vertical-cloud-lab/tensegrity-optimization/proposal-diff.tex

\documentclass[11pt]{article}
%DIF LATEXDIFF DIFFERENCE FILE
%DIF DEL /tmp/proposal-orig.tex   Mon Mar 16 17:47:02 2026
%DIF ADD proposal.tex             Mon Mar 16 17:11:21 2026

% --- Packages ---
\usepackage[margin=1in]{geometry}
\usepackage{amsmath,amssymb}
\usepackage{graphicx}
\usepackage[hidelinks]{hyperref}
\usepackage{natbib}
\usepackage{booktabs}
\usepackage{enumitem}
\usepackage{xcolor}
\usepackage{siunitx}
\usepackage{subcaption}
\usepackage{titlesec}
\usepackage{setspace}
\usepackage{wrapfig}

% --- Formatting ---
\titleformat{\section}{\normalfont\Large\bfseries}{\thesection}{1em}{}
\titleformat{\subsection}{\normalfont\large\bfseries}{\thesubsection}{1em}{}
\setlength{\parskip}{0.5em}
\setlength{\parindent}{0em}

% --- Draft helpers (remove for final) ---
\newcommand{\todo}[1]{\textcolor{red}{\textbf{[TODO: #1]}}}
\newcommand{\note}[1]{\textcolor{blue}{\textbf{[NOTE: #1]}}}
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
\providecommand{\DIFdelFL}[1]{\DIFdel{#1}} %DIF PREAMBLE
\providecommand{\DIFaddbeginFL}{} %DIF PREAMBLE
\providecommand{\DIFaddendFL}{} %DIF PREAMBLE
\providecommand{\DIFdelbeginFL}{} %DIF PREAMBLE
\providecommand{\DIFdelendFL}{} %DIF PREAMBLE
%DIF HYPERREF PREAMBLE %DIF PREAMBLE
\providecommand{\DIFadd}[1]{\texorpdfstring{\DIFaddtex{#1}}{#1}} %DIF PREAMBLE
\providecommand{\DIFdel}[1]{\texorpdfstring{\DIFdeltex{#1}}{}} %DIF PREAMBLE
\newcommand{\DIFscaledelfig}{0.5}
%DIF HIGHLIGHTGRAPHICS PREAMBLE %DIF PREAMBLE
\RequirePackage{settobox} %DIF PREAMBLE
\RequirePackage{letltxmacro} %DIF PREAMBLE
\newsavebox{\DIFdelgraphicsbox} %DIF PREAMBLE
\newlength{\DIFdelgraphicswidth} %DIF PREAMBLE
\newlength{\DIFdelgraphicsheight} %DIF PREAMBLE
% store original definition of \includegraphics %DIF PREAMBLE
\LetLtxMacro{\DIFOincludegraphics}{\includegraphics} %DIF PREAMBLE
\newcommand{\DIFaddincludegraphics}[2][]{{\color{blue}\fbox{\DIFOincludegraphics[#1]{#2}}}} %DIF PREAMBLE
\newcommand{\DIFdelincludegraphics}[2][]{% %DIF PREAMBLE
\sbox{\DIFdelgraphicsbox}{\DIFOincludegraphics[#1]{#2}}% %DIF PREAMBLE
\settoboxwidth{\DIFdelgraphicswidth}{\DIFdelgraphicsbox} %DIF PREAMBLE
\settoboxtotalheight{\DIFdelgraphicsheight}{\DIFdelgraphicsbox} %DIF PREAMBLE
\scalebox{\DIFscaledelfig}{% %DIF PREAMBLE
\parbox[b]{\DIFdelgraphicswidth}{\usebox{\DIFdelgraphicsbox}\\[-\baselineskip] \rule{\DIFdelgraphicswidth}{0em}}\llap{\resizebox{\DIFdelgraphicswidth}{\DIFdelgraphicsheight}{% %DIF PREAMBLE
\setlength{\unitlength}{\DIFdelgraphicswidth}% %DIF PREAMBLE
\begin{picture}(1,1)% %DIF PREAMBLE
\thicklines\linethickness{2pt} %DIF PREAMBLE
{\color[rgb]{1,0,0}\put(0,0){\framebox(1,1){}}}% %DIF PREAMBLE
{\color[rgb]{1,0,0}\put(0,0){\line( 1,1){1}}}% %DIF PREAMBLE
{\color[rgb]{1,0,0}\put(0,1){\line(1,-1){1}}}% %DIF PREAMBLE
\end{picture}% %DIF PREAMBLE
}\hspace*{3pt}}} %DIF PREAMBLE
} %DIF PREAMBLE
\LetLtxMacro{\DIFOaddbegin}{\DIFaddbegin} %DIF PREAMBLE
\LetLtxMacro{\DIFOaddend}{\DIFaddend} %DIF PREAMBLE
\LetLtxMacro{\DIFOdelbegin}{\DIFdelbegin} %DIF PREAMBLE
\LetLtxMacro{\DIFOdelend}{\DIFdelend} %DIF PREAMBLE
\DeclareRobustCommand{\DIFaddbegin}{\DIFOaddbegin \let\includegraphics\DIFaddincludegraphics} %DIF PREAMBLE
\DeclareRobustCommand{\DIFaddend}{\DIFOaddend \let\includegraphics\DIFOincludegraphics} %DIF PREAMBLE
\DeclareRobustCommand{\DIFdelbegin}{\DIFOdelbegin \let\includegraphics\DIFdelincludegraphics} %DIF PREAMBLE
\DeclareRobustCommand{\DIFdelend}{\DIFOaddend \let\includegraphics\DIFOincludegraphics} %DIF PREAMBLE
\LetLtxMacro{\DIFOaddbeginFL}{\DIFaddbeginFL} %DIF PREAMBLE
\LetLtxMacro{\DIFOaddendFL}{\DIFaddendFL} %DIF PREAMBLE
\LetLtxMacro{\DIFOdelbeginFL}{\DIFdelbeginFL} %DIF PREAMBLE
\LetLtxMacro{\DIFOdelendFL}{\DIFdelendFL} %DIF PREAMBLE
\DeclareRobustCommand{\DIFaddbeginFL}{\DIFOaddbeginFL \let\includegraphics\DIFaddincludegraphics} %DIF PREAMBLE
\DeclareRobustCommand{\DIFaddendFL}{\DIFOaddendFL \let\includegraphics\DIFOincludegraphics} %DIF PREAMBLE
\DeclareRobustCommand{\DIFdelbeginFL}{\DIFOdelbeginFL \let\includegraphics\DIFdelincludegraphics} %DIF PREAMBLE
\DeclareRobustCommand{\DIFdelendFL}{\DIFOaddendFL \let\includegraphics\DIFOincludegraphics} %DIF PREAMBLE
%DIF COLORLISTINGS PREAMBLE %DIF PREAMBLE
\RequirePackage{listings} %DIF PREAMBLE
\RequirePackage{color} %DIF PREAMBLE
\lstdefinelanguage{DIFcode}{ %DIF PREAMBLE
%DIF DIFCODE_UNDERLINE %DIF PREAMBLE
  moredelim=[il][\color{red}\sout]{\%DIF\ <\ }, %DIF PREAMBLE
  moredelim=[il][\color{blue}\uwave]{\%DIF\ >\ } %DIF PREAMBLE
} %DIF PREAMBLE
\lstdefinestyle{DIFverbatimstyle}{ %DIF PREAMBLE
	language=DIFcode, %DIF PREAMBLE
	basicstyle=\ttfamily, %DIF PREAMBLE
	columns=fullflexible, %DIF PREAMBLE
	keepspaces=true %DIF PREAMBLE
} %DIF PREAMBLE
\lstnewenvironment{DIFverbatim}{\lstset{style=DIFverbatimstyle}}{} %DIF PREAMBLE
\lstnewenvironment{DIFverbatim*}{\lstset{style=DIFverbatimstyle,showspaces=true}}{} %DIF PREAMBLE
%DIF END PREAMBLE EXTENSION ADDED BY LATEXDIFF

\begin{document}

% --- Cover Page (does not count toward 5-page limit) ---
\input{sections/coverpage}

% =============================================================================
\section{Research Motivation and Overview}
% =============================================================================

We propose a two-year \textbf{experiment-driven} mentored research program in
which 2 undergraduate students design, fabricate, and test \textbf{multi-material
3D-printed tensegrity-inspired structures} for energy absorption.  Tensegrity
structures---assemblies of rigid compression members
suspended within a continuous network of tension members---exhibit remarkable
strength-to-weight ratios and tunable mechanical responses, making them
attractive for protective equipment, packaging, and aerospace applications
\citep{skelton2009tensegrity}.
Recent work has shown that \emph{tensegrity-inspired} architectures can be
directly 3D-printed and retain desirable load-limiting behavior under impact
\citep{pajunen2019design}.  Because multimaterial FDM TPU elements are not
ideal cables, we target architectures that reproduce key
tensegrity-like mechanical responses while remaining manufacturable; notably,
TPU's rate-dependent damping is an \emph{asset} for energy absorption rather
than merely a deviation from idealized behavior.

% --- Overview figure (right-inset, floatable) ---
\begin{wrapfigure}{R}{0.62\textwidth}
\centering
\vspace{-1em}
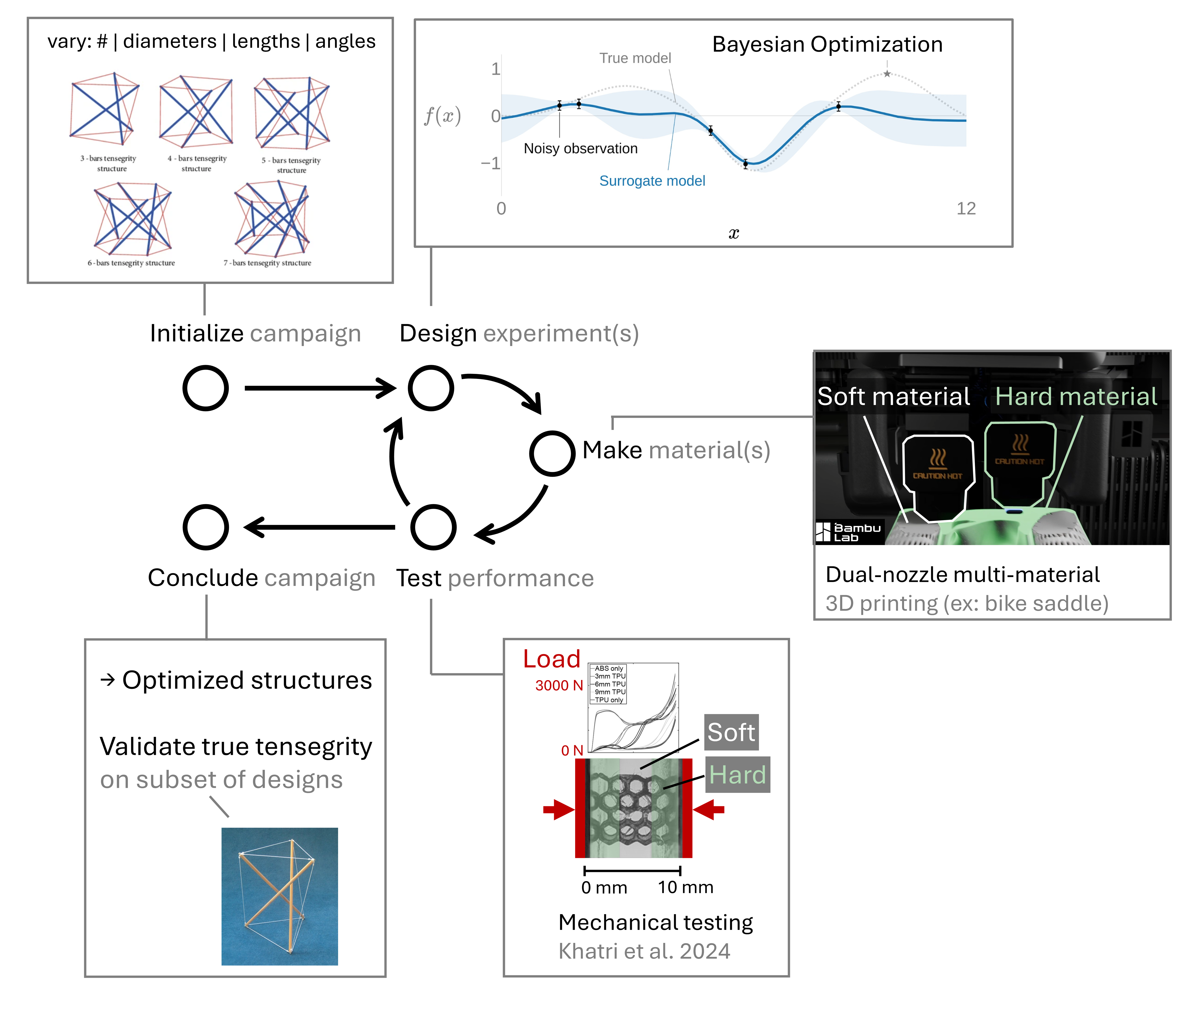
[picture p4: figures/overview-updated.png]

\captionsetup{font=small}
\caption{Research framework overview. Students design, print, and test tensegrity-inspired specimens in a closed-loop Bayesian optimization cycle that recommends the next designs to fabricate. Performance is evaluated via quasi-static compression and drop-weight impact tests.}
\label{fig:overview}
\end{wrapfigure}

Multi-material 3D printing with PLA (rigid struts) and TPU (flexible tension
elements) enables rapid fabrication of diverse tensegrity-inspired geometries
\citep{ye2023multimaterial, khatri2024energy}.  Rather
than relying on costly simulations, we leverage this manufacturing
agility for a \textbf{high-throughput experimental approach}: students
will print, test, and iterate on many candidate designs---we estimate 50--100+
unique specimens over two years---generating high-quality physical data
directly.  \textbf{Bayesian optimization} (BO) will guide the experimental
search, selecting the most informative designs to test next based on
prior results \citep{shahriari2016taking, frazier2018tutorial}.  This
experiment-first strategy produces reliable performance data while
keeping the project accessible to undergraduates where students can
contribute meaningfully through hands-on printing and testing without
advanced modeling expertise.

\textbf{A primary objective is to provide a rich,
interdisciplinary mentored research experience for undergraduates.}  Through
weekly one-on-one mentoring, structured lab meetings, and progressive
scaffolding from guided tasks to independent research
ownership, each student will gain skills in CAD, multi-material 3D
printing, mechanical testing, and data-driven optimization. Each student will define design variables, execute experimental campaigns, analyze data, present results, and draft manuscript sections.

% =============================================================================
\section{Background}
% =============================================================================

\textbf{Tensegrity structures} consist of isolated compression members (struts)
held in equilibrium by a continuous network of tension members
\citep{skelton2009tensegrity, sultan2009tensegrity}.  Their defining
characteristic---no two rigid bars touch---yields lightweight assemblies with
surprising load-bearing capacity and tunable nonlinear responses
\citep{amendola2014experimental, zhang2018tensegrity}.
Pajunen et al.\ \citep{pajunen2019design} demonstrated that
\emph{tensegrity-inspired} unit cells can be directly 3D-printed and exhibit
load-limiting plateaus under drop-weight impact.
Multi-material rigid--soft printing
\citep{ye2023multimaterial, khatri2024energy} has shown that PLA--TPU
combinations on a single FDM platform achieve tunable energy
absorption via a wrapping-based strategy (rigid cores
encapsulated by continuous soft skins) that prevents interface delamination and
enables cyclic durability---a critical enabler for our fabrication approach.

\textbf{Bayesian optimization} (BO) is a sequential, model-based strategy for
optimizing expensive black-box functions using a Gaussian process surrogate
\citep{shahriari2016taking, frazier2018tutorial}.  BO has driven breakthroughs
across domains---from tuning hyperparameters of AlphaGo
\citep{silver2016mastering} to optimizing sustainable concrete formulations
\citep{ament2023sustainable} and discovering organic laser
emitters \citep{striethkalthoff2024delocalized}---and has been applied to
metamaterial design \citep{mo2023accelerated}.  In our framework, BO operates
\emph{directly on experimental data}: each round of printing and testing
updates a Gaussian process surrogate, which recommends the next designs to fabricate.  This closed-loop
print--test--optimize cycle eliminates the need for simulation and
keeps the workflow centered on physical experimentation---naturally suited to mentoring undergraduates.

% =============================================================================
\section{Student Research Project~1: Design, Fabrication, and Testing}
% =============================================================================

\textbf{Student profile:} One sophomore or junior undergraduate.  No prior
simulation or advanced modeling experience is required; the hands-on nature of
this project makes it an ideal entry point for students early in their studies.

\subsection*{Scope and Deliverables}

This student will lead the design-and-build cycle that forms the experimental
backbone of the project.  Working under weekly mentoring from
Prof.~Hill, the student will \textbf{parameterize a family of
tensegrity-inspired unit cells} in CAD (SolidWorks or Fusion~360), defining key
variables---strut diameter and length (PLA), tension-element cross-section
(TPU), connectivity topology, and unit-cell tiling---that span the design space.
Following \citet{ye2023multimaterial}, the designs use a core-wrapping strategy
(rigid PLA struts encapsulated by continuous TPU skins) to ensure robust
mechanical interlocking. PLA--TPU interface robustness will be validated during early print trials.

The student will then \textbf{fabricate structures} using the department's
multi-material FDM printer, iterating on print parameters
to achieve reliable geometries.
The student works closely with Student~2, who tests each
batch and returns performance data.
Prof.~Baird's master's student serves as a day-to-day co-mentor,
guiding equipment operation and troubleshooting.

\textbf{Mentoring outcomes:} The student will develop skills in CAD,
multi-material additive manufacturing, and systematic experimental design.
Structured mentoring scaffolds move the student from guided replication of
existing designs to independent creation of novel geometries by mid-Year~1.
The student will present results at \textbf{UCUR} or \textbf{ASME IDETC} and
contribute as co-author on a journal manuscript.

% =============================================================================
\section{Student Research Project~2: Mechanical Testing and Data-Driven Optimization}
% =============================================================================

\textbf{Student profile:} One sophomore, junior, or senior undergraduate with
coursework or interest in mechanics of materials or data analysis.

\subsection*{Scope and Deliverables}

This student will lead physical testing and the Bayesian optimization
campaign, working under weekly one-on-one mentoring from Prof.~Baird.  The work
begins with \textbf{experimental testing} on structures fabricated by
Student~1: quasi-static compaction and drop-weight impact tests following
\citet{pajunen2019design}.  Primary metrics include \emph{peak transmitted
force}, \emph{specific energy absorption} (SEA), and \emph{compaction
efficiency}.

With initial data in hand, the student will \textbf{implement a BO loop}
(BoTorch/Ax) that operates directly
on experimental measurements.  After each iteration the surrogate recommends
the next batch of designs; the student coordinates with Student~1 to print and
test them, closing the loop.  If time permits,
lightweight simulations may be added as a low-fidelity data
source to accelerate convergence \citep{mo2023accelerated}, but the campaign
does not depend on simulation.

Prof.~Baird's master's student provides day-to-day co-mentoring in Python,
data analysis, and BO implementation.
In Year~2, both students mentor newly recruited undergraduates, reinforcing
their own understanding while sustaining the research pipeline.

\textbf{Mentoring outcomes:} The student will develop skills in experimental
mechanics (test design, data acquisition), scientific computing (Python),
and data-driven optimization.  They will present results at \textbf{ASME IDETC}
or \textbf{UCUR} and contribute as co-author on a journal manuscript.

% =============================================================================
\section{Mentoring Environment}
\label{sec:mentoring}
% =============================================================================

Each student follows a structured path from guided exploration
to independent research ownership, supported by layered mentoring.
Because the project centers on hands-on experimentation---designing,
printing, and testing physical structures---students engage with tangible
problems from day one.

\subsection*{Recruitment}

Students will be recruited from courses in mechanics of materials, machine
design, kinematics, and compliant mechanisms, targeting sophomores through
seniors.  The experiment-driven nature of the project lowers the barrier to
entry: students need not have prior simulation or programming experience.

\subsection*{Mentoring Structure}

Students meet individually with Profs.~Hill and Baird each week (30~min) for
technical guidance and professional development, and participate in weekly lab
group meetings (1~hr) that include progress updates, literature
presentations, and skill-building workshops on scientific writing,
presentation skills, and research ethics.  Prof.~Baird's master's student
serves as a graduate co-mentor, providing day-to-day guidance in 3D printing,
testing, coding, and data interpretation.
Students begin with structured tasks---replicating known tensegrity
geometries and running standard test protocols---and progress to independent
design decisions, culminating in ownership of their research project. Year~1 focuses on skill acquisition and guided execution; Year~2 emphasizes independent hypothesis generation, experimental design, and peer mentoring of newly recruited sophomores.

\subsection*{Student Development Outcomes}

Mentoring is structured around concrete milestones:
a student's first successful multi-material print, first compression test,
first data set fed into the BO loop.  \emph{Technical} skills include
experimental mechanics, additive manufacturing (CAD, multi-material 3D printing),
and data-driven optimization (Python, Bayesian optimization).
\emph{Communication} skills develop through lab notebooks, group presentations,
conference talks, and co-authoring a peer-reviewed manuscript.
\emph{Professional} development includes project management, data-driven
decision-making, interdisciplinary collaboration, and preparation for graduate
school or industry careers.

% =============================================================================
\section{Expected Research Outcomes}
% =============================================================================

The primary outcome is the \textbf{training of 2 undergraduate
researchers} with hands-on experience in multi-material 3D printing, mechanical
testing, and data-driven optimization. Each undergraduate is expected to have
participated in the design and testing of approximately 100+ tensegrity
specimens, contributed to \textbf{conference presentations} at UCUR
and ASME IDETC, and co-authored a peer-reviewed manuscript
submitted to the \emph{ASME Journal of Mechanical Design} or \emph{Smart
Materials and Structures}. The
experimental data set---spanning a wide range of tensegrity-inspired geometries
with measured energy-absorption performance---will be published on GitHub
for reproducibility.  In Year~2, students will
mentor incoming undergraduates, developing leadership skills and creating a
self-sustaining research group.

% =============================================================================
\section{Potential Impact of Work}
% =============================================================================

This project advances architected material design for energy absorption with
applications in \textbf{protective equipment} (helmets, body armor),
\textbf{packaging} (shock-absorbing inserts), and \textbf{aerospace}
(lightweight impact-resistant structures).  The systematically collected
experimental data set provides the community with a resource for benchmarking
and further optimization.  The experiment-driven BO framework
demonstrates that undergraduates can drive a closed-loop
experimental campaign, establishing a replicable mentoring model for
data-driven research.  Open-source dissemination of data, code, and tested designs extends
impact beyond BYU.

% =============================================================================
\section{Timeline}
% =============================================================================

The project spans two academic years plus two summers (Table~\ref{tab:timeline}).
\textbf{Year~1} focuses on experimental foundations: recruitment and
onboarding in Fall, literature review and CAD parameterization through Winter, and a Summer term of full-time research with intensive
mentoring where students ramp up
fabrication, run systematic compression and impact
tests, and begin feeding results into the BO loop.
\textbf{Year~2} shifts to optimization and dissemination: BO-guided
campaigns continue through Fall and Winter with progressively refined designs.  Students present at UCUR
and ASME IDETC, and a journal manuscript is prepared during Winter
and Summer.  Experienced students mentor newly recruited
undergraduates throughout Year~2.

\begin{table}[ht]
\centering
\small
\begin{tabular}{@{}lccccccc@{}}
\toprule
\textbf{Task} & \textbf{Y1 F} & \textbf{Y1 W} & \textbf{Y1 Su} & \textbf{Y2 F} & \textbf{Y2 W} & \textbf{Y2 Su} \\
\midrule
Student recruitment \& onboarding    & \(\bullet\) &           &           &           &           &           \\
Literature review                     & \(\bullet\) & \(\bullet\) &           &           &           &           \\
Tensegrity parameterization \& CAD   & \(\bullet\) & \(\bullet\) &           &           &           &           \\
Print trials \& process validation   & \(\bullet\) & \(\bullet\) & \(\bullet\) &           &           &           \\
Multi-material 3D printing campaigns &             & \(\bullet\) & \(\bullet\) & \(\bullet\) & \(\bullet\) &           \\
Compression \& impact testing        &             & \(\bullet\) & \(\bullet\) & \(\bullet\) & \(\bullet\) &           \\
Bayesian optimization loop           &             &             & \(\bullet\) & \(\bullet\) & \(\bullet\) &           \\
Conference presentations (UCUR/IDETC)&             &             &             & \(\bullet\) & \(\bullet\) &           \\
Journal manuscript preparation       &             &             &             &             & \(\bullet\) & \(\bullet\) \\
Peer mentoring of new students       &             &             &             & \(\bullet\) & \(\bullet\) &           \\
\bottomrule
\end{tabular}
\caption{Project timeline across two years (F = Fall, W = Winter, Su = Summer).  Summer terms support full-time research with intensive mentoring. Year 2 includes formal peer mentoring, where experienced students supervise newly recruited undergraduates.}
\label{tab:timeline}
\end{table}

% =============================================================================
\section{Budget}
% =============================================================================

\input{sections/budget}

% =============================================================================
% --- References (do not count toward 5-page limit) ---
\bibliographystyle{plainnat}
\bibliography{references}

% --- Bio Sketches (do not count toward 5-page limit) ---
\newpage
\input{sections/biosketch}

\end{document}
