vertical-cloud-lab/tensegrity-optimization/idetc-abstract.tex

\documentclass[10pt]{article}

% --- Packages ---
\usepackage[letterpaper,margin=0.6in]{geometry}
\usepackage[hidelinks]{hyperref}
\usepackage{parskip}
\usepackage{graphicx}
\usepackage{caption}
\usepackage{titlesec}
\usepackage{wrapfig}
\usepackage[numbers,sort&compress]{natbib}

% --- Formatting ---
\setlength{\parskip}{0.2em}
\setlength{\parindent}{0em}
\titleformat*{\section}{\large\bfseries}
\titleformat*{\subsection}{\normalsize\bfseries\itshape}
\titlespacing*{\section}{0pt}{0.4em}{0.1em}
\titlespacing*{\subsection}{0pt}{0.25em}{0.05em}
\setlength{\emergencystretch}{2em}
\setlength{\intextsep}{0.2em}
\bibliographystyle{abbrvnat}

\begin{document}

\begin{center}
{\Large\textbf{Closed-Loop Bayesian Optimization of Multi-Material\\
3D-Printed Tensegrity-Inspired Energy Absorbers}}\\[0.4em]
\textit{Extended Abstract --- ASME IDETC-CIE 2026}\\
\textit{Track DAC-10: Design of Engineering Materials and Structures}
\end{center}

\vspace{0.4em}

\section*{Abstract}
Tensegrity-inspired architectures---rigid struts suspended within a
continuous flexible network---can exhibit tunable nonlinear
force--displacement responses and favorable energy absorption per unit
mass, motivating their use in lightweight energy-absorbing and protective
structures
\citep{skelton2009tensegrity,pajunen2019design}.
Multi-material fused deposition modeling (FDM) can co-print rigid (PLA)
struts and flexible (TPU) elements in a single build
\citep{ye2023multimaterial,khatri2024energy}, but the resulting design
space---strut geometry, tension-element cross-section, connectivity
topology, and unit-cell tiling---is too large to explore by trial and
error. We present a closed-loop experimental campaign that uses
Bayesian optimization (BO) \citep{shahriari2016taking}
to drive a design--print--test workflow operating directly on physical
measurements, without relying on calibrated finite-element simulation
for objective evaluation.

\section{Introduction and Motivation}

\begin{wrapfigure}{r}{0.65\textwidth}
\centering
\vspace{-0.4em}

\captionsetup{font=small}
\caption{Closed-loop, BO-driven design--print--test workflow.
Candidate tensegrity-inspired unit cells are instantiated from a
parameter vector, fabricated by multi-material FDM, and tested under
quasi-static compression and drop-weight impact. Measured peak force,
specific energy absorption (SEA), and compaction efficiency update a
Gaussian-process surrogate that proposes the next batch of designs.}
\label{fig:overview}
\vspace{-0.4em}
\end{wrapfigure}

Tensegrity structures combine compression-only members with a
pre-tensioned tension network to achieve stiffness without rigid
joinery~\citep{skelton2009tensegrity}. Their
nonlinear, often load-limiting force--displacement response makes them
attractive for impact mitigation, packaging, and wearable protective
gear~\citep{pajunen2019design}. Idealized
cable--strut tensegrities are difficult to manufacture at scale, but
\emph{tensegrity-inspired} architectures fabricated by single-material
3D printing reproduce key tensegrity behaviors---including
post-buckling stability and load-limiting force--displacement
response~\citep{pajunen2019design}---motivating our extension to
multi-material FDM for monolithic co-fabrication of rigid and flexible
elements. PLA provides rigid struts; TPU provides flexible,
rate-dependent tension elements whose viscoelasticity is expected to
contribute hysteretic energy dissipation under impact loading,
consistent with the energy-absorbing behavior reported for rigid--TPU
multi-material prints~\citep{khatri2024energy}.

The challenge is that small geometric and topological changes can
produce large changes in the measured response, and high-fidelity
simulation of FDM specimens is computationally expensive and often
struggles to capture physical defects such as interfacial slip and
TPU rate-dependence~\citep{mo2023accelerated}. Pure
trial-and-error sweeps over the joint design space are also infeasible:
even modest parameter resolutions yield thousands of candidates, each
requiring print and test time. We instead treat the physical
experiment as the source of truth and use BO to select which specimens
are most informative to fabricate next---an approach used in related
closed-loop materials and structures
campaigns~\citep{mo2023accelerated,low2024evolution}.
Unlike prior tensegrity-inspired studies that evaluate a fixed design
set~\citep{pajunen2019design,khatri2024energy}, we adaptively select
designs using parallel, noisy multi-objective BO driven by measured
$F_{\mathrm{peak}}$, SEA, and $\eta$.

\section{Approach}
\subsection{Closed-Loop Workflow}
Figure~\ref{fig:overview} summarizes the campaign. Each iteration
proceeds in four steps: (i)~a parameterized unit-cell design is
instantiated from a candidate vector $\mathbf{x}$; (ii)~the specimen
is sliced and printed on a multi-material FDM system; (iii)~it is
tested under quasi-static compression and instrumented drop-weight
impact; and (iv)~the resulting performance metrics update a
Gaussian-process (GP) surrogate, which a batch acquisition function
queries to recommend the next set of candidates. Surrogate updating
and experiment selection are automated; specimen handling, slicing,
and test setup remain manual.

\subsection{Design Space}
We parameterize a family of unit cells using a core-wrapping
architecture in which rigid PLA struts are enclosed by continuous TPU
skins; the wrapping rationale follows multi-material FDM strategies in
which rigid panels are wrapped by stretchable soft material to prevent
delamination and improve interfacial bonding at the rigid--flexible
interface~\citep{ye2023multimaterial}. The design vector $\mathbf{x}$
comprises continuous geometric variables (strut diameter and length,
tension-element width and thickness), an integer strut count per unit
cell, and two categorical variables (connectivity topology, unit-cell
tiling pattern). Categorical choices are encoded explicitly rather
than embedded in a continuous metric, and bounds on the continuous
variables are chosen to remain within the printer's resolution and
overhang limits and to keep specimens in a common form factor for the
test fixtures.

\subsection{Surrogate and Acquisition}
The GP surrogate is trained on three measured performance metrics:
peak transmitted force $F_\mathrm{peak}$, specific energy absorption
(SEA), and compaction efficiency $\eta$. We use independent GPs per
objective with Mat\'ern kernels; hyperparameters are fit by marginal
likelihood with priors to avoid pathological length scales at small $n$.
Heteroscedastic noise from TPU batch-to-batch variation and FDM
interfacial defects motivates our use of q-noisy expected hypervolume
improvement (qNEHVI), which explicitly accounts for observation noise
in parallel multi-objective BO~\citep{daulton2021nehvi}, over standard
expected-improvement variants. Print failures are treated as a
probabilistic feasibility constraint: the acquisition score for each
candidate is its qNEHVI improvement weighted by the GP-estimated
probability of successful fabrication, following recent constrained
multi-objective practice in self-driving labs~\citep{low2024evolution}.
Where applicable, we use numerically stable log-space variants of
improvement-based acquisitions to mitigate vanishing-gradient
pathologies as data and constraints
accumulate~\citep{ament2023logei}.

\section{Methods}
\subsection{Fabrication}
Specimens are fabricated on a multi-material FDM system capable of
co-printing PLA and TPU within a single build~\citep{ye2023multimaterial}.
Print parameters (temperature, line width, infill, retraction) are
held fixed within a batch to isolate the effect of the design
variables. Each specimen is weighed and dimensionally inspected prior
to testing so that mass and geometric deviations are available as
covariates.

\subsection{Mechanical Testing}
Quasi-static compression is performed on a screw-driven load frame at
a fixed nominal strain rate, with force--displacement recorded to
densification. Drop-weight impact testing uses an instrumented tup at
a fixed impact energy; transmitted force is captured at high sample
rate, and specimens are imaged before and after impact to document
failure modes. From each test we extract $F_\mathrm{peak}$, SEA per
unit mass, and compaction efficiency $\eta$, defined consistently
across the campaign. A control specimen from an earlier batch is
retested periodically to monitor TPU batch-to-batch and printer drift.

\section{Expected Outcomes and Discussion}
We will report how BO-selected designs evolve across iterations, how
GP surrogate predictions and uncertainties change as data accumulate,
and which Pareto-efficient trade-offs emerge between SEA and peak
transmitted force within the explored design space. We will also
discuss practical lessons for operating the closed-loop workflow,
including handling of print failures, batch-to-batch variability in
TPU response, the influence of the rigid--flexible interface on
energy absorption, and the exploration--exploitation balance of the
acquisition function under realistic experimental noise. We expect
the campaign to clarify where physical experimentation is genuinely
required versus where simpler analytical or multi-fidelity surrogate
shortcuts~\citep{mo2023accelerated} could be
substituted in future work.

\section{Conclusion}
This work demonstrates a partially automated, experiment-driven
closed-loop pipeline for designing multi-material 3D-printed
tensegrity-inspired energy absorbers, with surrogate updating and
candidate selection automated and fabrication and testing kept manual.
By updating a GP surrogate directly from physical measurements, the
workflow avoids direct dependence on calibrated finite-element
simulation for objective evaluation while still providing principled,
multi-objective design recommendations. The same closed-loop pattern is
expected to transfer to other multi-material additively manufactured
architectures whose performance is dominated by hard-to-simulate
effects.

{\tiny
\renewcommand{\bibsection}{\section*{\normalsize References}\vspace{-0.5em}}
\setlength{\bibsep}{-0.05em plus 0.1ex}
% Render DOIs as clickable doi.org hyperlinks for easy spot-checking;
% keep \url{} as a clickable hyperlink (default natbib behavior).
\providecommand{\doi}[1]{}
\renewcommand{\doi}[1]{\href{https://doi.org/#1}{doi:\,#1}}
\bibliography{references}
}

\end{document}
