vertical-cloud-lab/tensegrity-optimization/bo/t3-prism-bo-round5-plate-recipe.md

# Round-5 print recipe

Generated by `python bo/t3_prism_bo_campaign.py --round 5 --batch-number 5`. Every article is specified at 20.23 g as printed; the scale column is what gets that mass at that article's own strut infill, so a sparse article is a larger one.

## Filament settings, one value for the whole batch

- PLA at 223 C and 24.7 mm^3/s (133 mm/s at the profile's 0.62 x 0.30 mm bead)
- TPU at 240 C and 3.0 mm^3/s (16 mm/s)

These four are filament settings, so a print job carries exactly one value of each. Set them once and print every plate of this batch with them: formally they are the print parameters of trial 55, the batch's best-predicted specimen, applied everywhere. Every batch prints at one filament point, so the batch-level points measured so far are confounded with everything else that changed between rounds; a model-preferred setting is therefore not identified, and the values continue the seeded Sobol sequence over the bounds (see the README) rather than being asked of the model.

The two infill densities are per part, set by right-clicking the part in the object list and adding a sparse infill density override: the `-struts` part runs on extruder 1 (PLA), the `-cables` part on extruder 2 (TPU). Without those overrides both parts inherit the one global value and the batch loses its two per-article process axes.

Articles whose end-cap radius comes out below 20.1 mm are flagged `end cap`. That is the smallest article printed so far, and the three igloo mounts and three key-seats are absolute-size, so check in the slicer that they still fit before printing.

## Plate 1 (9 articles, the whole batch)

- Packing: 249 x 249 mm of the usable 290 x 310 mm.

| trial | struts infill | cables infill | scale | R (mm) | H (mm) | strut Ø (mm) | cable Ø (mm) | footprint Ø (mm) | flags |
|---|---|---|---|---|---|---|---|---|---|
| 55 | 25 % | 20 % | 0.8281 | 20.71 | 90.98 | 4.97 | 4.54 | 51.1 | best predicted |
| 56 | 22 % | 19 % | 0.8565 | 34.25 | 66.05 | 9.08 | 2.57 | 77.2 | cable < 3.0 mm |
| 57 | 28 % | 14 % | 0.8287 | 20.72 | 91.07 | 4.97 | 4.51 | 51.1 | ok |
| 58 | 23 % | 24 % | 0.8320 | 20.82 | 89.49 | 4.99 | 4.58 | 51.4 | ok |
| 59 | 22 % | 13 % | 0.8909 | 35.03 | 63.68 | 8.99 | 2.67 | 79.2 | cable < 3.0 mm |
| 60 | 26 % | 23 % | 0.8312 | 20.78 | 91.36 | 4.99 | 4.50 | 51.2 | ok |
| 61 | 32 % | 20 % | 0.8319 | 20.80 | 91.51 | 4.99 | 4.43 | 51.2 | ok |
| 62 | 23 % | 22 % | 0.8401 | 21.15 | 86.31 | 5.04 | 4.62 | 52.1 | ok |
| 63 | 24 % | 22 % | 0.8402 | 33.61 | 66.10 | 9.06 | 2.52 | 75.8 | cable < 3.0 mm |
