vertical-cloud-lab/tensegrity-optimization/bo/t3-prism-bo-round4-plate-recipe.md

# Round-4 print recipe

Generated by `python bo/t3_prism_bo_campaign.py --round 4 --batch-number 4`. Every article is specified at 20.23 g as printed; the scale column is what gets that mass at that article's own strut infill, so a sparse article is a larger one.

Update 2026-09-08: the print files exist. `slices/t3-prism-bo-round4.H2D-MM-PLAstruts-TPUcables.3mf` carries everything below already baked in (both filament settings and all 18 per-part infill overrides, one object per trial), so this recipe is now a checklist to verify on import rather than values to type by hand: confirm each part's settings list shows "Sparse infill density" with its per-article value, then paint the supports on. The per-trial STLs are under `per-specimen-stls/`, and the README's "Round-4 print files" section records the verification. See `t3-prism-bo-round4-designs.csv` for the manifest.

## Filament settings, one value for the whole batch

- PLA at 226 C and 29.5 mm^3/s (159 mm/s at the profile's 0.62 x 0.30 mm bead)
- TPU at 236 C and 2.6 mm^3/s (14 mm/s)

These four are filament settings, so a print job carries exactly one value of each. Set them once and print every plate of this batch with them: formally they are the print parameters of trial 37, the batch's best-predicted specimen, applied everywhere. Every batch prints at one filament point, so the batch-level points measured so far are confounded with everything else that changed between rounds; a model-preferred setting is therefore not identified, and the values continue the seeded Sobol sequence over the bounds (see the README) rather than being asked of the model.

The two infill densities are per part, set by right-clicking the part in the object list and adding a sparse infill density override: the `-struts` part runs on extruder 1 (PLA), the `-cables` part on extruder 2 (TPU). Without those overrides both parts inherit the one global value and the batch loses its two per-article process axes.

Articles whose end-cap radius comes out below 20.1 mm are flagged `end cap`. That is the smallest article printed so far, and the three igloo mounts and three key-seats are absolute-size, so check in the slicer that they still fit before printing.

## Plate 1 (9 articles, the whole batch)

- Packing: 263 x 263 mm of the usable 290 x 310 mm.

| trial | struts infill | cables infill | scale | R (mm) | H (mm) | strut Ø (mm) | cable Ø (mm) | footprint Ø (mm) | flags |
|---|---|---|---|---|---|---|---|---|---|
| 37 | 22 % | 21 % | 0.8586 | 34.34 | 67.12 | 8.98 | 2.58 | 77.4 | cable < 3.0 mm, best predicted |
| 38 | 18 % | 34 % | 0.7303 | 18.26 | 80.34 | 7.98 | 4.02 | 45.1 | end cap |
| 39 | 21 % | 34 % | 0.8674 | 34.70 | 68.30 | 8.86 | 2.60 | 78.2 | envelope > 250 cm3, cable < 3.0 mm |
| 40 | 18 % | 21 % | 0.8329 | 20.82 | 91.62 | 5.00 | 4.58 | 51.4 | ok |
| 41 | 29 % | 18 % | 0.8356 | 33.42 | 67.29 | 8.65 | 2.51 | 75.4 | cable < 3.0 mm |
| 42 | 19 % | 34 % | 0.7060 | 17.65 | 77.66 | 8.47 | 3.88 | 43.6 | end cap |
| 43 | 12 % | 29 % | 0.9274 | 37.09 | 65.47 | 9.25 | 2.78 | 83.6 | envelope > 250 cm3, cable < 3.0 mm |
| 44 | 19 % | 21 % | 0.8320 | 20.80 | 91.52 | 4.99 | 4.58 | 51.3 | ok |
| 45 | 12 % | 35 % | 0.7861 | 19.65 | 86.47 | 6.89 | 4.32 | 48.5 | end cap |
