vertical-cloud-lab/tensegrity-optimization/bo/t3-prism-bo-round3-plate-recipe.md

# Round-3 print recipe

Generated by `python bo/t3_prism_bo_campaign.py --round 3 --batch-number 3`. Every article is specified at 20.23 g as printed; the scale column is what gets that mass at that article's own strut infill, so a sparse article is a larger one.

## Filament settings, one value for the whole batch

- PLA at 217 C and 20.5 mm^3/s (110 mm/s at the profile's 0.62 x 0.30 mm bead)
- TPU at 244 C and 3.6 mm^3/s (19 mm/s)

These four are filament settings, so a print job carries exactly one value of each. Set them once and print every plate of this batch with them: formally they are the print parameters of trial 32, the batch's best-predicted specimen, applied everywhere. With all 17 tested articles at a single point of the process space there is no data to prefer one setting over another, so the values were drawn by Sobol sampling within the bounds (see the README) rather than asked of the model.

**Before slicing, switch the TPU filament preset.** Both tested plates carry `Bambu TPU 85A @BBL H2D 0.4 nozzle`, left over from before the high-flow hotend went in, and it caps the temperature window at 240 C, below what this batch asks for. Switch to `Bambu TPU 85A @BBL H2D`, whose window is 200 to 250 C. Typing the number into the old preset is not the same thing.

The two infill densities are per part, set by right-clicking the part in the object list and adding a sparse infill density override: the `-struts` part runs on extruder 1 (PLA), the `-cables` part on extruder 2 (TPU). Without those overrides both parts inherit the one global value and the batch loses its two per-article process axes.

Articles whose end-cap radius comes out below 20.1 mm are flagged `end cap`. That is the smallest article printed so far, and the three igloo mounts and three key-seats are absolute-size, so check in the slicer that they still fit before printing.

## Plate 1 (9 articles, the whole batch)

- Packing: 218 x 218 mm of the usable 290 x 310 mm.

| trial | struts infill | cables infill | scale | R (mm) | H (mm) | strut Ø (mm) | cable Ø (mm) | footprint Ø (mm) | flags |
|---|---|---|---|---|---|---|---|---|---|
| 28 | 21 % | 29 % | 0.9292 | 23.23 | 55.75 | 5.58 | 5.11 | 57.3 | ok |
| 29 | 13 % | 31 % | 0.6955 | 27.82 | 76.50 | 8.35 | 3.83 | 63.8 | ok |
| 30 | 31 % | 18 % | 0.9202 | 23.01 | 55.21 | 5.52 | 5.06 | 56.8 | ok |
| 31 | 18 % | 21 % | 0.7530 | 20.74 | 65.07 | 9.04 | 4.14 | 50.3 | ok |
| 32 | 24 % | 13 % | 0.7471 | 29.89 | 60.57 | 8.10 | 4.11 | 68.5 | best predicted |
| 33 | 29 % | 16 % | 0.9229 | 23.07 | 55.37 | 5.54 | 5.08 | 56.9 | ok |
| 34 | 16 % | 34 % | 0.8690 | 21.72 | 52.14 | 8.81 | 4.78 | 53.6 | ok |
| 35 | 26 % | 24 % | 1.0136 | 25.34 | 60.82 | 9.02 | 3.04 | 61.0 | ok |
| 36 | 34 % | 26 % | 1.0352 | 25.88 | 62.11 | 8.27 | 3.11 | 62.3 | ok |
