vertical-cloud-lab/tensegrity-optimization/sections/budget.tex

% sections/budget.tex
% Budget justification for BYU Mentored Research Grant

Total requested: \textbf{\$25,000} over 2 years.  Per grant guidelines, no
funds are allocated to equipment, tuition, or faculty wages.

\begin{center}
{\small
\begin{tabular}{@{}llrr@{}}
\toprule
\textbf{Category} & \textbf{Description} & \textbf{Year 1} & \textbf{Year 2} \\
\midrule
Undergraduate wages
    & 2 students, part-time + summer full-time
    & \$10,000 & \$10,000 \\
Graduate student wages
    & Partial RA for grad co-mentor
    & \$1,250 & \$1,250 \\
Supplies
    & Filament, fasteners, consumables
    & \$750 & \$250 \\
Travel
    & Conference registration \& travel
    & \$0 & \$1,500 \\
\midrule
\textbf{Annual Total} & & \textbf{\$12,000} & \textbf{\$13,000} \\
\bottomrule
\end{tabular}
}
\end{center}

\textbf{Undergraduate wages (\$20,000):} Supports 2 undergraduates working
part-time ($\sim$10~hrs/week) during fall and winter semesters and
full-time ($\sim$40~hrs/week) during summer terms for design,
3D printing, and testing.
%
\textbf{Graduate student wages (\$2,500):} Prof.~Baird's master's student
serves as day-to-day co-mentor.
%
\textbf{Supplies (\$1,000):} PLA/TPU filament (sufficient for 50--100+
specimens), fasteners, poster printing, and other
consumables.
%
\textbf{Travel (\$1,500):} Student presentations at ASME IDETC or UCUR
(Year~2).
