vertical-cloud-lab/tensegrity-optimization/sections/coverpage.tex

% sections/coverpage.tex
% Cover page for BYU Mentored Research Grant Proposal

\thispagestyle{empty}
\begingroup
\setlength{\parskip}{0.2em}
\titlespacing*{\subsection}{0pt}{0.6em}{0.2em}

\begin{center}
{\Large \textbf{Mentored Research Grant (MRG)}}
\end{center}

% --- Project Title ---
\subsection*{Project Title}
Experiment-Driven Design of Multi-Material 3D-Printed Tensegrity Structures for Energy Absorption

% --- Principal Investigator(s) ---
\subsection*{Principal Investigator(s)}
\textbf{PI Name:} Jeffrey R.\ Hill \\
\textbf{PI Department:} Mechanical Engineering \\
\textbf{Co-PI:} Sterling G.\ Baird, Department of Mechanical Engineering

% --- Abstract ---
\subsection*{Abstract}

We propose a two-year experiment-driven mentored research program in which 2
undergraduate students design, fabricate, and test multi-material 3D-printed
tensegrity-inspired structures for energy absorption.  Using PLA for rigid
struts and TPU for flexible tension elements on a single FDM platform, students
will rapidly print and test many candidate geometries, generating
high-quality physical data.  A Bayesian optimization loop operating
directly on experimental measurements will guide the search toward optimal
energy-absorbing designs.  The project is structured around layered
mentoring---weekly one-on-one faculty meetings, lab group sessions, and
graduate co-mentoring---that progressively moves students from guided tasks
to independent research ownership.  Students will gain hands-on experience in
CAD design, multi-material 3D printing, mechanical testing, and data-driven
optimization.  Expected outcomes include undergraduate conference
presentations (UCUR, ASME IDETC), a peer-reviewed journal submission, and
development of transferable technical skills.  This project provides a rich
mentored learning environment at the intersection of structural mechanics,
advanced manufacturing, and machine learning.

% --- Number of Students ---
\subsection*{Number of Students to be Mentored}
\textbf{Number of Undergraduate Students:} 2 \\
\textbf{Number of Graduate Students:} 1 (co-mentor, in support of creating the mentoring environment)

% --- Budget ---
\subsection*{Budget}

\vspace{-0.5em}
\begin{center}
\begin{tabular}{@{}lrrr@{}}
\toprule
\textbf{Item} & \textbf{Year 1} & \textbf{Year 2} & \textbf{Total} \\
\midrule
Undergraduate wages    & \$10,000 & \$10,000 & \$20,000 \\
Graduate wages         & \$1,250  & \$1,250  & \$2,500  \\
Supplies               & \$750    & \$250    & \$1,000  \\
Travel                 & \$0      & \$1,500  & \$1,500  \\
\midrule
\textbf{Total}         & \textbf{\$12,000} & \textbf{\$13,000} & \textbf{\$25,000} \\
\bottomrule
\end{tabular}
\end{center}
\vspace{-0.5em}

% --- Relationship to External Funding ---
\subsection*{Relationship to External Funding}

The PIs do not currently hold external funding for tensegrity or architected
materials research.  This MRG provides the primary support for establishing a
mentored undergraduate research program in this area.  If successful, the
preliminary data may inform a future NSF proposal; however, the MRG is
self-contained and its outcomes do not depend on external funding.

\endgroup
\newpage
