vertical-cloud-lab/tensegrity-optimization/edison-trajectories/bo-objectives/bo-objectives-3e398131-d960-423d-97a2-32aa4db61ac1.md

The report is complete and commit-ready:

[Download `adversarial-objective-review.md`](data_entry:adversarial-objective-review-md-o43n)

Workspace path: `/workspace/edison-trajectories/bo-objectives/adversarial-objective-review.md`

## Decision

**Do not print the nine round-2 suggestions as-is.** Regenerate them after:

1. Removing `e_rebound` as a BO objective.
2. Optimizing `t180` alone, with input severity controlled.
3. Replacing per-drop SEM with article-level noise. The attached print study supports a **0.72% CV**, while the often-quoted **1.95% is a five-print range, not an SD**.
4. Reserving print capacity for independent replicate articles rather than nine entirely new geometries.

The current `t180` likelihood understates decision-relevant uncertainty by approximately **14–44× in SD** and **~200–1,900× in variance**, depending on specimen. The apparent `t180`-rebound trade-off is not robust: among the seven reliable articles, Pearson `r = -0.844` (`p = 0.017`), but Spearman `rho = -0.393` (`p = 0.383`); removing `6lhxfy` reduces these to `r = -0.429` and `rho = -0.029`.

`e_rebound = g t_second/(2 delta_v)` is a conditional **velocity ratio**, not an energy ratio. The bundle lacks synchronized video, a restrained/unrestrained test, or channel-resolved evidence proving that the delayed event consistently represents specimen ballistic flight rather than plate/carriage motion, rocking, or a ringdown-picker error.

I recommend a cheap intermediate validation: synchronized video plus CH2–CH5 waveforms for `6lhxfy` and `bpx68c`, each restrained and unrestrained, with at least five stabilized drops per condition. This gates whether rebound can later become a constraint; it should not delay correcting the GP and regenerating the batch.

The immutable data-only Section A is also stored at `/workspace/edison-trajectories/bo-objectives/SECTION_A_LOCKED.md`, SHA-256 `c1f43a8a1f913e0b8390d291b1a27ef780c49555131d8d3a915dde3b2d5aea64`.

## Discretionary analytical decisions

- Treated an independently printed article as the design-level replication unit.
- Used both Pearson and Spearman correlations plus leave-one-out sensitivity because the relationship was leverage-sensitive.
- Used the five-print 0.72% CV as the central fixed-noise floor, with 0.5%, 1%, and 2% sensitivity fits recommended because that study is confounded.
- Selected one-objective `t180` optimization rather than Pareto optimization because rebound lacks a validated estimand and engineering threshold.
- Recommended three articles × 10–12 analyzed drops as a pragmatic replication allocation; exact allocation should depend on the corrected acquisition and target effect size.
