vertical-cloud-lab/tensegrity-optimization/idetc-abstract-diff.pdf

## Closed-Loop Bayesian Optimization of Multi-Material 3D-Printed Tensegrity-Inspired Energy Absorbers

Extended Abstract — ASME IDETC-CIE 2026 Track DAC-10: Design of Engineering Materials and Structures

Abstract
Tensegrity-inspired architectures—rigid struts suspended within a continuous flexible network—can exhibit tunable nonlinear force–displacement responses and favorable energy absorption per unit mass, motivating their use in lightweight energy-absorbing and protective structures [1, 9]✿✿✿✿✿

[7, 9]. Multi-material fused deposition modeling (FDM) can co-print rigid (PLA) struts and flexible (TPU) elements in a single build [4, 10], but the resulting design space—strut geometry, tension-element cross-section, connectivity topology, and unit-cell tiling—is too large to explore by trial and error. We present a closed-loop experimental campaign that uses Bayesian optimization (BO) [8] to drive a design–print–test workflow operating directly on physical measurements, without relying on calibrated finite-element simulation for objective evaluation.

### 1 Introduction and Motivation

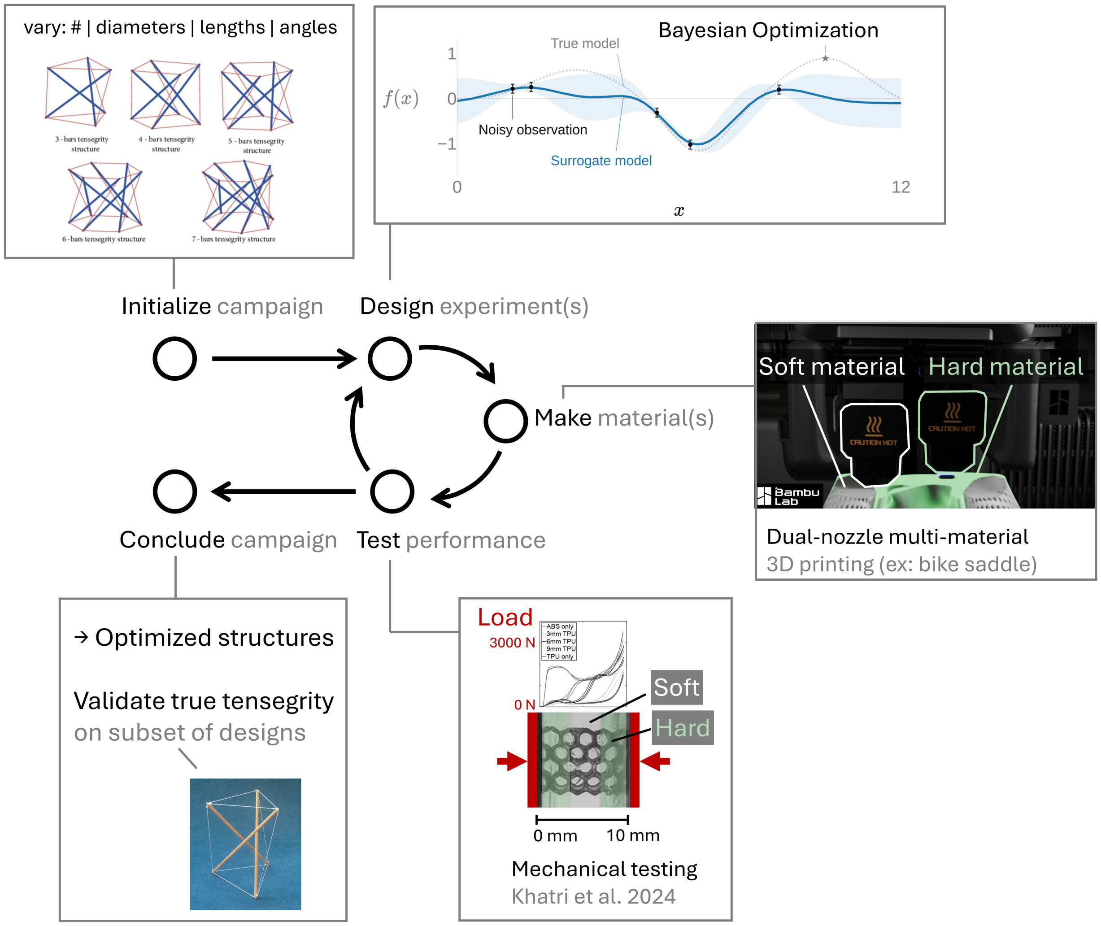
[picture p5: figure]

Figure 1: Closed-loop, BO-driven design–print–test workflow. Candidate tensegrity-inspired unit cells are instantiated from a parameter vector, fabricated by multimaterial FDM, and tested under quasi-static compression and drop-weight impact. Measured peak force, specific energy absorption (SEA), and compaction efficiency update a Gaussian-process surrogate that proposes the next batch of designs.

Tensegrity | structures | combine
compression-only members with a pretensioned tension network to achieve stiffness without rigid joinery [9]. Their nonlinear, often load-limiting force–
displacement | response | makes | them
attractive for impact mitigation, packaging, and wearable protective gear [1]

✿✿

[7]. Idealized cable–strut tensegrities are difficult to manufacture at scale,
but | tensegrity-inspired | architectures
fabricated by multi-material FDM can

✿✿✿✿✿✿✿✿✿✿✿✿✿

single-material ✿✿✿✿

3D ✿✿✿✿✿✿✿✿

printing✿

reproduce
key | tensegrity | behaviors—including
post-buckling stability and load-limiting
force–displacement | response—while
enabling | monolithic | fabrication | [7]

✿✿✿✿✿✿✿

response✿✿✿✿

[7]—motivating ✿✿✿✿✿✿✿✿✿✿✿✿✿✿✿ our ✿✿✿✿✿✿✿✿✿

extension

✿✿

to ✿✿✿✿✿✿✿✿✿✿✿✿✿ multi-material✿✿✿✿✿✿

FDM✿✿✿✿

for ✿✿✿✿✿✿✿✿✿✿ monolithic

✿✿✿✿✿✿✿✿✿✿✿✿

co-fabrication✿✿✿✿

of ✿✿✿✿✿✿
rigid ✿✿✿✿✿

and ✿✿✿✿✿✿✿✿

flexible

✿✿✿✿✿✿✿✿

elements. PLA provides rigid struts; TPU provides flexible, rate-dependent tension elements whose viscoelasticity is expected to contribute hysteretic energy dissipation under impact loading, consistent with the energy-absorbing behavior reported for rigid–TPU multi-material prints [4].
The challenge is that small geometric
and topological changes can produce
large changes in the measured response, and high-fidelity simulation of multi-material FDM specimens—including interfacial slip , print defects, and TPU rate-dependence—is expensive and often unreliable✿✿✿✿✿
FDM ✿✿✿✿✿✿✿✿✿✿

specimens ✿✿✿

is

✿✿✿✿✿✿✿✿✿✿✿✿✿✿

computationally✿✿✿✿✿✿✿✿✿✿

expensive✿✿✿✿✿

and ✿✿✿✿✿✿

often ✿✿✿✿✿✿✿✿✿
struggles✿✿✿

to✿✿✿✿✿✿✿✿

capture✿✿✿✿✿✿✿✿✿

physical✿✿✿✿✿✿✿

defects✿✿✿✿✿✿
such ✿✿✿

as✿✿✿✿✿✿✿✿✿✿

interfacial✿✿✿✿✿
slip✿✿✿✿✿

and ✿✿✿✿✿✿ TPU

✿✿✿✿✿✿✿✿✿✿✿✿✿✿

rate-dependence [6]. Pure trial-and-error sweeps over the joint design space are also infeasible: even modest parameter resolutions yield thousands of candidates, each requiring print and test time. We instead treat the physical experiment as the source of truth and use BO to select which specimens are most informative to fabricate next—an approach used in related closed-loop materials and structures campaigns [5, 6]. Unlike prior tensegrity-inspired studies that evaluate a fixed design set [4, 7], we adaptively select designs using parallel, noisy multi-objective BO driven by measured Fpeak, SEA, and η.

### 2 Approach

### 2.1 Closed-Loop Workflow

Figure 1 summarizes the campaign. Each iteration proceeds in four steps: (i) a parameterized unit-cell design is instantiated from a candidate vector x; (ii) the specimen is sliced and printed on a multi-material FDM system; (iii) it is tested under quasi-static compression and instrumented drop-weight impact; and (iv) the resulting performance metrics update a Gaussian-process (GP) surrogate, which a batch acquisition function queries to recommend the next set of candidates. Surrogate updating and experiment selection are automated; specimen handling, slicing, and test setup remain manual.

### 2.2 Design Space

We parameterize a family of unit cells using a core-wrapping architecture in which rigid PLA struts are enclosed by continuous TPU skins; the wrapping rationale follows multi-material FDM strategies in which rigid panels are wrapped by stretchable soft material to improve load transfer✿✿✿✿✿✿✿
prevent ✿✿✿✿✿✿✿✿✿✿✿✿

delamination ✿✿✿

and✿✿✿✿✿✿✿✿

improve ✿✿✿✿✿✿✿✿✿

interfacial✿✿✿✿✿✿✿
bonding✿

at the rigid–flexible
interface [10]. The design vector x includes ✿✿✿✿✿✿✿✿
comprises✿✿✿✿✿✿✿✿✿✿

continuous✿✿✿✿✿✿✿✿✿

geometric✿✿✿✿✿✿✿✿✿

variables ✿

(strut diameter and length, tension-element width and thickness, ✿✿

), ✿✿✿
an ✿✿✿✿✿✿

integer✿

strut count per unit cell, discrete ✿✿✿

and✿✿✿✿

two✿✿✿✿✿✿✿✿✿✿

categorical✿✿✿✿✿✿✿✿

variables✿✿

(connectivity
topology, and unit-cell tiling pattern, giving a mixed continuous–categorical space of roughly eight variables✿

). Categorical
choices (topology, tiling) are encoded explicitly rather than embedded in a continuous metric, and bounds on the continuous variables are chosen to remain within the printer’s resolution and overhang limits and to keep specimens in a common form factor for the test fixtures.

### 2.3 Surrogate and Acquisition

The GP surrogate is trained on three measured performance metrics: peak transmitted force Fpeak, specific energy absorption (SEA), and compaction efficiency η. We use independent GPs per objective with Mat´ern kernels; hyperparameters are fit by marginal likelihood with priors to avoid pathological length scales at small n. We use Heteroscedastic ✿✿✿✿✿✿✿✿✿✿✿✿✿✿✿✿✿✿✿ noise

✿✿✿✿

from✿✿✿✿✿ TPU✿✿✿✿✿✿✿✿✿✿✿✿✿✿
batch-to-batch ✿✿✿✿✿✿✿✿

variation✿✿✿✿

and✿✿✿✿✿

FDM✿✿✿✿✿✿✿✿✿✿

interfacial ✿✿✿✿✿✿

defects✿✿✿✿✿✿✿✿✿ motivates✿✿✿✿ our✿✿✿

use✿✿✿

of q-noisy expected hypervolume improvement (qNEHVI), which explicitly accounts for observation noise in parallel multi-objective BO [3], to select the next set of candidates✿✿✿✿
over ✿✿✿✿✿✿✿✿

standard✿✿✿✿✿✿✿✿✿✿✿✿✿✿✿✿✿✿✿✿✿

expected-improvement ✿✿✿✿✿✿✿✿ variants. Print failures are treated as a probabilistic feasibility constraintincorporated into constrained acquisition ✿
: ✿✿✿

the✿✿✿✿✿✿✿✿✿✿

acquisition✿✿✿✿✿

score✿✿✿

for✿✿✿✿✿
each ✿✿✿✿✿✿✿✿✿

candidate ✿✿

is ✿✿

its✿✿✿✿✿✿✿✿✿

qNEHVI ✿✿✿✿✿✿✿✿✿✿✿✿

improvement

✿✿✿✿✿✿✿✿ weighted ✿✿

by✿✿✿✿

the✿✿✿✿✿✿✿✿✿✿✿✿✿ GP-estimated ✿✿✿✿✿✿✿✿✿✿
probability✿✿

of✿✿✿✿✿✿✿✿✿

successful✿✿✿✿✿✿✿✿✿✿

fabrication, following recent constrained multi-objective practice in self-driving labs [5]. Where applicable, we use numerically stable log-space variants of improvement-based acquisitions to mitigate vanishing-gradient pathologies as data and constraints accumulate [2].

### 3 Methods

### 3.1 Fabrication

Specimens are fabricated on a multi-material FDM system capable of co-printing PLA and TPU within a single build [10]. Print parameters (temperature, line width, infill, retraction) are held fixed within a batch to isolate the effect of the design variables. Each specimen is weighed and dimensionally inspected prior to testing so that mass and geometric deviations are available as covariates.

### 3.2 Mechanical Testing

Quasi-static compression is performed on a screw-driven load frame at a fixed nominal strain rate, with force–displacement recorded to densification. Drop-weight impact testing uses an instrumented tup at a fixed impact energy; transmitted force is captured at high sample rate, and specimens are imaged before and after impact to document failure modes. From each test we extract Fpeak, SEA per unit mass, and compaction efficiency η, defined consistently across the campaign. A control specimen from an earlier batch is retested periodically to monitor TPU batch-to-batch and printer drift.

### 4 Expected Outcomes and Discussion

We will report how BO-selected designs evolve across iterations, how GP surrogate predictions and uncertainties change as data accumulate, and which Pareto-efficient trade-offs emerge between SEA and peak transmitted force within the explored design space. We will also discuss practical lessons for operating the closed-loop workflow, including handling of print failures, batch-to-batch variability in TPU response, the influence of the rigid–flexible interface on energy absorption, and the exploration–exploitation balance of the acquisition function under realistic experimental noise. We expect the campaign to clarify where physical experimentation is genuinely required versus where simpler analytical or multi-fidelity surrogate shortcuts [6] could be substituted in future work.

### 5 Conclusion

This work demonstrates a partially automated, experiment-driven closed-loop pipeline for designing multi-material 3D-printed tensegrity-inspired energy absorbers, with surrogate updating and candidate selection automated and fabrication and testing kept manual. By updating a GP surrogate directly from physical measurements, the workflow avoids direct dependence on calibrated finite-element simulation for objective evaluation while still providing principled, multi-objective design recommendations. The same closed-loop pattern is expected to transfer to other multi-material additively manufactured architectures whose performance is dominated by hard-to-simulate effects.

References

[1] A. Amendola, G. Carpentieri, M. C. de Oliveira, R. E. Skelton, and F. Fraternali. Experimental investigation of the softening–stiffening response of tensegrity prisms under compressive loading. Composite Structures, 117:234–243, 2014. doi: 10.1016/j.compstruct.2014.06.022. (https://doi.org/10.1016/j.compstruct.2014.06.022)
[2] S. Ament, S. Daulton, D. Eriksson, M. Balandat, and E. Bakshy. Unexpected improvements to expected improvement for Bayesian optimization. In Advances in Neural Information Processing Systems, volume 36, 2023. doi: 10.52202/075280-0904. (https://doi.org/10.52202/075280-0904)
[3] S. Daulton, M. Balandat, and E. Bakshy. | Parallel Bayesian optimization of multiple noisy objectives with expected hypervolume improvement. | In Advances in Neural
Information Processing Systems, volume 34, pages 2187–2200, 2021. URL https://arxiv.org/abs/2105.08195.
[4] N. R. Khatri and P. F. Egan. Energy absorption of 3D printed ABS and TPU multimaterial honeycomb structures. 3D Printing and Additive Manufacturing, 11:e840–e850, 2024. doi: 10.1089/3dp.2022.0196. (https://doi.org/10.1089/3dp.2022.0196)
[5] A. K. Y. Low, F. Mekki-Berrada, A. Ostudin, J. Xie, E. Vissol-Gaudin, Y.-F. Lim, A. Gupta, Q. Li, Y. S. Ong, S. A. Khan, and K. Hippalgaonkar. Evolution-guided Bayesian optimization for constrained multi-objective optimization in self-driving labs. npj Computational Materials, 10:1–11, 2024. doi: 10.1038/s41524-024-01274-x. (https://doi.org/10.1038/s41524-024-01274-x)
[6] C. Mo, P. Perdikaris, and J. R. Raney. Accelerated design of architected materials with multifidelity Bayesian optimization. Journal of Engineering Mechanics, 149(6):04023028, 2023. doi: 10.1061/JENMDT.EMENG-7033. (https://doi.org/10.1061/JENMDT.EMENG-7033)
[7] K. Pajunen, P. Johanns, R. K. Pal, J. J. Rimoli, and C. Daraio. Design and impact response of 3D-printable tensegrity-inspired structures. Materials & Design, 182:107966, 2019. doi: 10.1016/j.matdes.2019.107966. (https://doi.org/10.1016/j.matdes.2019.107966)
[8] B. Shahriari, K. Swersky, Z. Wang, R. P. Adams, and N. de Freitas. Taking the human out of the loop: A review of Bayesian optimization. Proceedings of the IEEE, 104(1): 148–175, 2016. doi: 10.1109/JPROC.2015.2494218. (https://doi.org/10.1109/JPROC.2015.2494218)
[9] R. E. Skelton and M. C. de Oliveira. Tensegrity Systems. Springer, New York, 2009. doi: 10.1007/978-0-387-74242-7. (https://doi.org/10.1007/978-0-387-74242-7)
[10] H. Ye, Q. Liu, J. Cheng, H. Li, B. Jian, R. Wang, Z. Sun, Y. Lu, and Q. Ge. Multimaterial 3D printed self-locking thick-panel origami metamaterials. Nature Communications, 14:1607, 2023. doi: 10.1038/s41467-023-37343-w. (https://doi.org/10.1038/s41467-023-37343-w)
