vertical-cloud-lab/tensegrity-optimization/bo/figures/t3-prism-bo-front-evolution.png

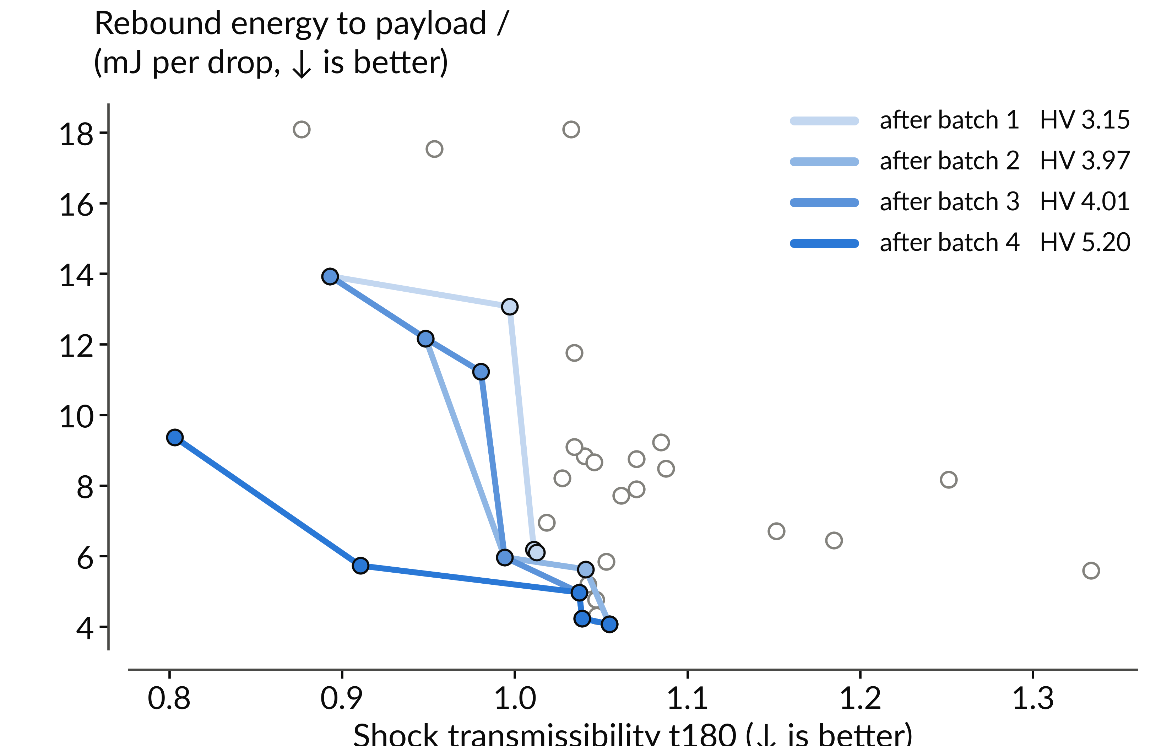
bo/figures/t3-prism-bo-front-evolution.png
