vertical-cloud-lab/tensegrity-optimization/bo/figures/t3-prism-bo-loocv-evolution-final.png

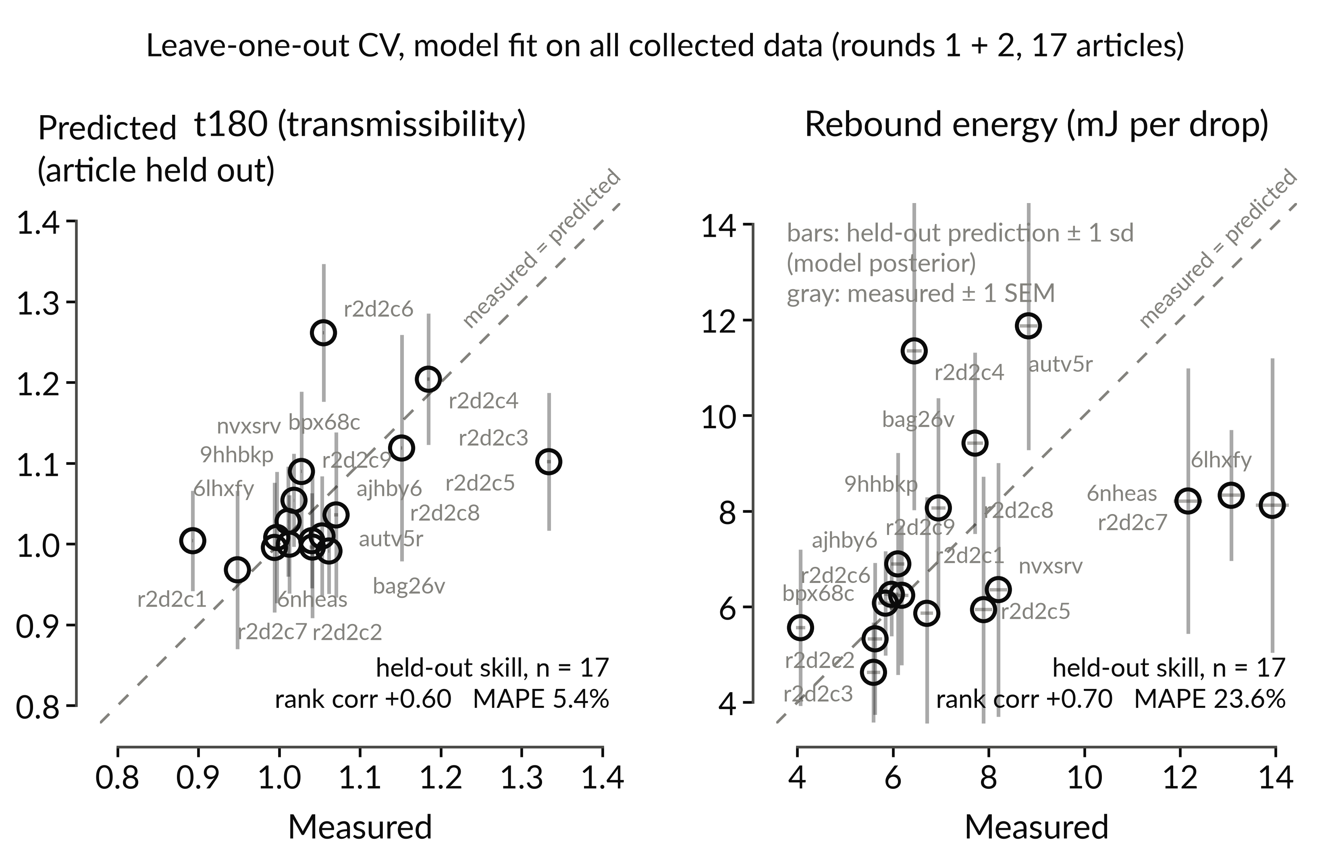
bo/figures/t3-prism-bo-loocv-evolution-final.png
