vertical-cloud-lab/tensegrity-optimization/bo/figures/t3-prism-bo-loocv-evolution-per-gram-shift.png

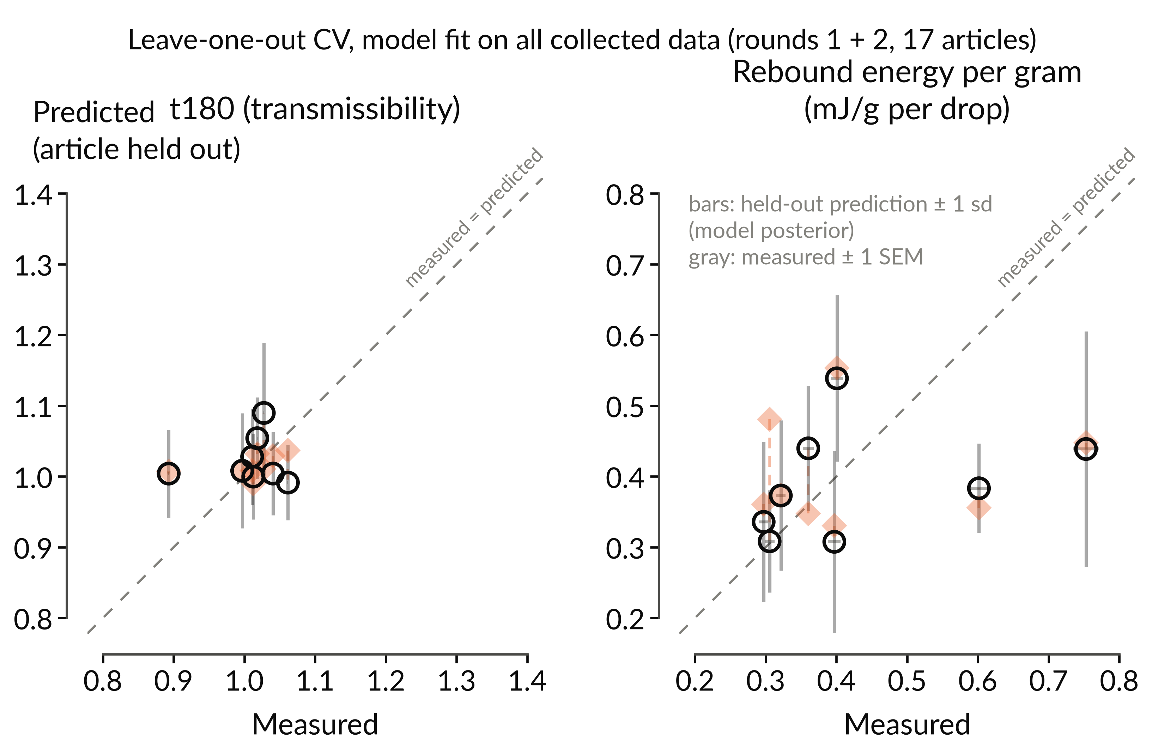
bo/figures/t3-prism-bo-loocv-evolution-per-gram-shift.png
