vertical-cloud-lab/tensegrity-optimization/bo/figures/t3-prism-bo-loocv-evolution-shift.png

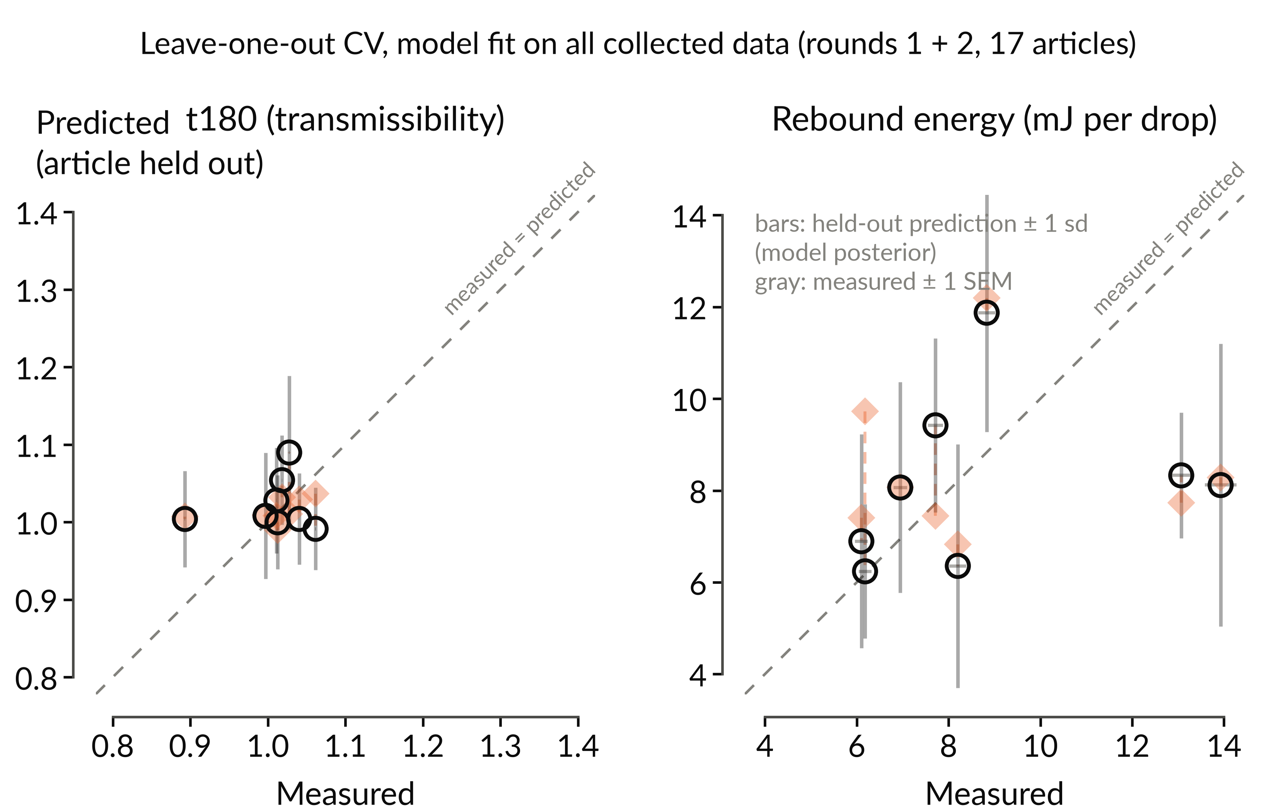
bo/figures/t3-prism-bo-loocv-evolution-shift.png
