vertical-cloud-lab/tensegrity-optimization/bo/figures/t3-prism-bo-loocv-evolution-start.png

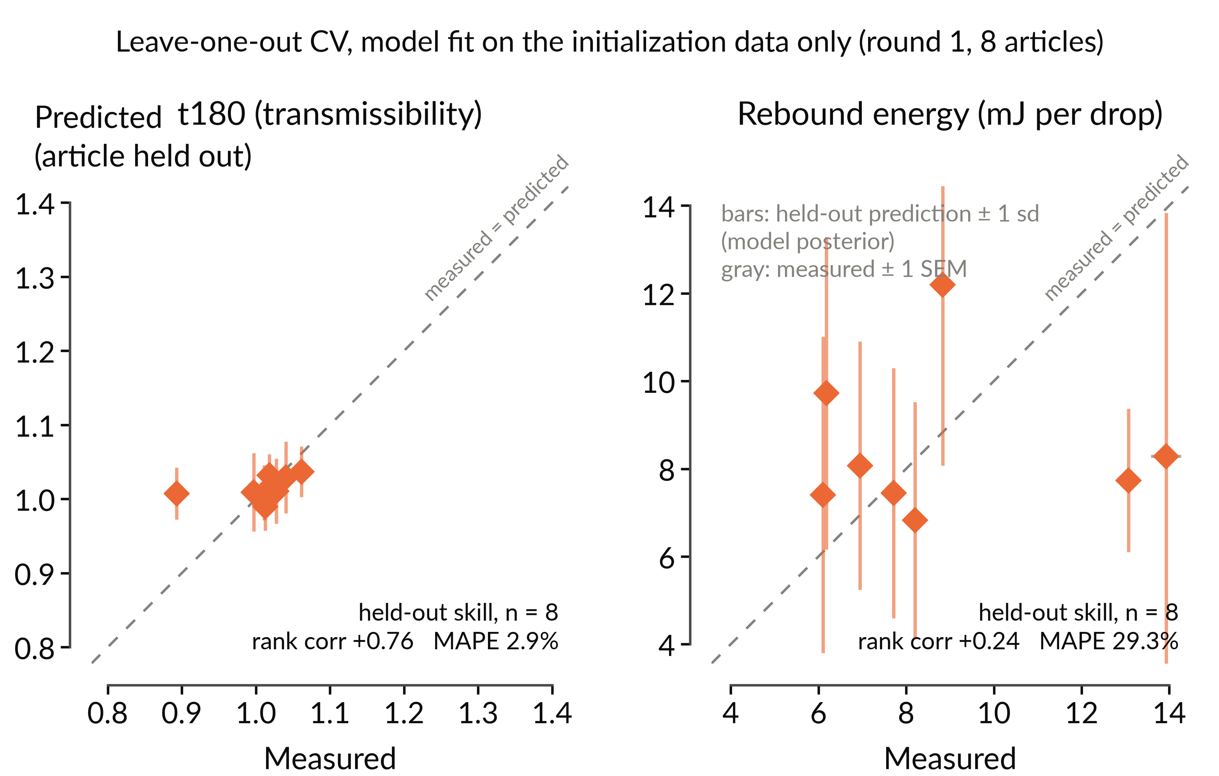
bo/figures/t3-prism-bo-loocv-evolution-start.png
