vertical-cloud-lab/tensegrity-optimization/bo/figures/t3-prism-bo-loocv-evolution.gif

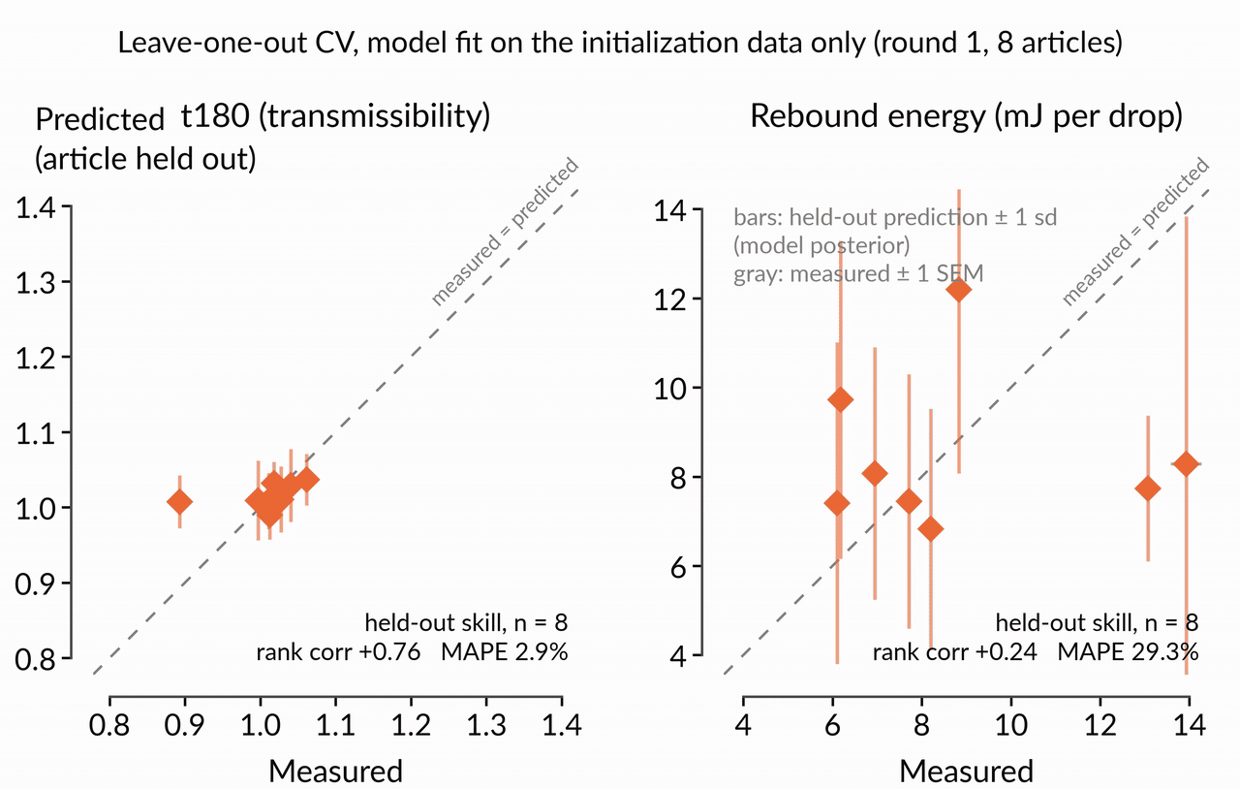
bo/figures/t3-prism-bo-loocv-evolution.gif
