vertical-cloud-lab/tensegrity-optimization/bo/figures/t3-prism-bo-round1-parameter-net-effects.png

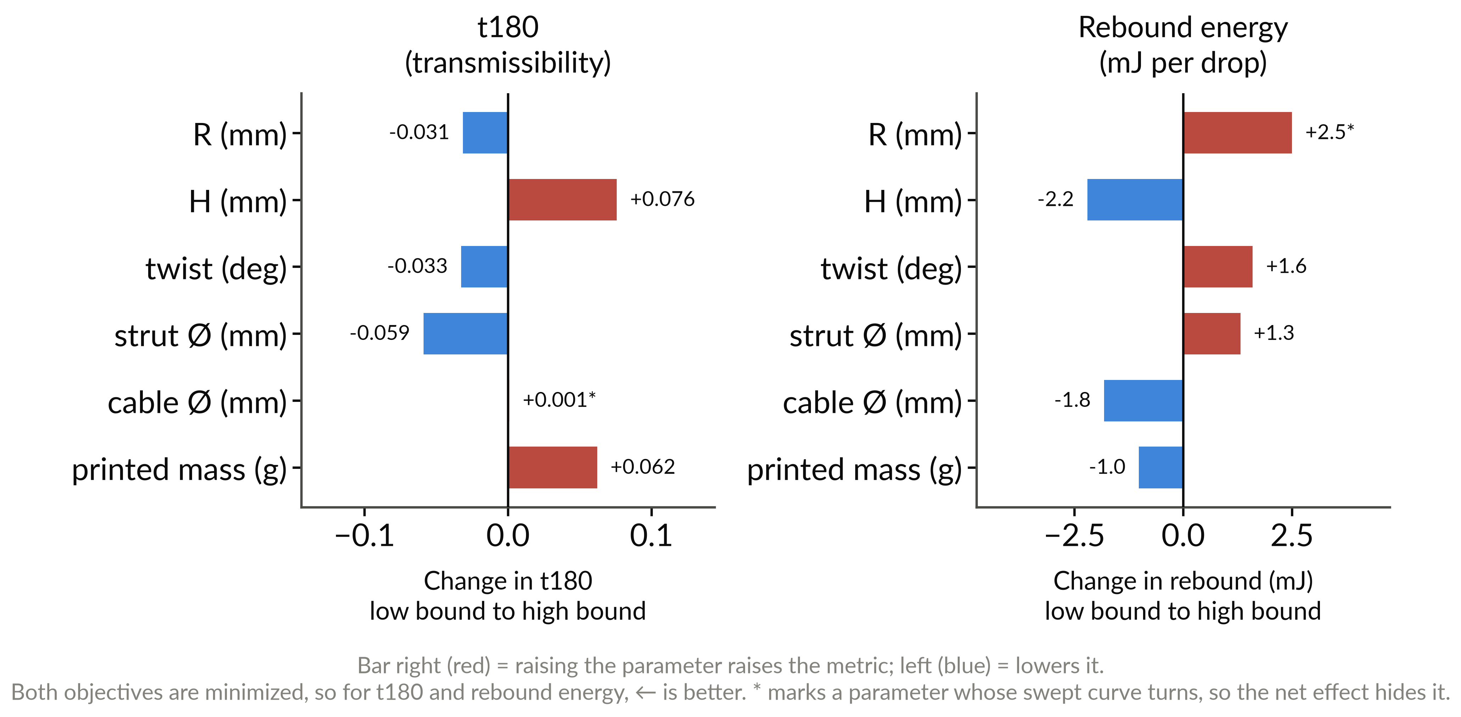
bo/figures/t3-prism-bo-round1-parameter-net-effects.png
