vertical-cloud-lab/tensegrity-optimization/bo/figures/t3-prism-bo-round1-pareto.png

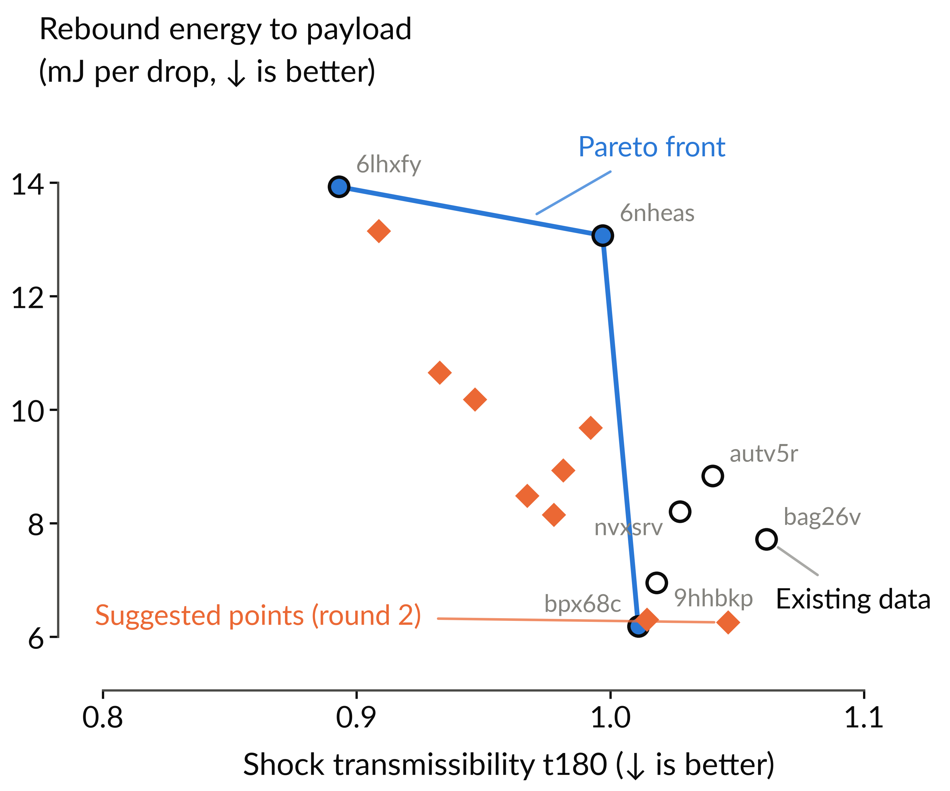
bo/figures/t3-prism-bo-round1-pareto.png
