vertical-cloud-lab/tensegrity-optimization/bo/figures/t3-prism-bo-round2-feature-importance.png

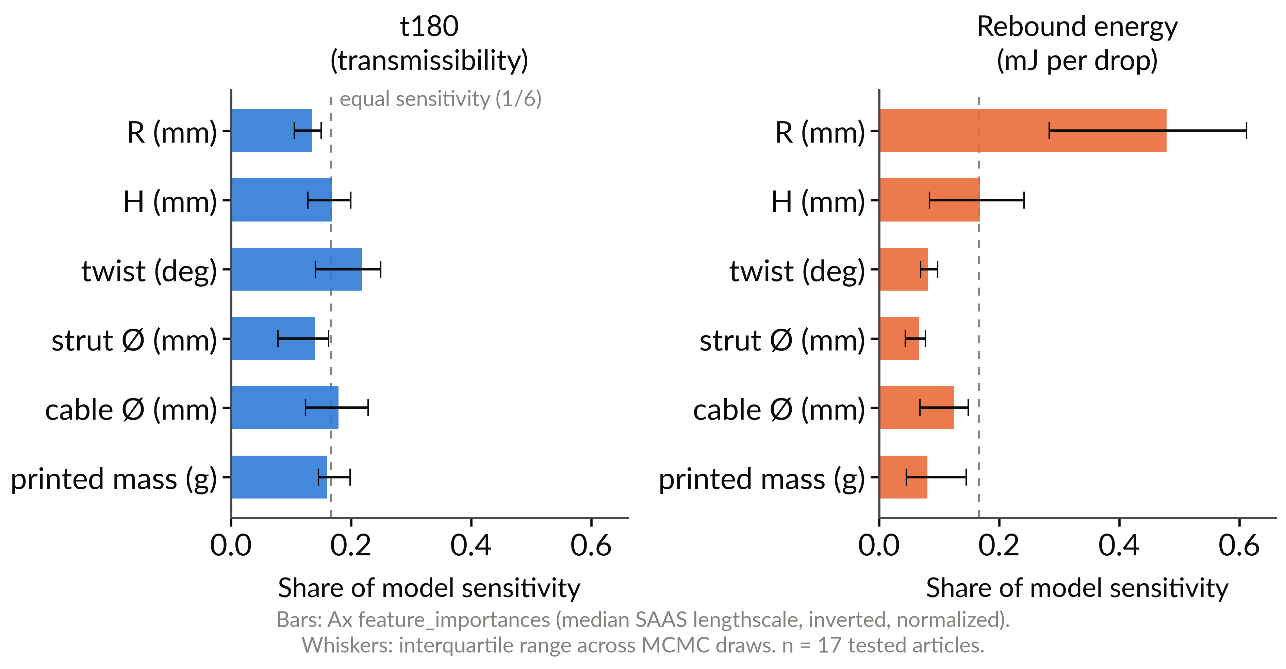
bo/figures/t3-prism-bo-round2-feature-importance.png
