vertical-cloud-lab/tensegrity-optimization/bo/figures/t3-prism-bo-round2-front-final.png

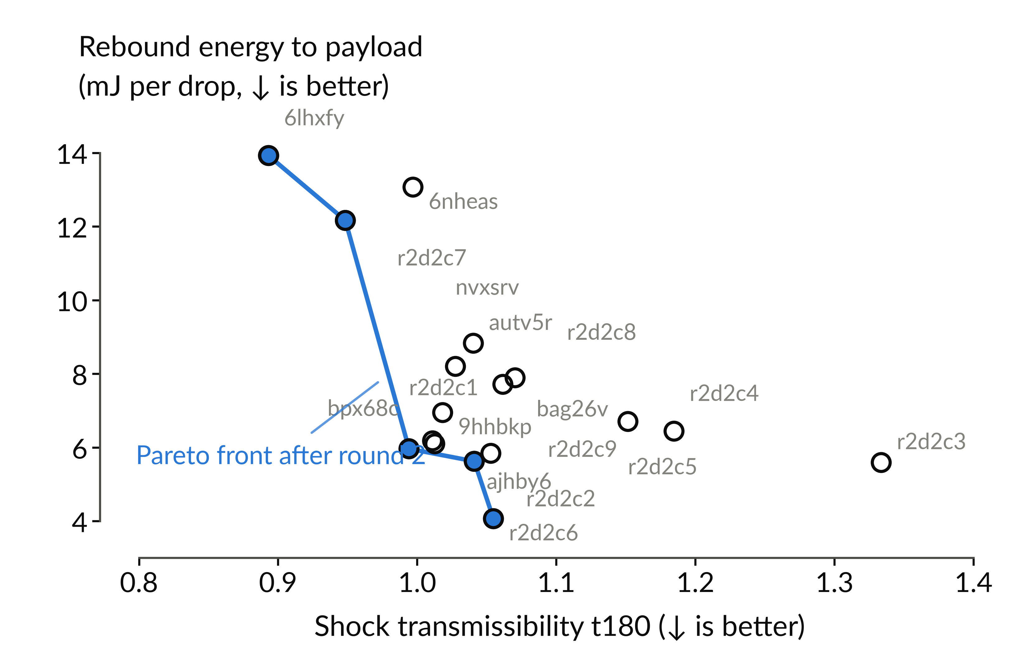
bo/figures/t3-prism-bo-round2-front-final.png
