vertical-cloud-lab/tensegrity-optimization/bo/figures/t3-prism-bo-round2-loocv-uncertainty.png

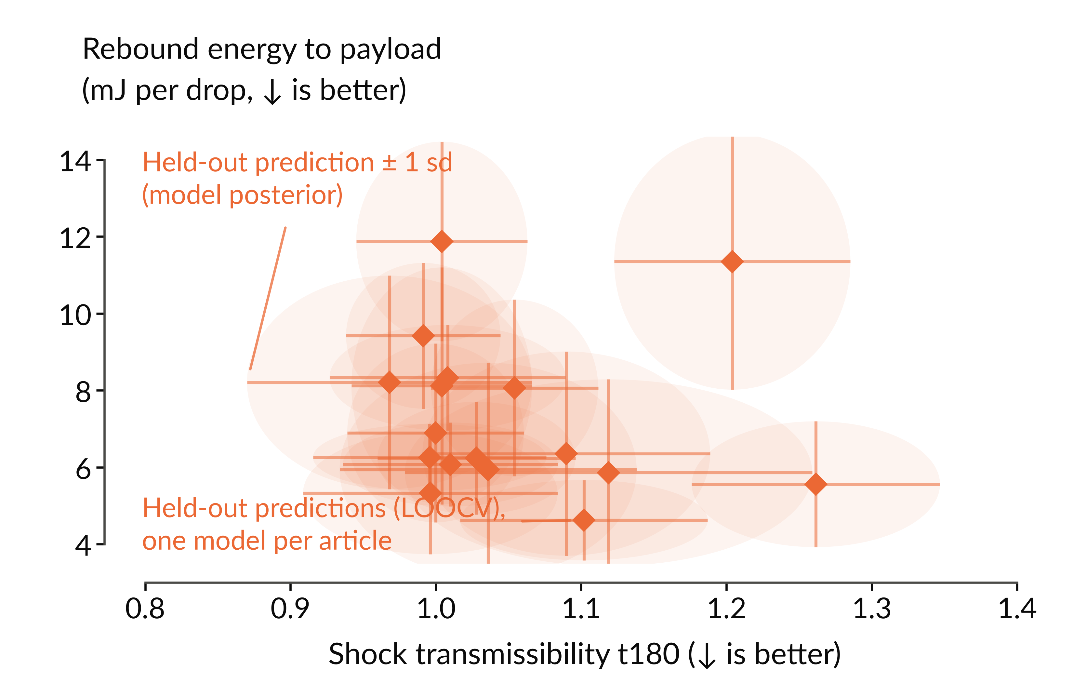
bo/figures/t3-prism-bo-round2-loocv-uncertainty.png
