vertical-cloud-lab/tensegrity-optimization/bo/figures/t3-prism-bo-round2-parity-final.png

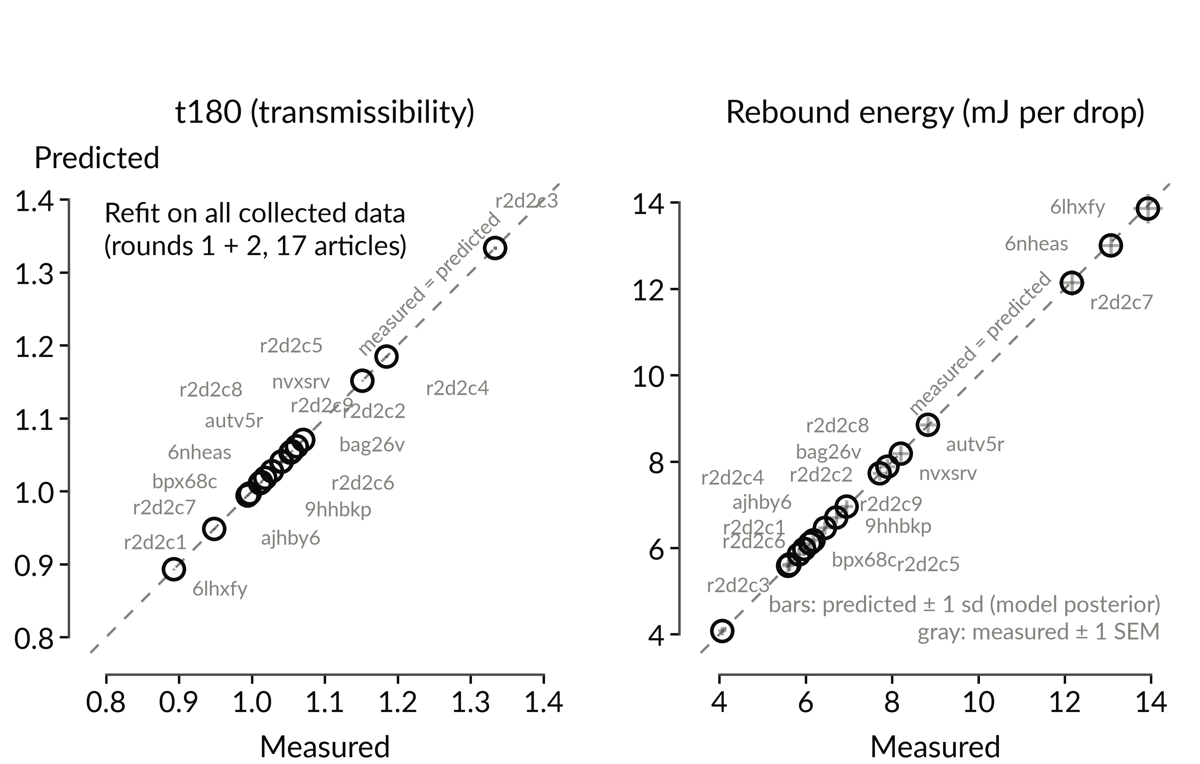
bo/figures/t3-prism-bo-round2-parity-final.png
