vertical-cloud-lab/tensegrity-optimization/bo/figures/t3-prism-bo-round2-parity-shift.png

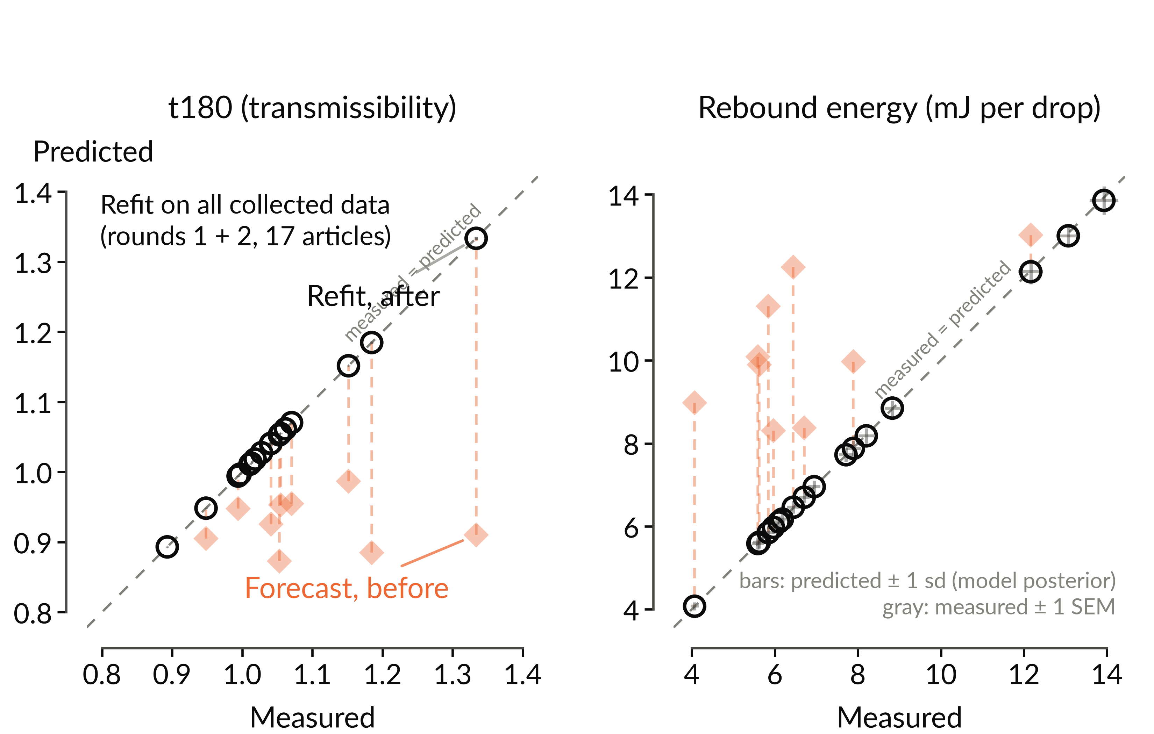
bo/figures/t3-prism-bo-round2-parity-shift.png
