vertical-cloud-lab/tensegrity-optimization/bo/figures/t3-prism-bo-round2-parity-start.png

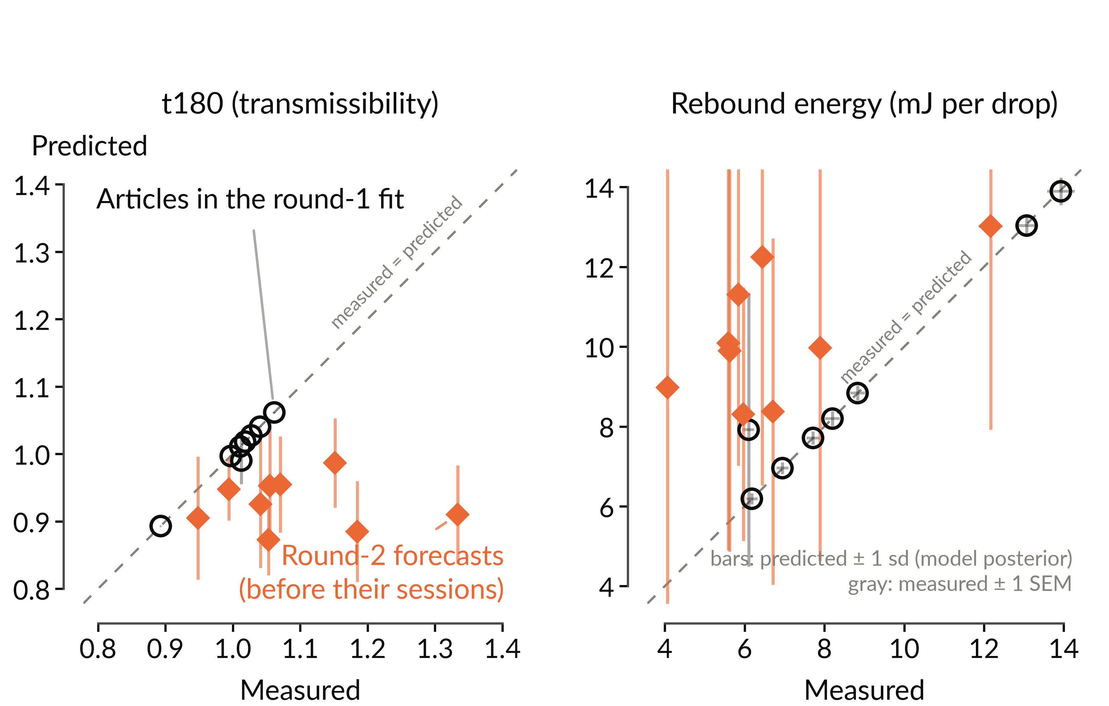
bo/figures/t3-prism-bo-round2-parity-start.png
