vertical-cloud-lab/tensegrity-optimization/bo/figures/t3-prism-bo-round2-predicted-vs-actual-per-gram.gif

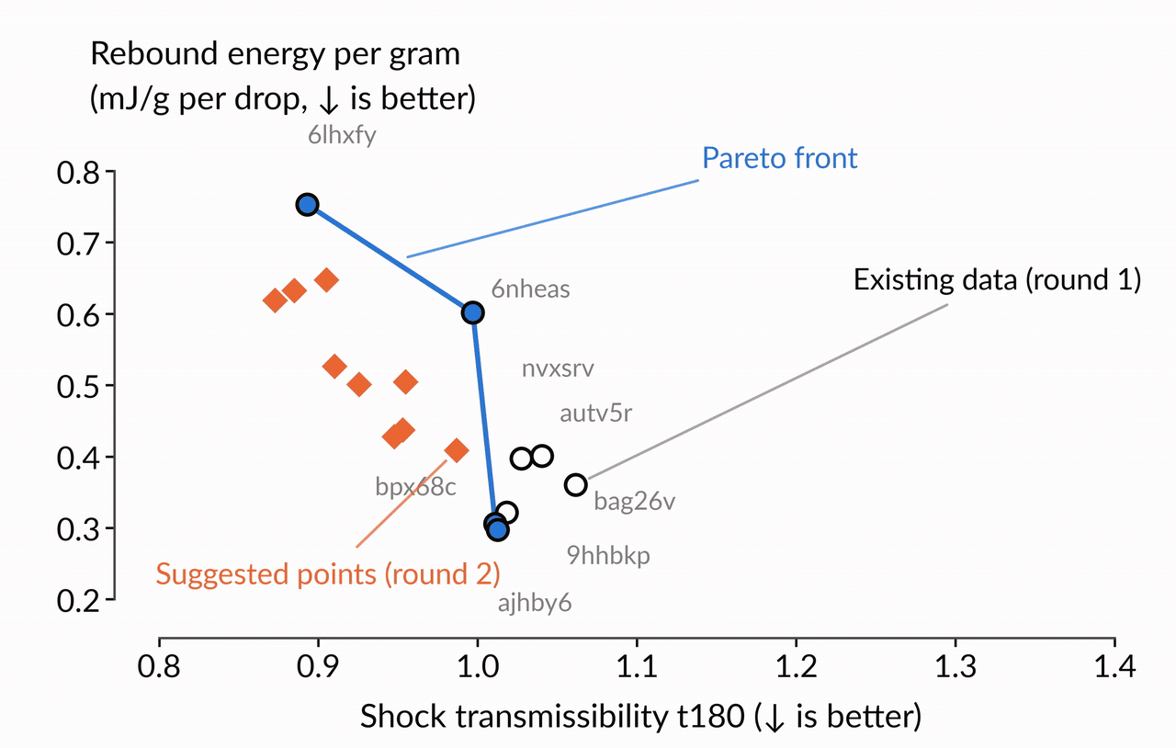
bo/figures/t3-prism-bo-round2-predicted-vs-actual-per-gram.gif
