vertical-cloud-lab/tensegrity-optimization/bo/figures/t3-prism-bo-round2-predicted-vs-actual.png

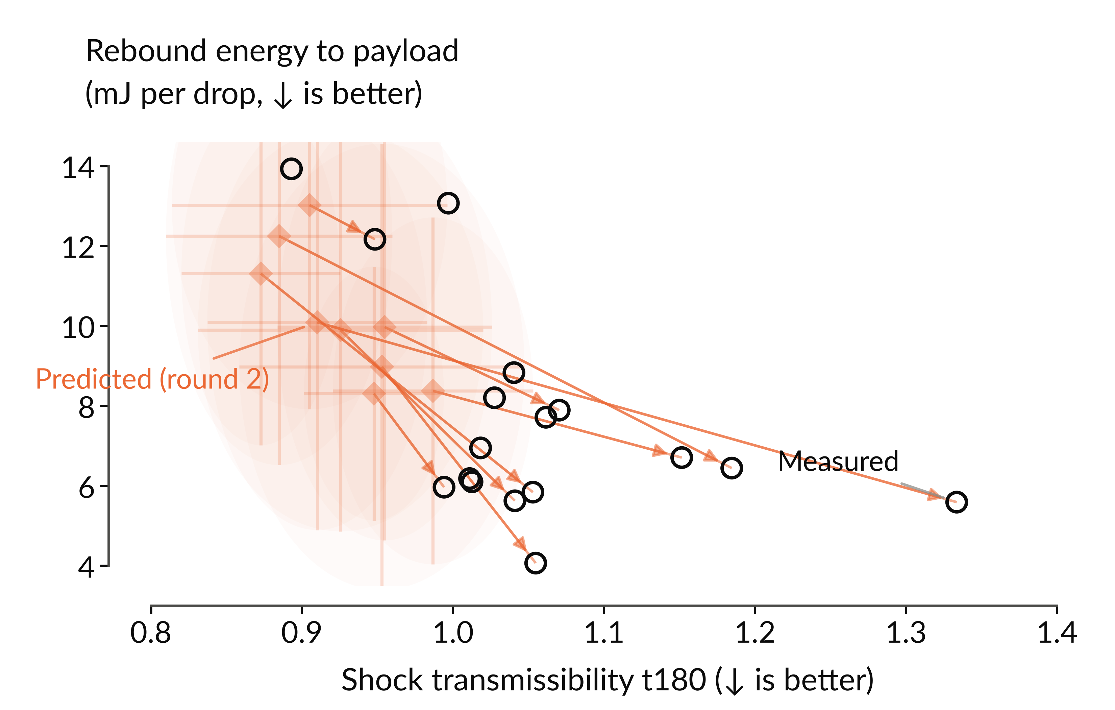
bo/figures/t3-prism-bo-round2-predicted-vs-actual.png
