vertical-cloud-lab/tensegrity-optimization/bo/figures/t3-prism-bo-round2-uncertainty-per-gram.png

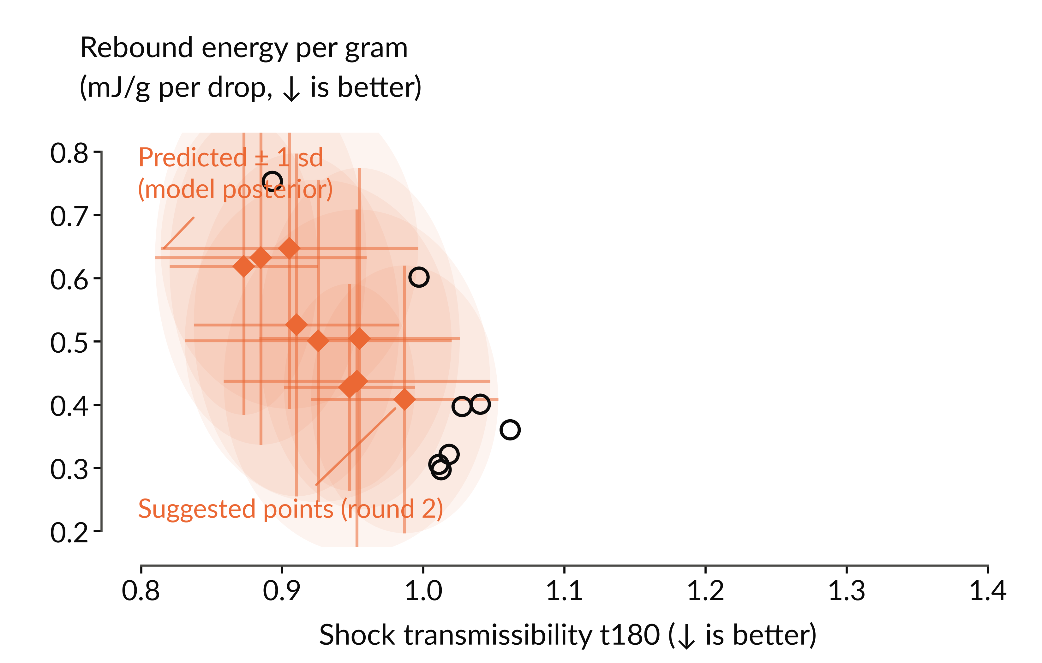
bo/figures/t3-prism-bo-round2-uncertainty-per-gram.png
