vertical-cloud-lab/tensegrity-optimization/bo/figures/t3-prism-bo-round2-uncertainty-PROTOTYPE.png

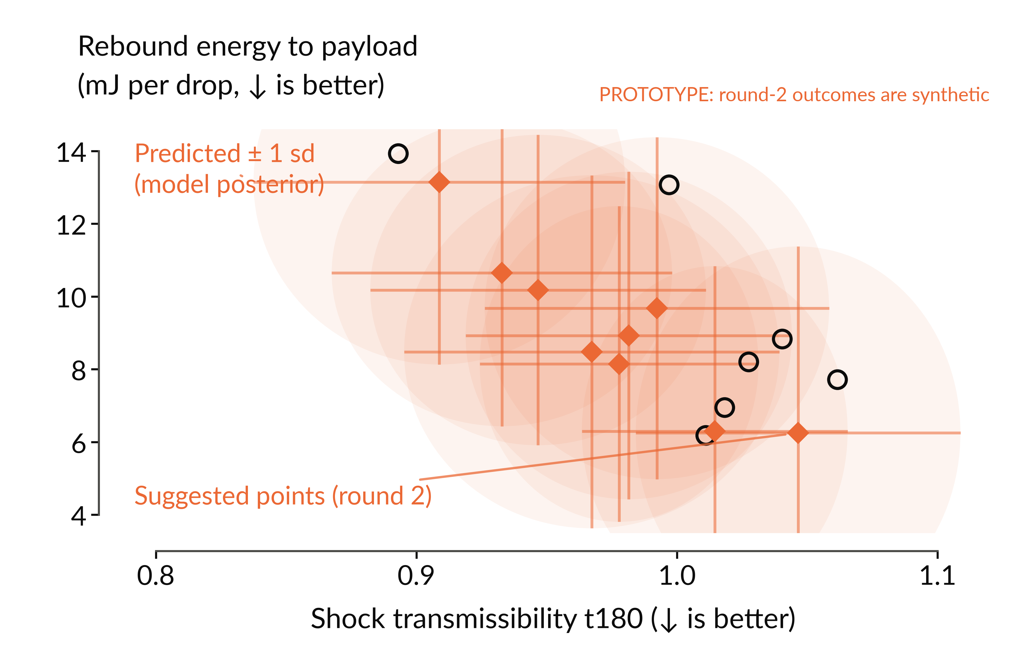
bo/figures/t3-prism-bo-round2-uncertainty-PROTOTYPE.png
