vertical-cloud-lab/tensegrity-optimization/bo/figures/t3-prism-bo-round3-front-final.png

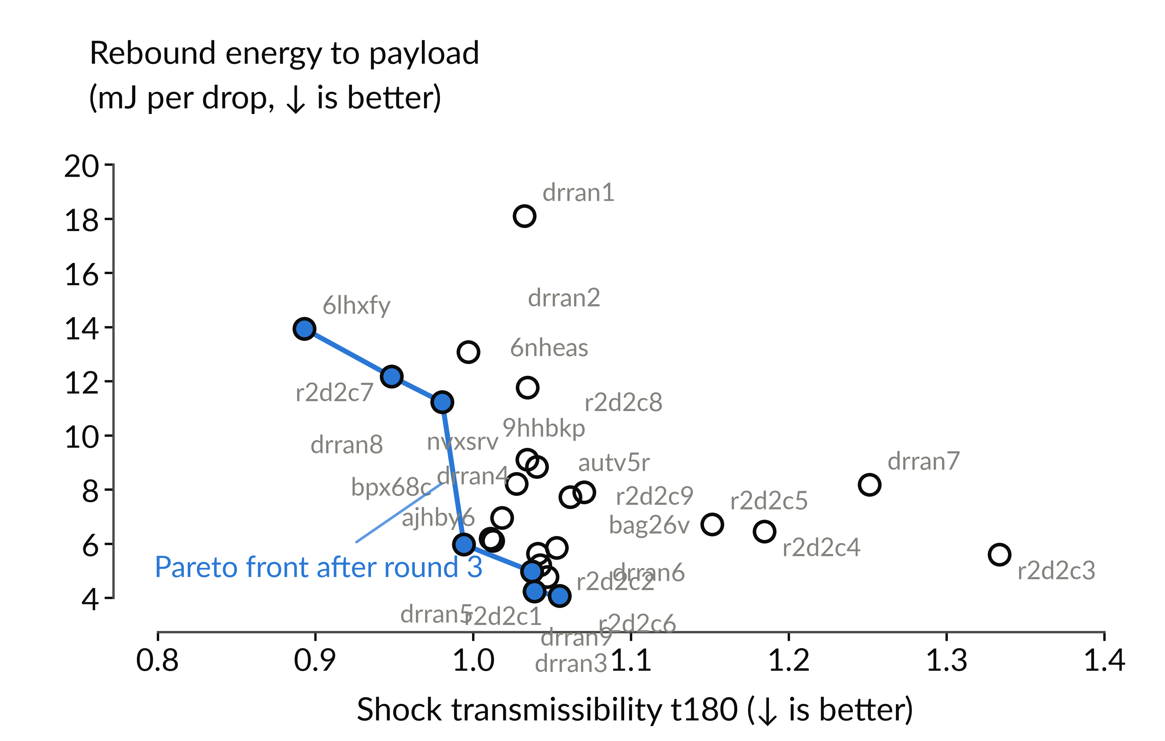
bo/figures/t3-prism-bo-round3-front-final.png
