vertical-cloud-lab/tensegrity-optimization/bo/figures/t3-prism-bo-round3-process-space.png

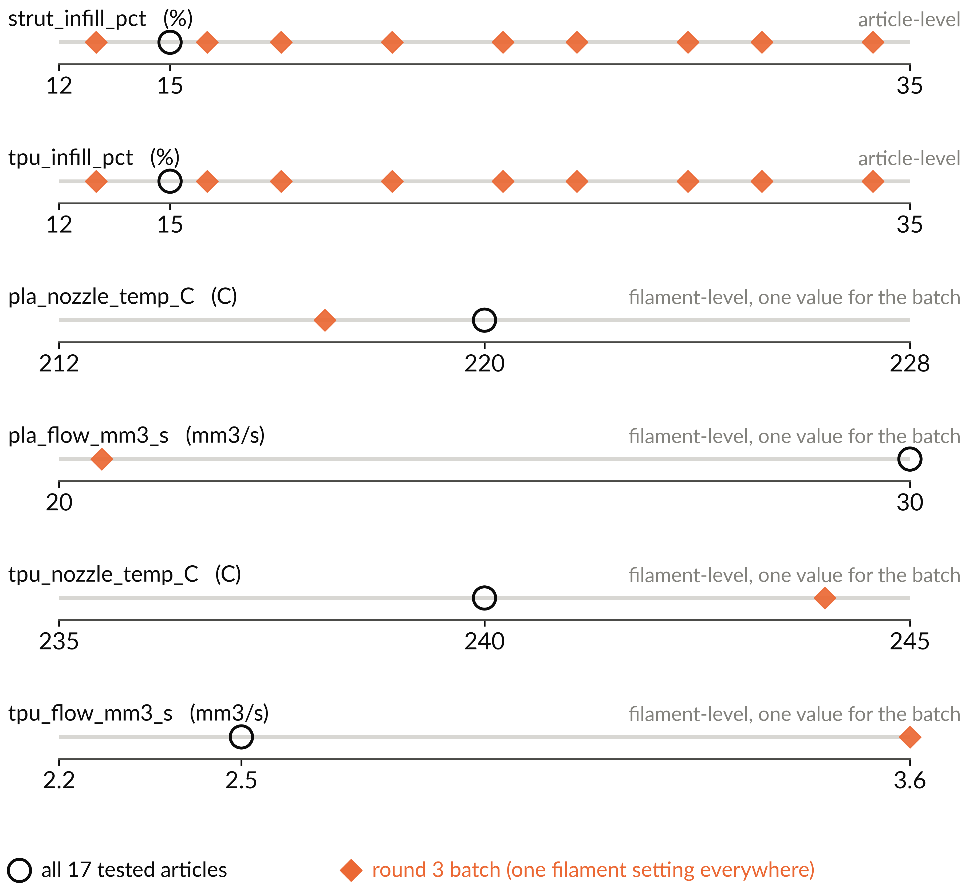
bo/figures/t3-prism-bo-round3-process-space.png
