vertical-cloud-lab/tensegrity-optimization/bo/figures/t3-prism-bo-round3-uncertainty-per-gram.png

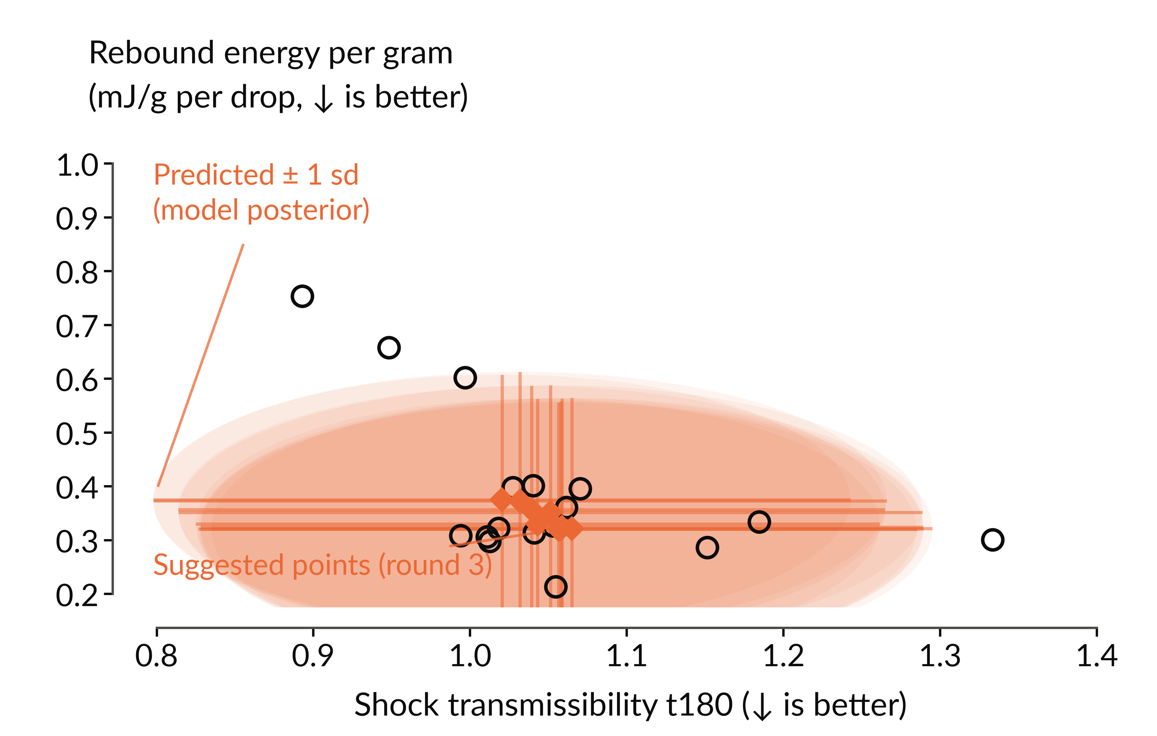
bo/figures/t3-prism-bo-round3-uncertainty-per-gram.png
