vertical-cloud-lab/tensegrity-optimization/bo/figures/t3-prism-bo-round4-front-final-per-gram.png

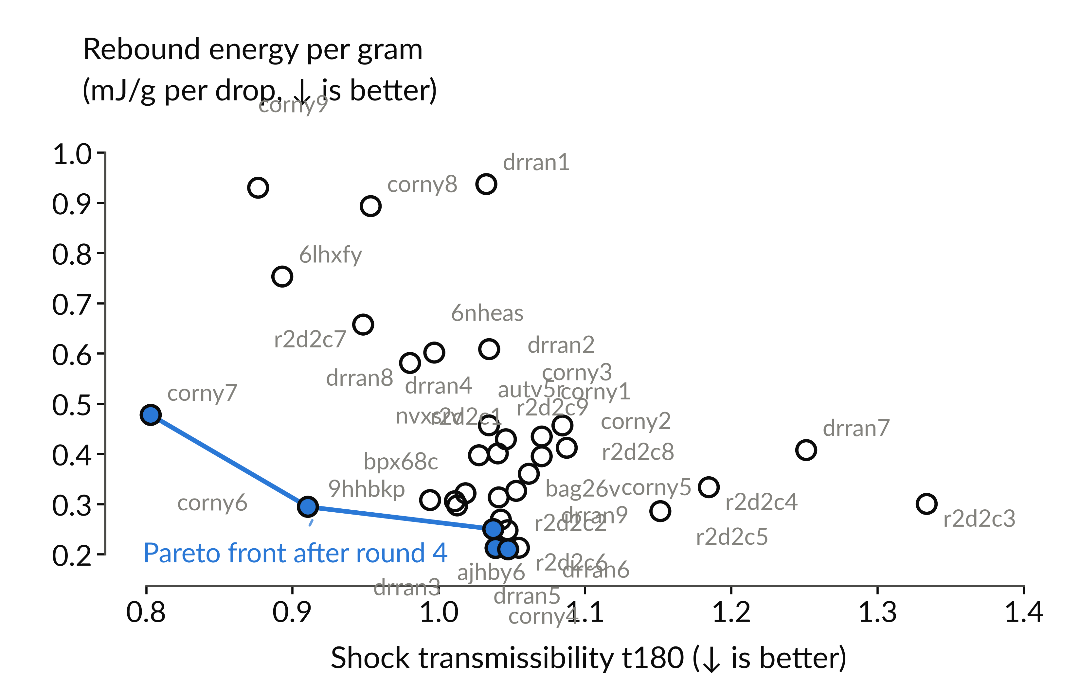
bo/figures/t3-prism-bo-round4-front-final-per-gram.png
