vertical-cloud-lab/tensegrity-optimization/bo/figures/t3-prism-bo-round4-front-final.png

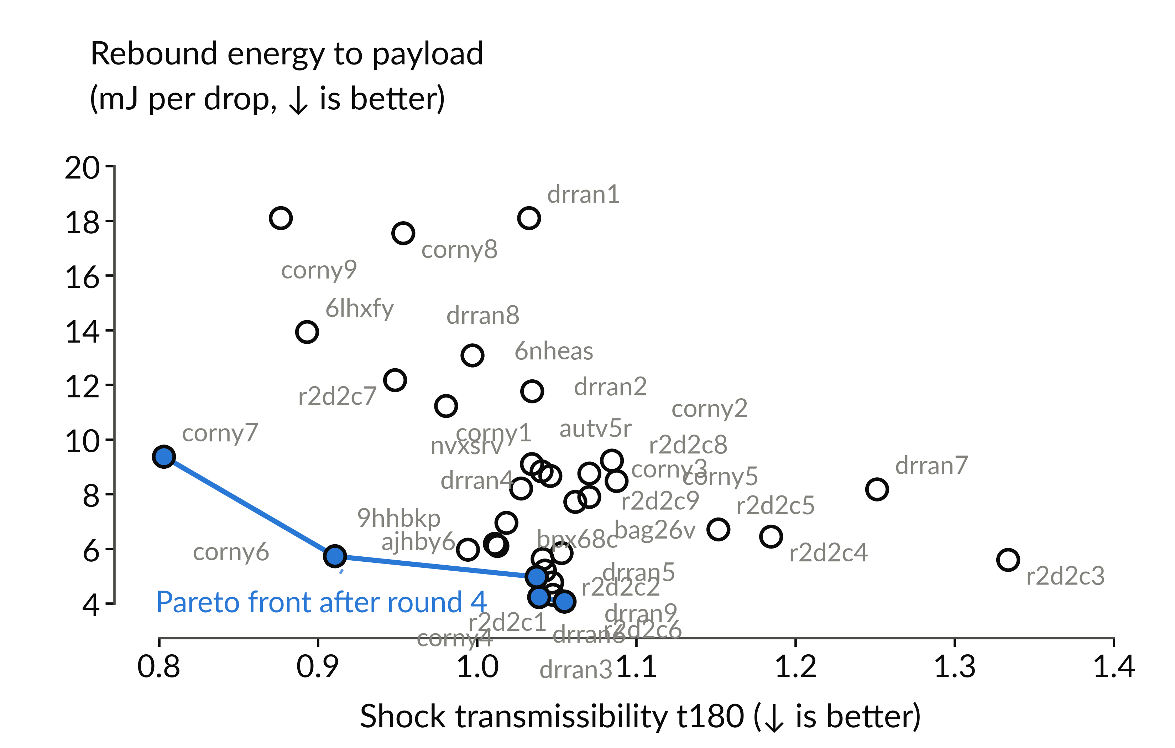
bo/figures/t3-prism-bo-round4-front-final.png
