vertical-cloud-lab/tensegrity-optimization/bo/figures/t3-prism-bo-round4-loocv.png

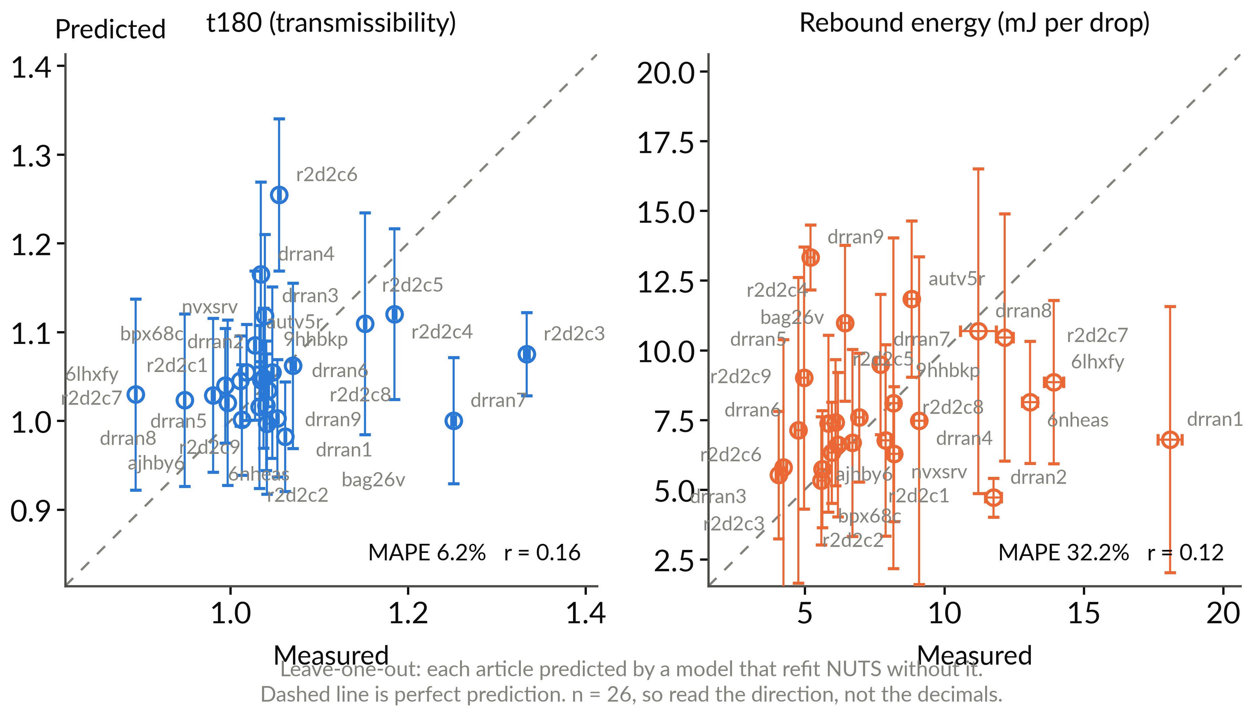
bo/figures/t3-prism-bo-round4-loocv.png
