vertical-cloud-lab/tensegrity-optimization/bo/figures/t3-prism-bo-round4-pareto.png

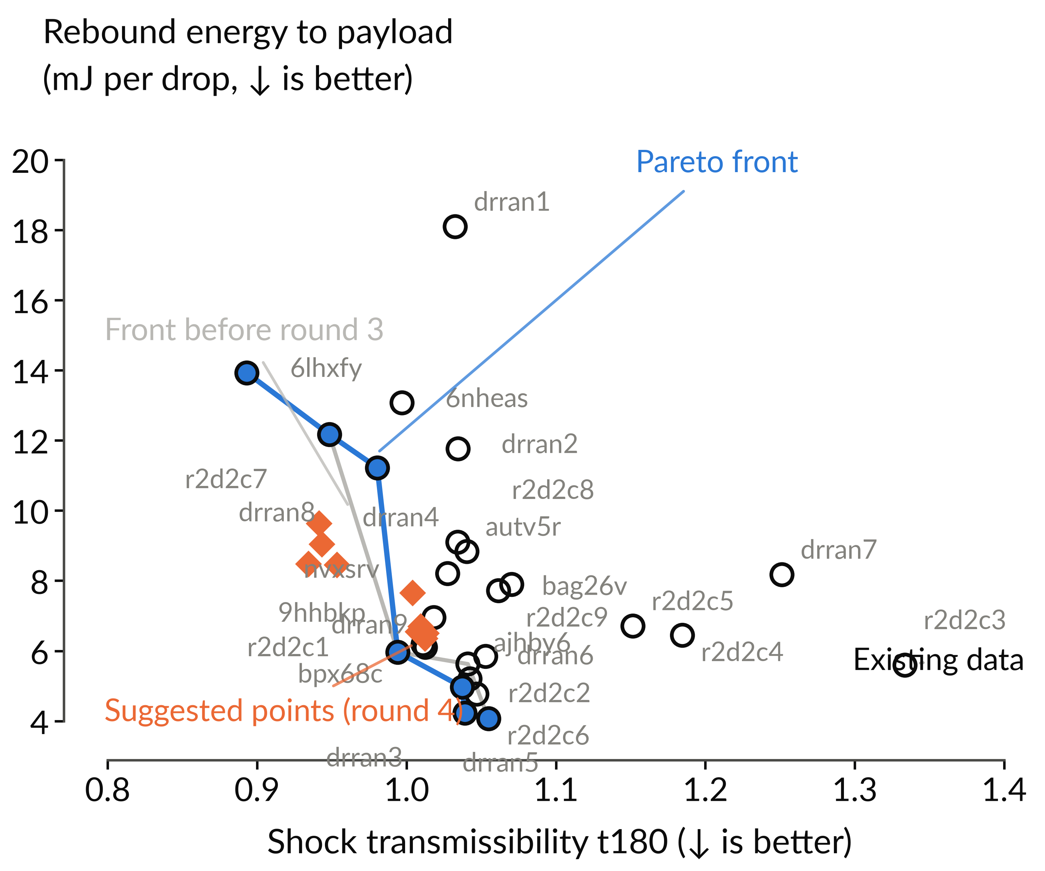
bo/figures/t3-prism-bo-round4-pareto.png
