vertical-cloud-lab/tensegrity-optimization/bo/figures/t3-prism-bo-round4-process-space.png

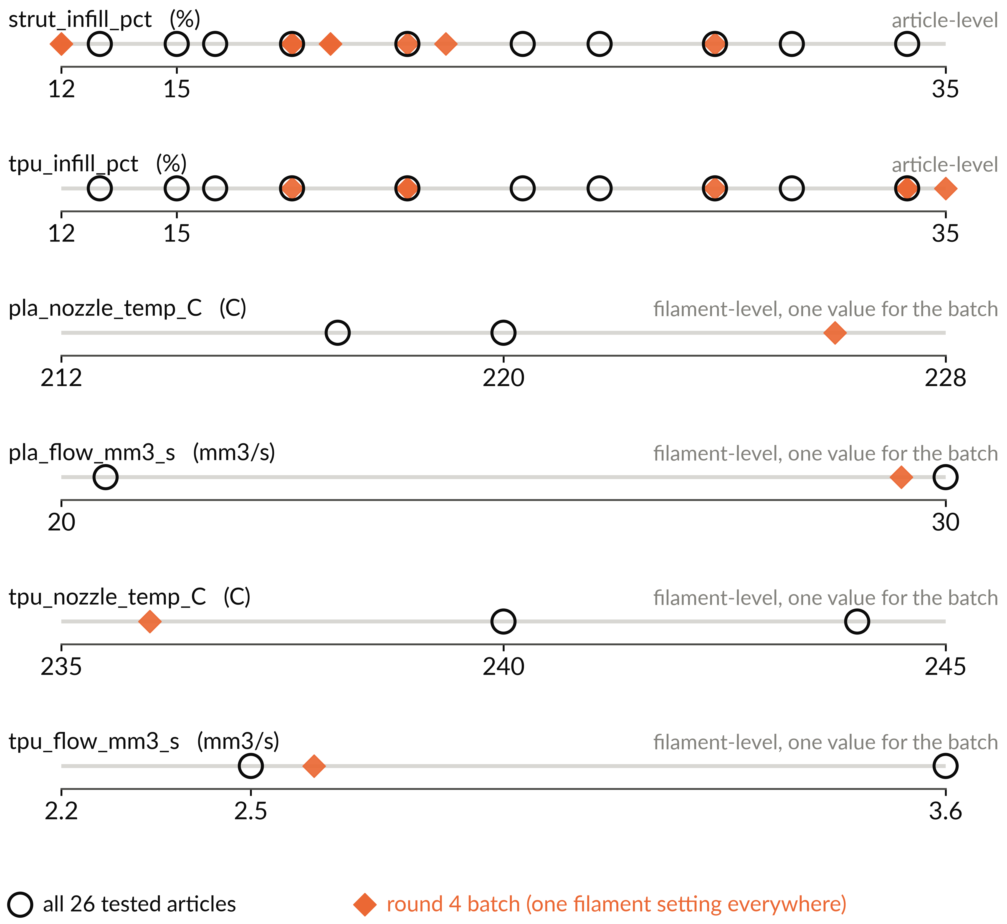
bo/figures/t3-prism-bo-round4-process-space.png
