vertical-cloud-lab/tensegrity-optimization/bo/figures/t3-prism-bo-round5-pareto.png

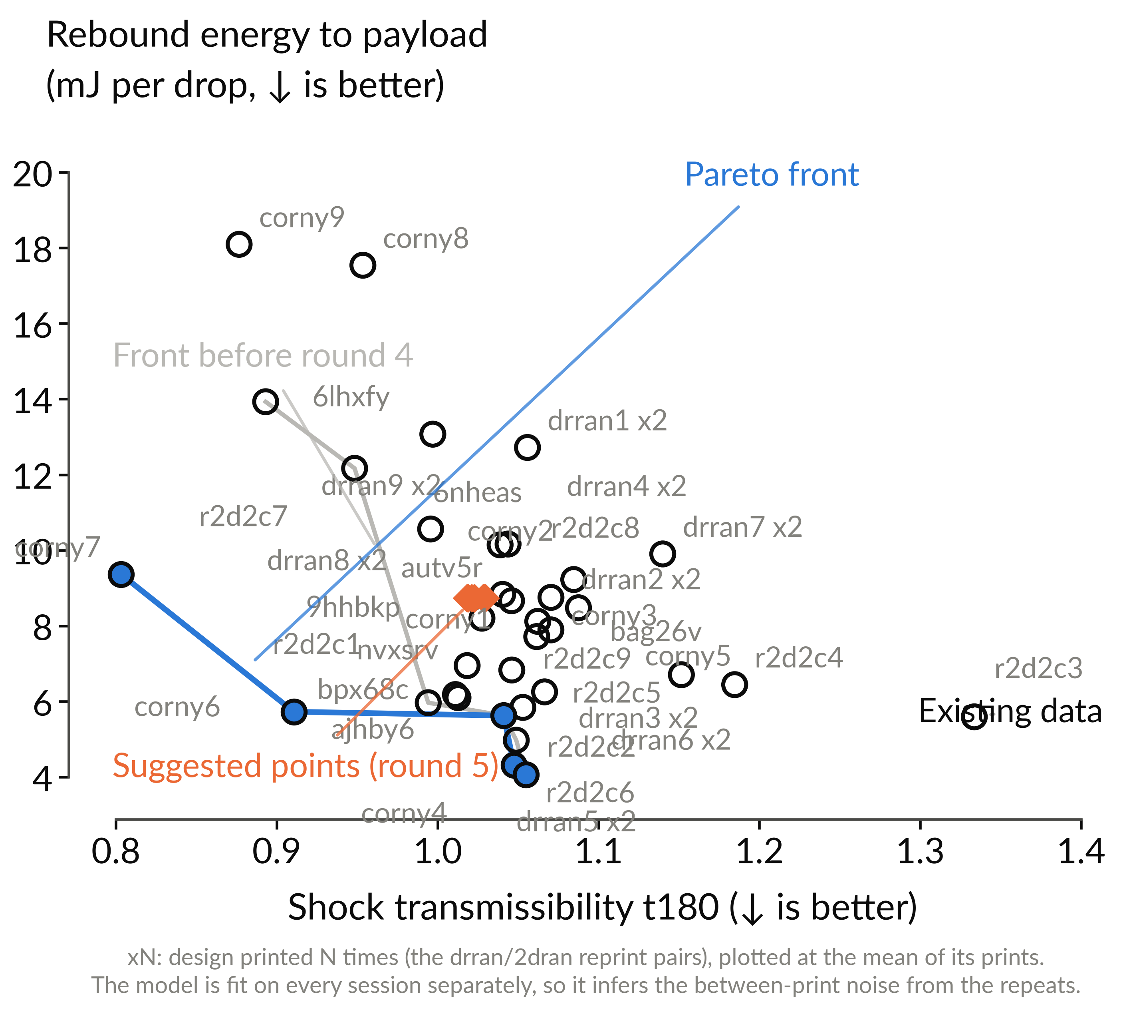
bo/figures/t3-prism-bo-round5-pareto.png
