vertical-cloud-lab/tensegrity-optimization/bo/figures/t3-prism-bo-round5-process-space.png

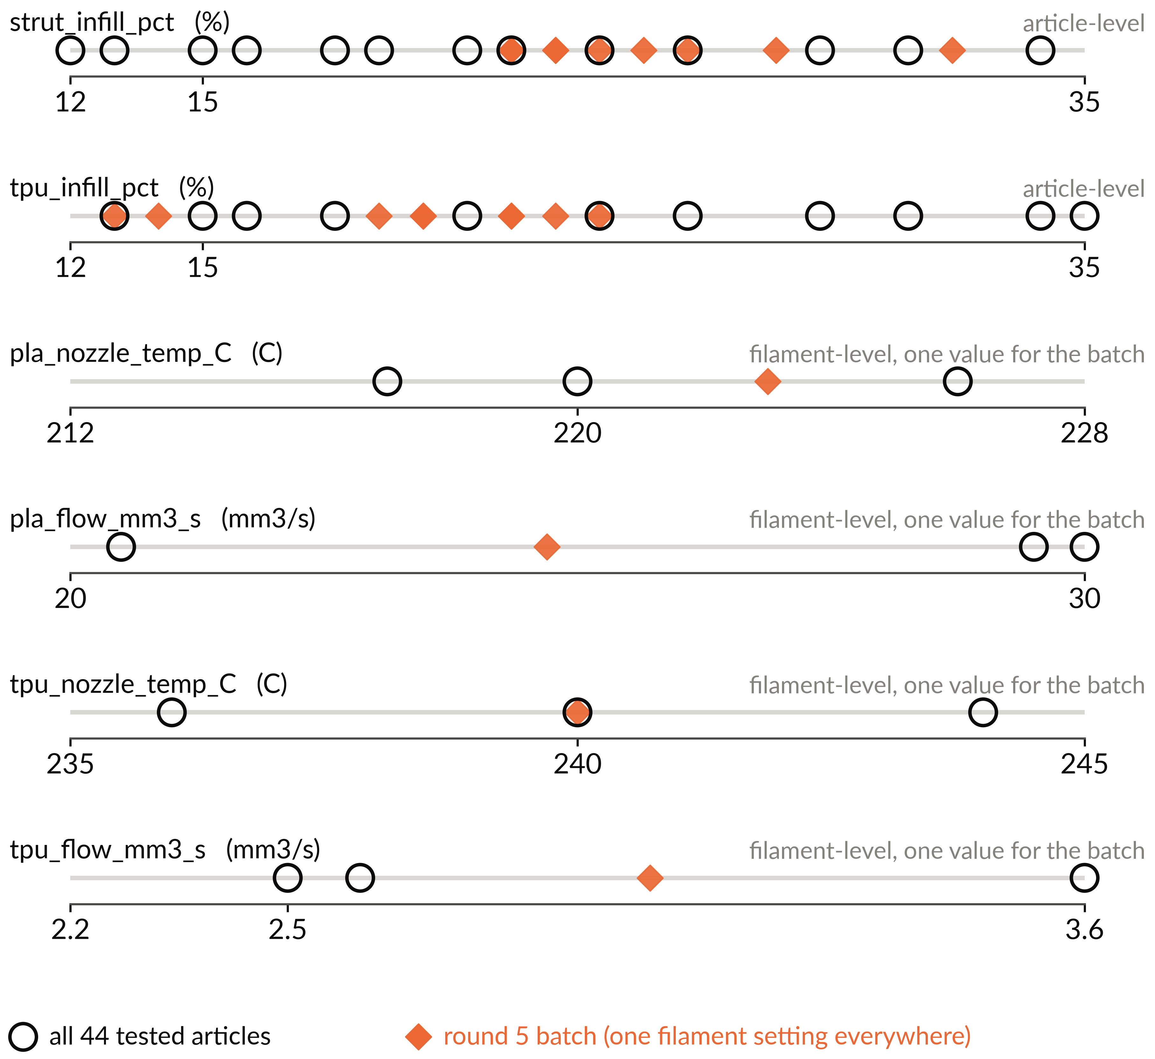
bo/figures/t3-prism-bo-round5-process-space.png
