vertical-cloud-lab/tensegrity-optimization/bo/figures/t3-prism-drop-count-sensitivity.png

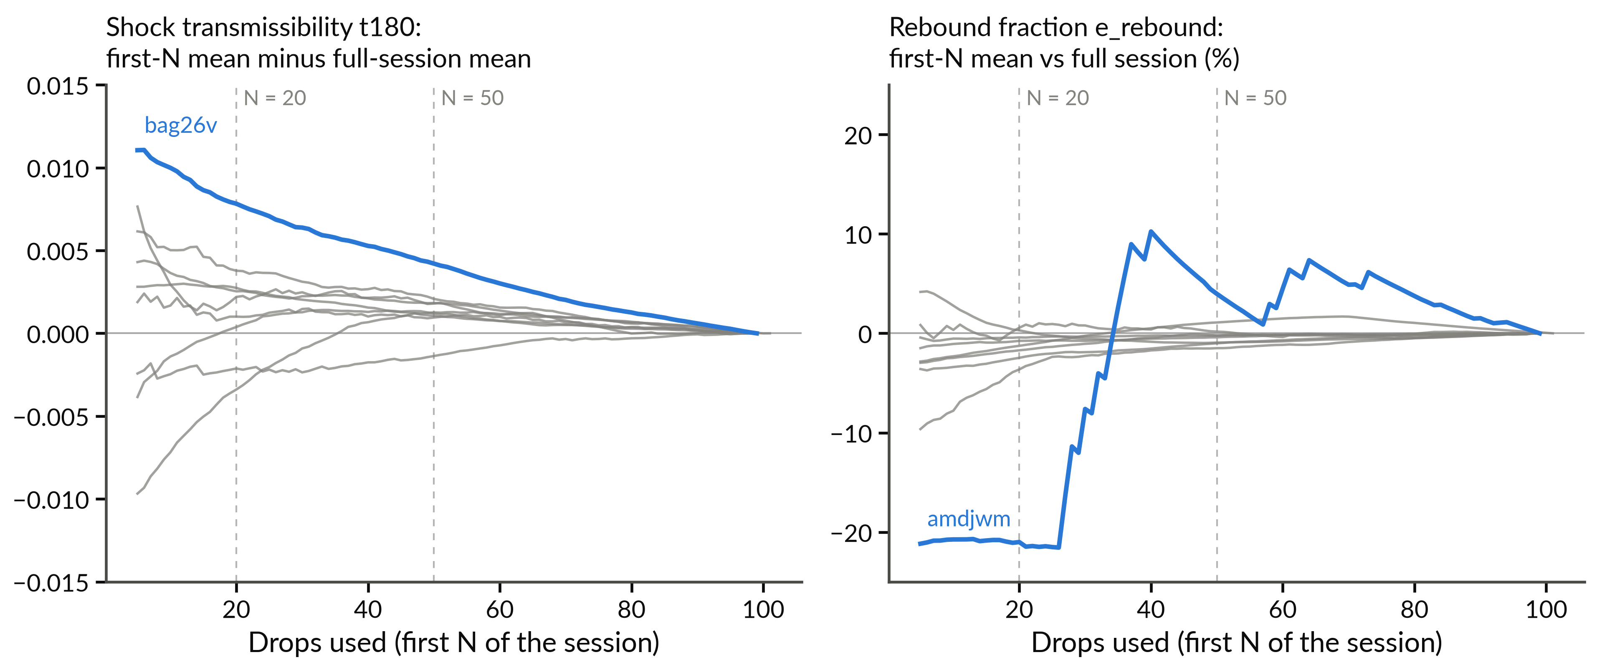
bo/figures/t3-prism-drop-count-sensitivity.png
