vertical-cloud-lab/tensegrity-optimization/bo/figures/t3-prism-drop-window-extrapolation.png

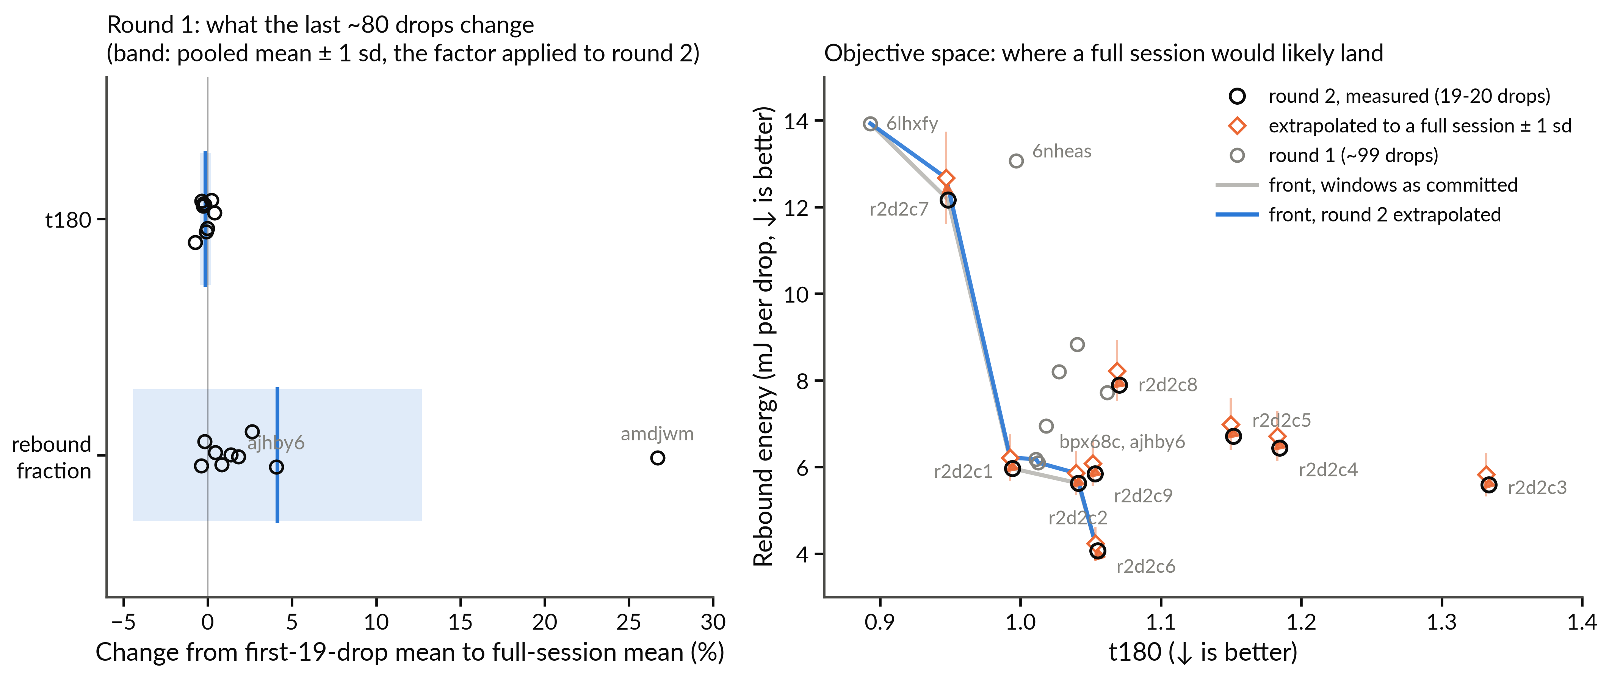
bo/figures/t3-prism-drop-window-extrapolation.png
