vertical-cloud-lab/tensegrity-optimization/bo/figures/t3-prism-replicate-study-power.png

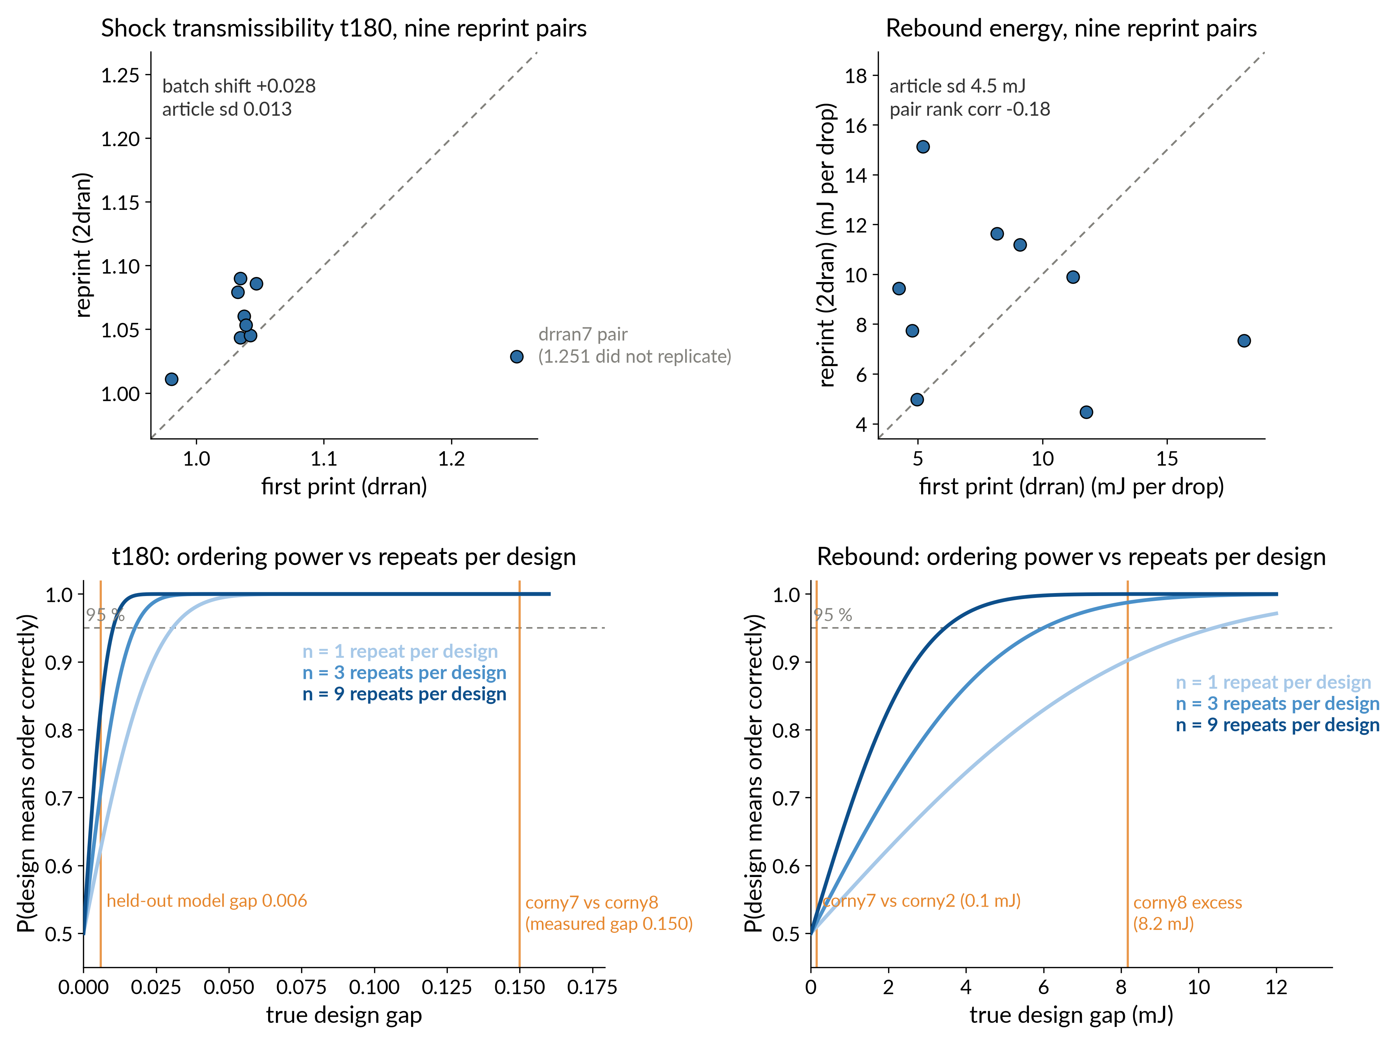
bo/figures/t3-prism-replicate-study-power.png
