vertical-cloud-lab/tensegrity-optimization/bo/figures/t3-prism-round-qc-comparison.png

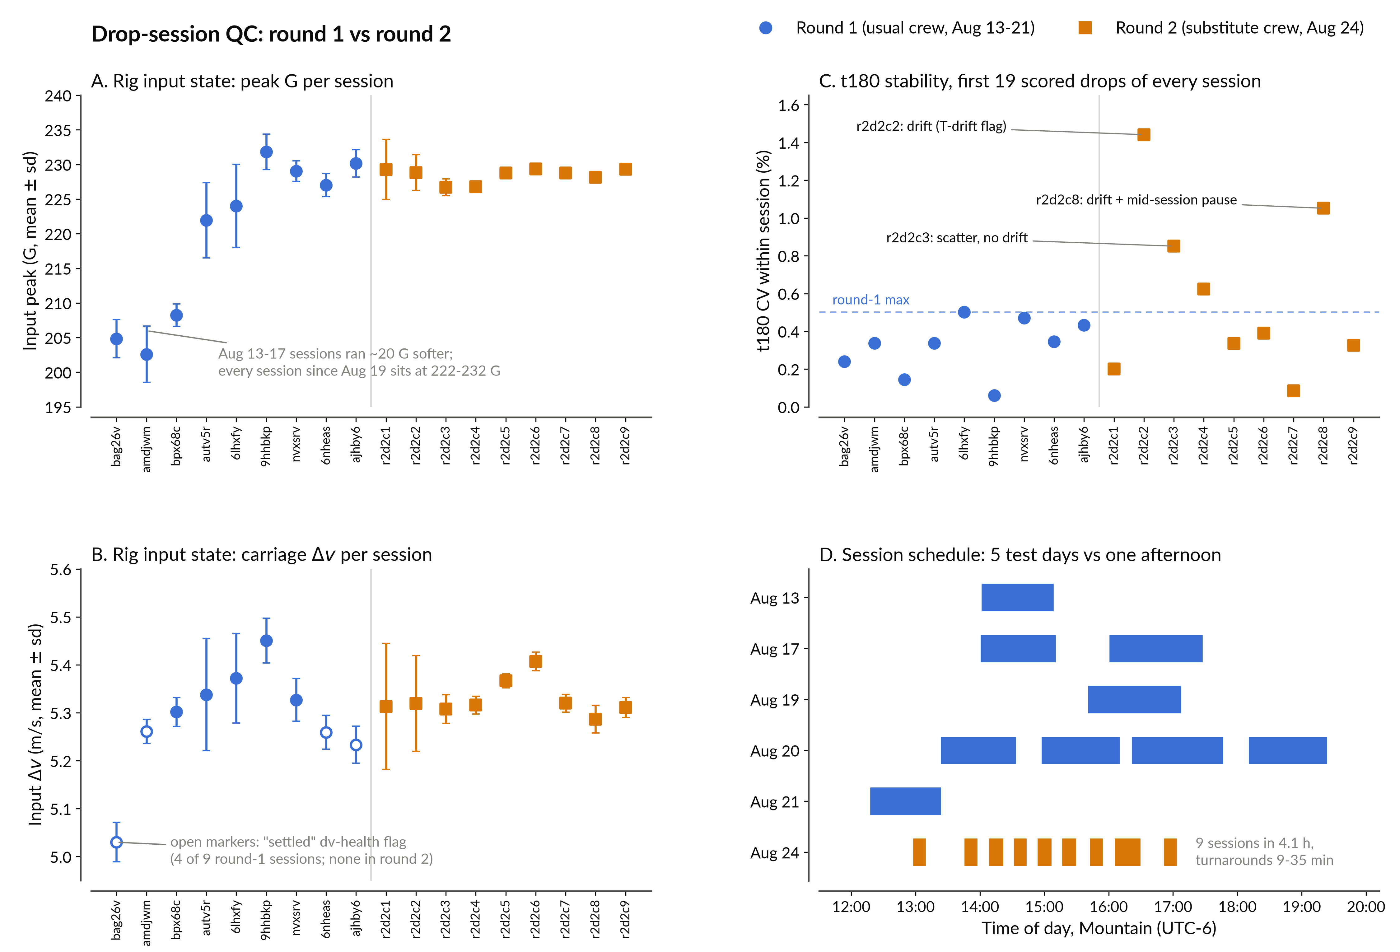
bo/figures/t3-prism-round-qc-comparison.png
