vertical-cloud-lab/tensegrity-optimization/bo/t3-prism-bo-round3-iso.png

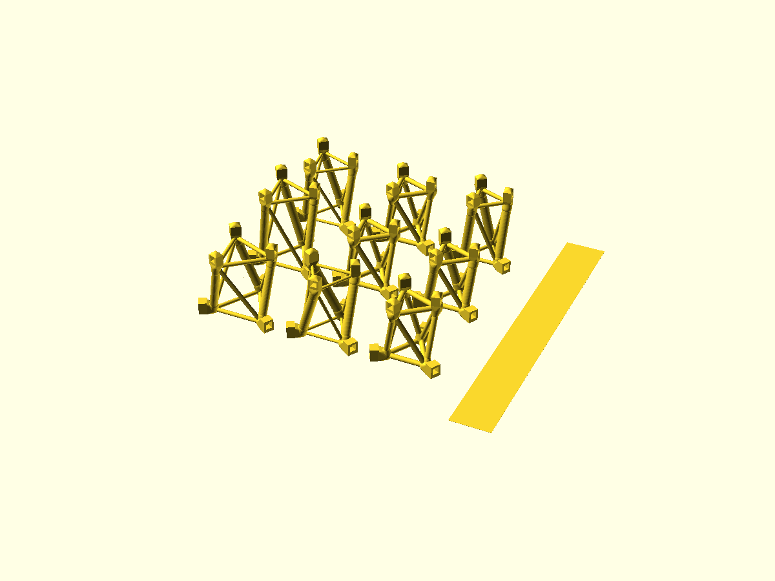
bo/t3-prism-bo-round3-iso.png
