vertical-cloud-lab/tensegrity-optimization/bo/t3-prism-bo-round3-plate.png

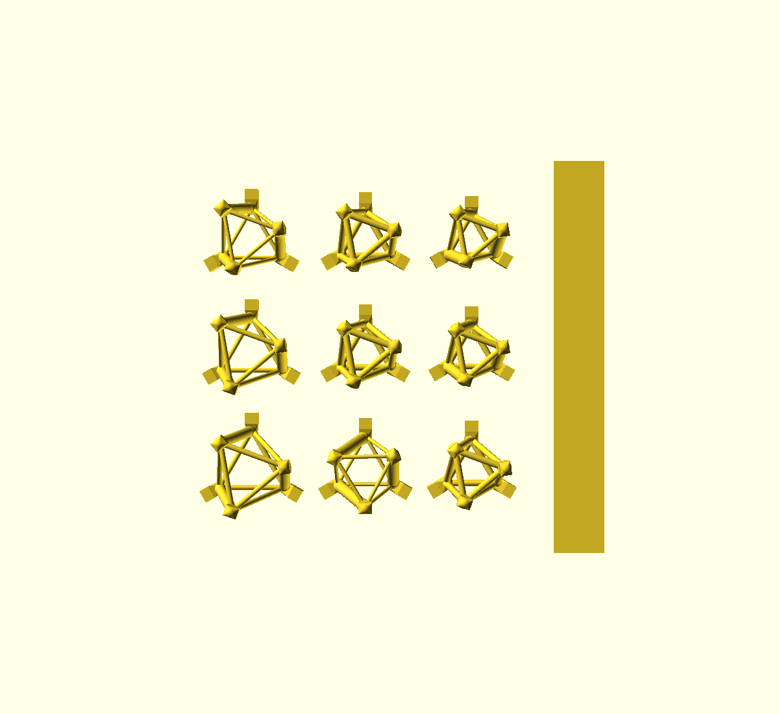
bo/t3-prism-bo-round3-plate.png
