vertical-cloud-lab/tensegrity-optimization/bo/t3-prism-bo-round4-plate.png

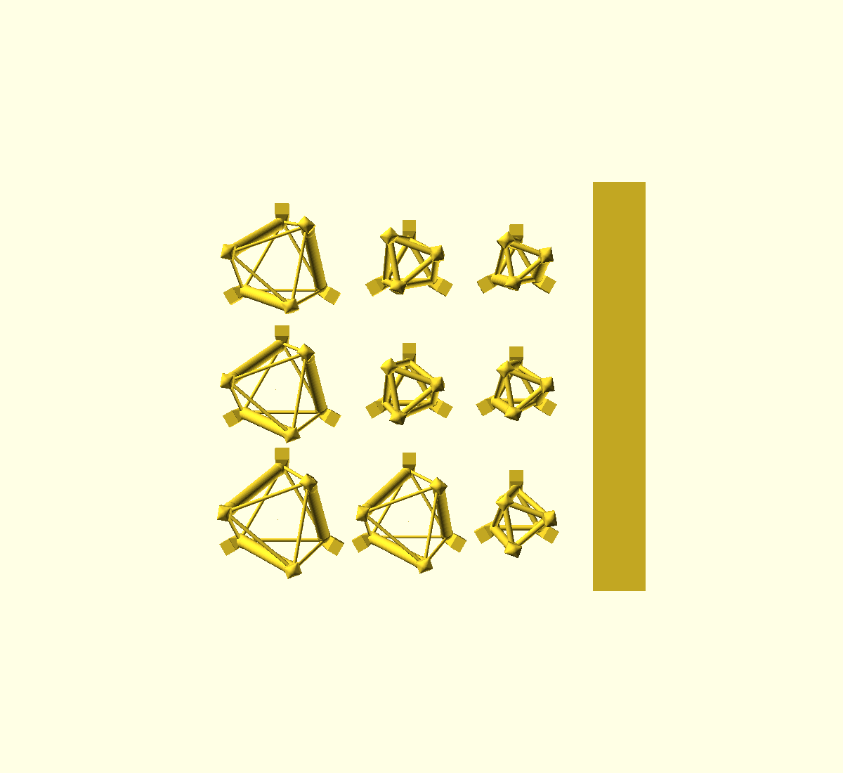
bo/t3-prism-bo-round4-plate.png
