vertical-cloud-lab/tensegrity-optimization/bo/t3-prism-bo-round5-iso.png

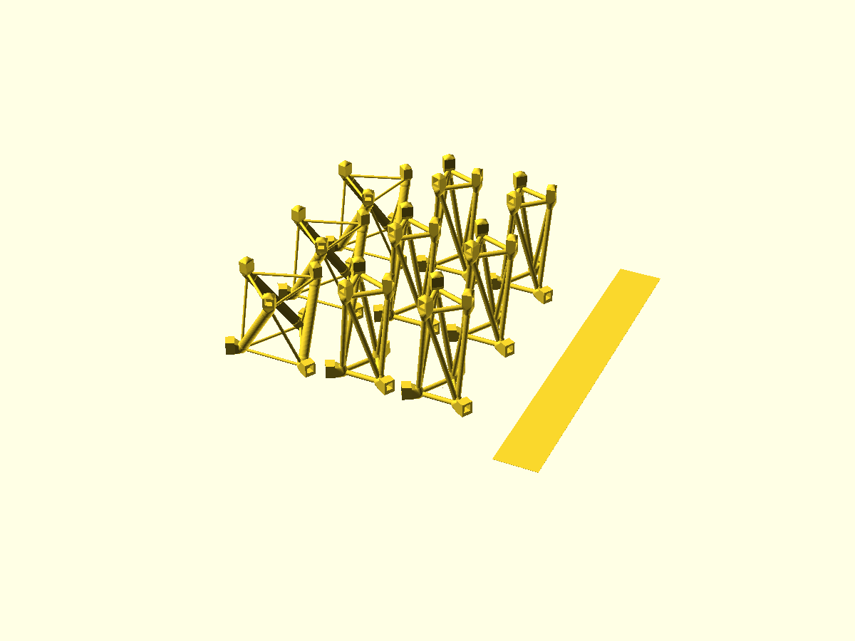
bo/t3-prism-bo-round5-iso.png
