vertical-cloud-lab/tensegrity-optimization/bo/replicate-study/stls/corny2-t38-struts.stl

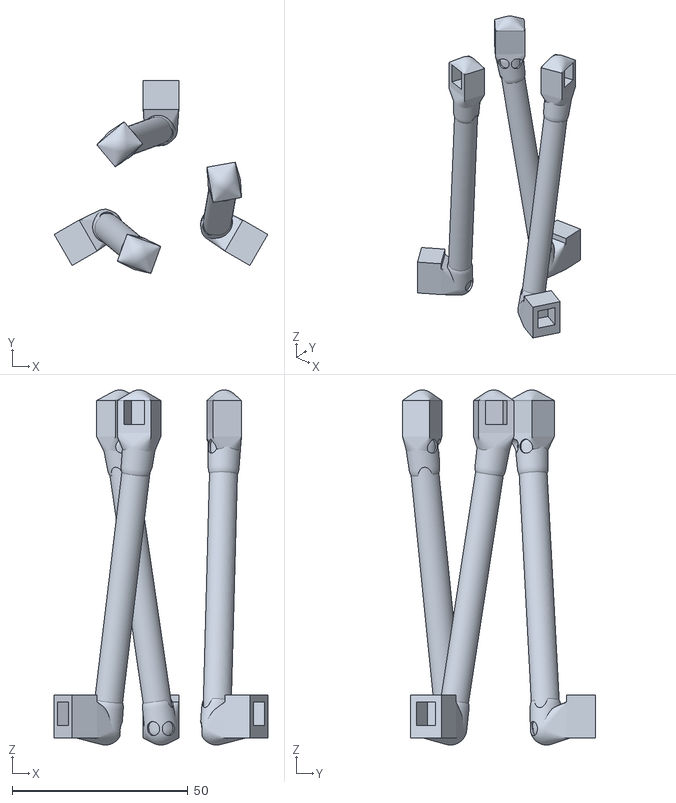
[picture p83: CAD file, 2026-09-08]
bo/replicate-study/stls/corny2-t38-struts.stl
60.8 x 54.9 x 101.0
