vertical-cloud-lab/tensegrity-optimization/bo/replicate-study/stls/dran3/dran36-t34-struts.stl

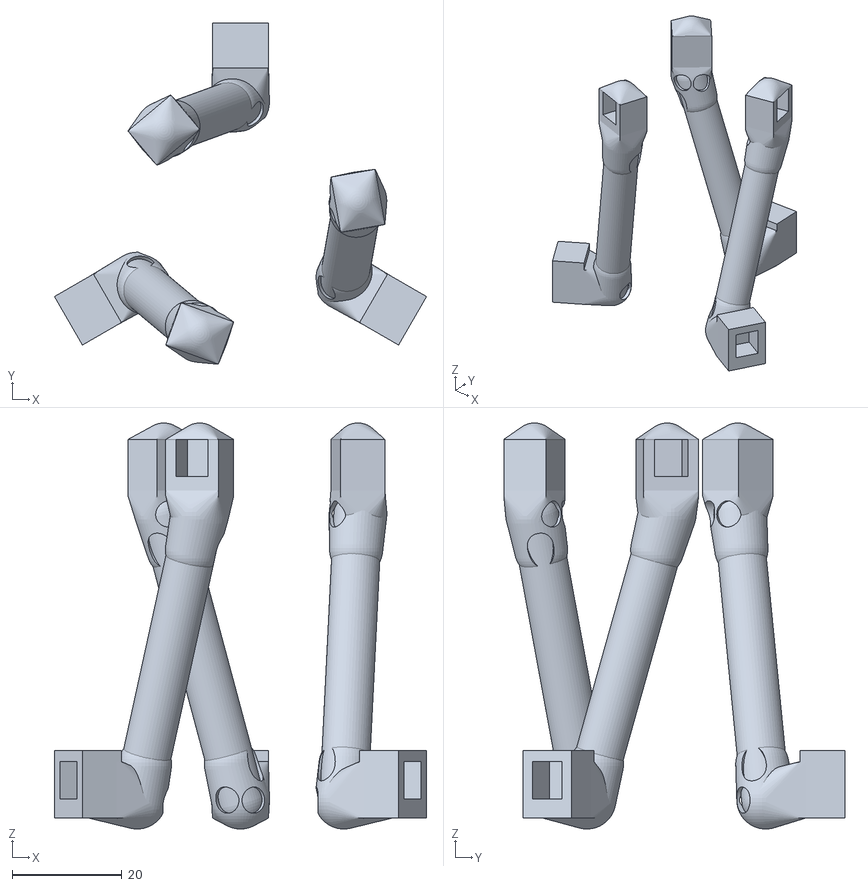
[picture p84: CAD file, 2026-08-31]
bo/replicate-study/stls/dran3/dran36-t34-struts.stl
67.8 x 62.2 x 74.0
