vertical-cloud-lab/tensegrity-optimization/bo/slices/t3-prism-bo-round1.H2D-MM-PLAstruts-TPUcables_manual-supports.3mf

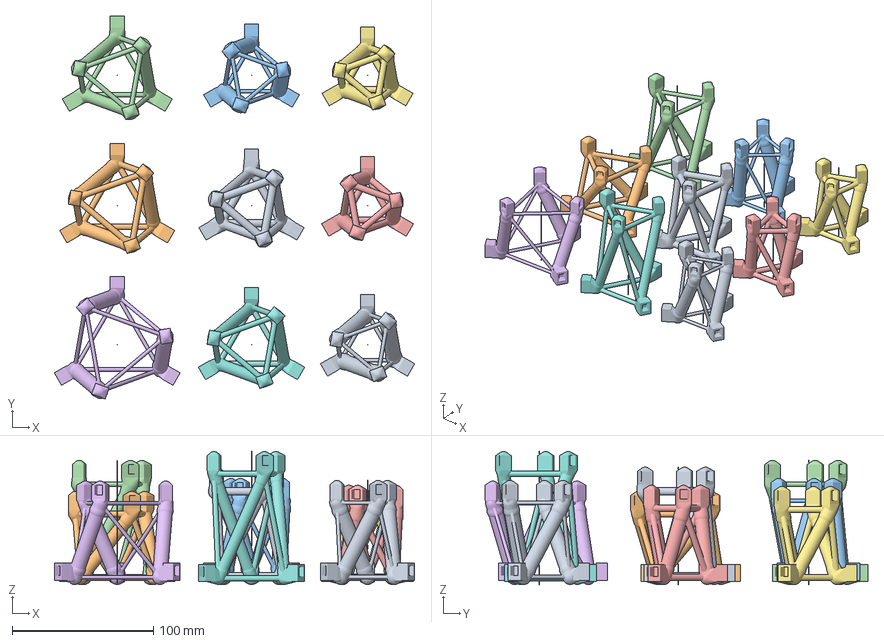
[picture p85: CAD file, 2026-08-26]
bo/slices/t3-prism-bo-round1.H2D-MM-PLAstruts-TPUcables_manual-supports.3mf
255.3 x 271.3 x 94.2 mm
Specimen 00
Specimen 01
Specimen 02
Specimen 03
Specimen 04
Specimen 05
Specimen 06
Specimen 07
Specimen 08
