vertical-cloud-lab/tensegrity-optimization/bo/replicate-study/stls/corny8-t39-cables.stl

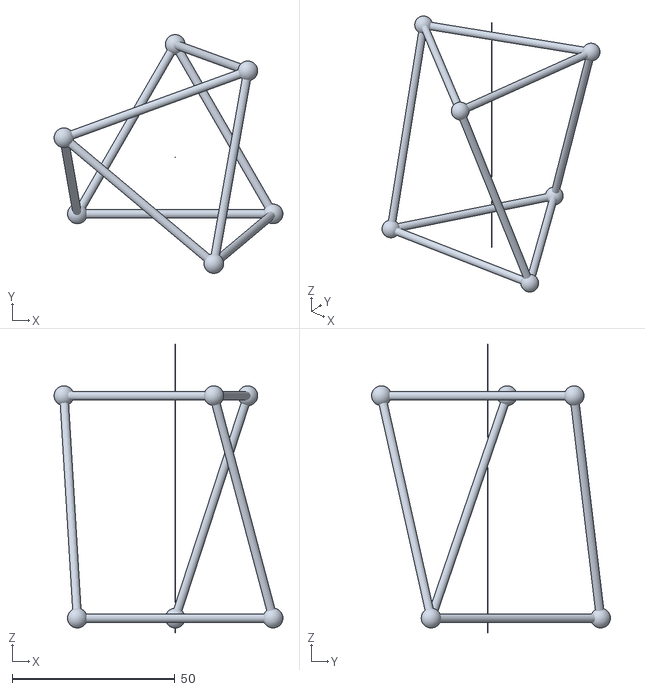
[picture p86: CAD file, 2026-09-08]
bo/replicate-study/stls/corny8-t39-cables.stl
70.3 x 73.4 x 88.4
