vertical-cloud-lab/tensegrity-optimization/bo/slices/t3-prism-bo-batch.H2D-MM-PLAstruts-TPUcables.as-printed.3mf

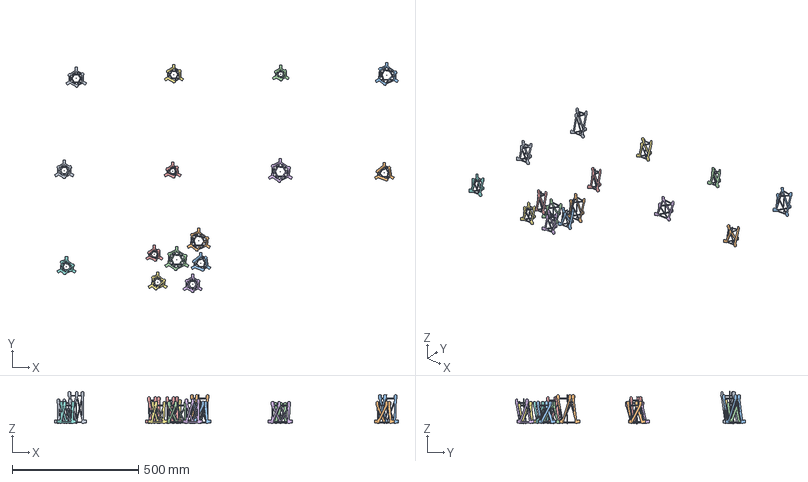
[picture p87: CAD file, 2026-08-21]
bo/slices/t3-prism-bo-batch.H2D-MM-PLAstruts-TPUcables.as-printed.3mf
1360.5 x 910.5 x 126.8 mm
Specimen 00 x 2
Specimen 01 x 2
Specimen 02 x 2
Specimen 03
Specimen 04 x 2
Specimen 05 x 2
Specimen 06
Specimen 07 x 2
Specimen 08
