vertical-cloud-lab/tensegrity-optimization/bo/per-specimen-stls/t3-prism-bo-round5-t62-struts.stl

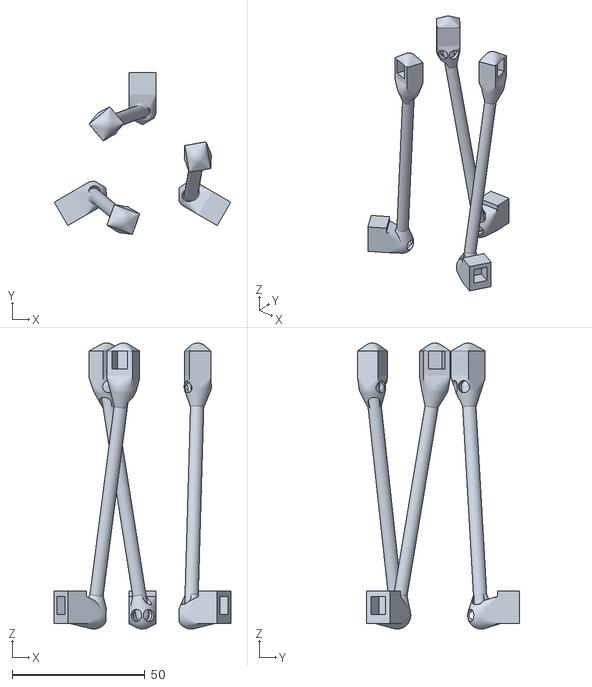
[picture p88: CAD file, 2026-09-16]
bo/per-specimen-stls/t3-prism-bo-round5-t62-struts.stl
66.6 x 61.0 x 107.9
