vertical-cloud-lab/tensegrity-optimization/bo/replicate-study/stls/corny7-t37-struts.stl

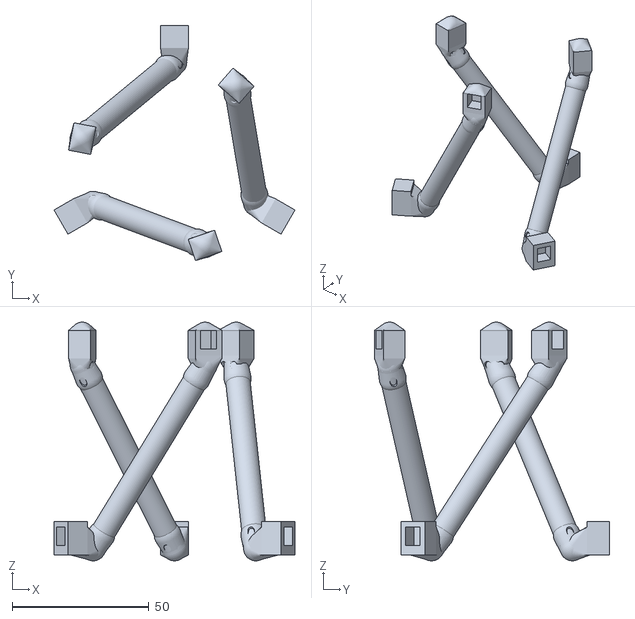
[picture p89: CAD file, 2026-09-08]
bo/replicate-study/stls/corny7-t37-struts.stl
88.1 x 85.9 x 87.3
