vertical-cloud-lab/tensegrity-optimization/bo/per-specimen-stls/t3-prism-bo-round5-t57-cables.stl

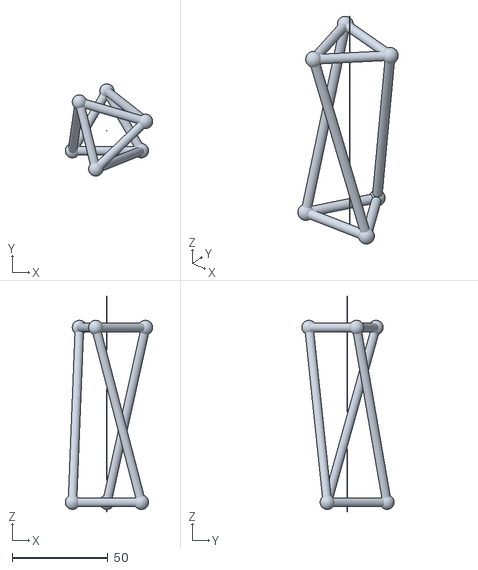
[picture p90: CAD file, 2026-09-16]
bo/per-specimen-stls/t3-prism-bo-round5-t57-cables.stl
45.6 x 48.1 x 112.5
