vertical-cloud-lab/tensegrity-optimization/bo/replicate-study/stls/dran3/dran37-t32-cables.stl

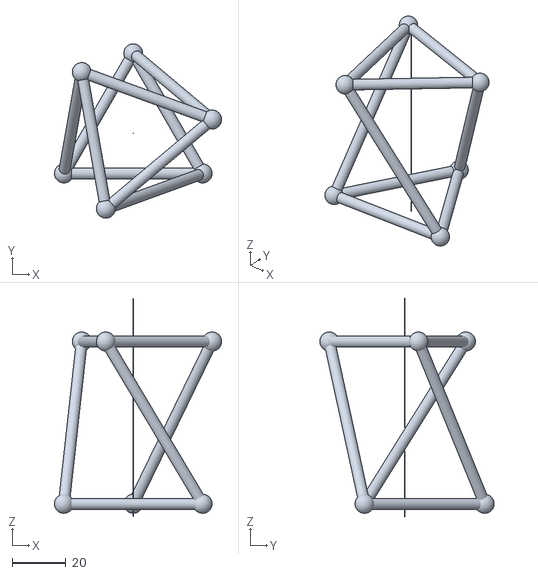
[picture p91: CAD file, 2026-08-31]
bo/replicate-study/stls/dran3/dran37-t32-cables.stl
62.4 x 65.1 x 81.4
