vertical-cloud-lab/tensegrity-optimization/bo/per-specimen-stls/t3-prism-bo-round5-t62-cables.stl

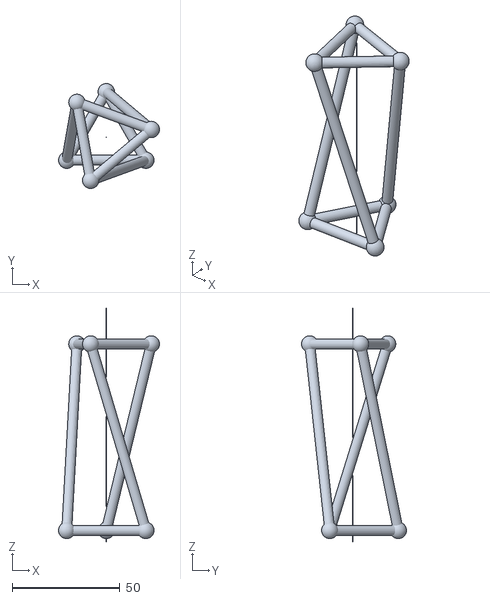
[picture p92: CAD file, 2026-09-16]
bo/per-specimen-stls/t3-prism-bo-round5-t62-cables.stl
46.8 x 48.6 x 107.9
