vertical-cloud-lab/tensegrity-optimization/bo/replicate-study/stls/dran3/dran39-t30-struts.stl

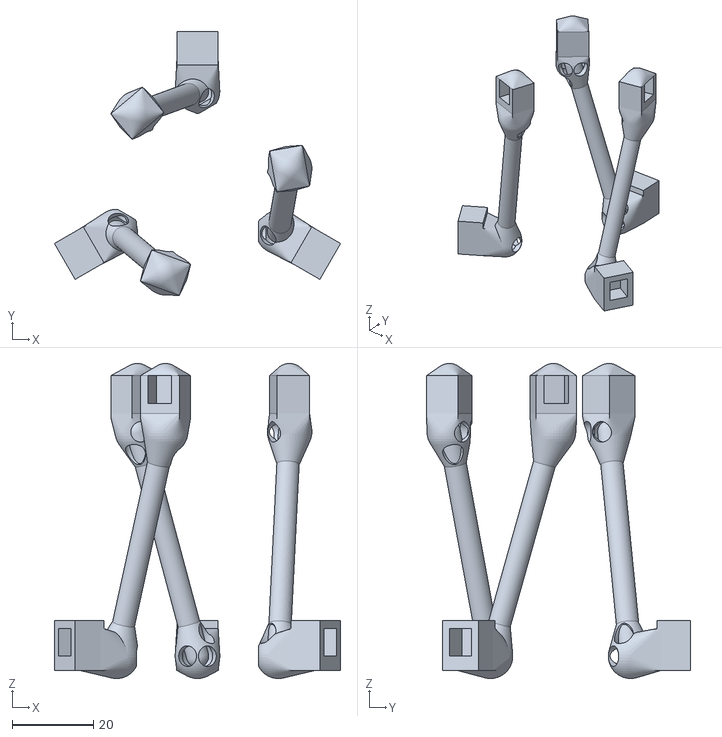
[picture p93: CAD file, 2026-08-31]
bo/replicate-study/stls/dran3/dran39-t30-struts.stl
70.4 x 64.9 x 77.5
