vertical-cloud-lab/tensegrity-optimization/bo/replicate-study/stls/dran3/dran36-t34-cables.stl

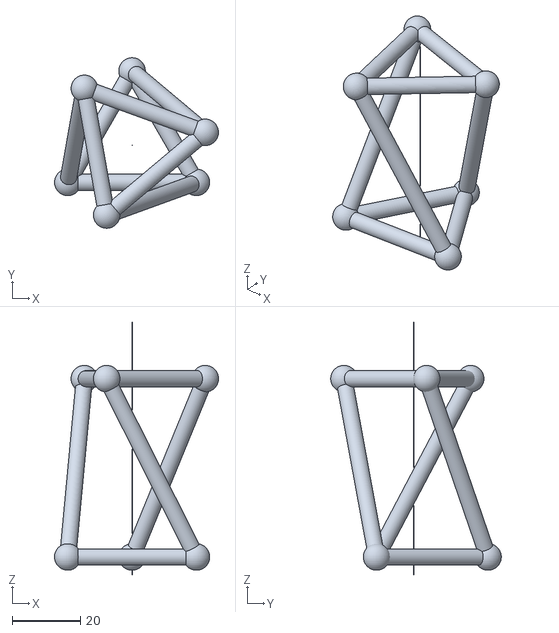
[picture p94: CAD file, 2026-08-31]
bo/replicate-study/stls/dran3/dran36-t34-cables.stl
48.0 x 49.9 x 74.0
