vertical-cloud-lab/tensegrity-optimization/bo/per-specimen-stls/t3-prism-bo-round5-t59-cables.stl

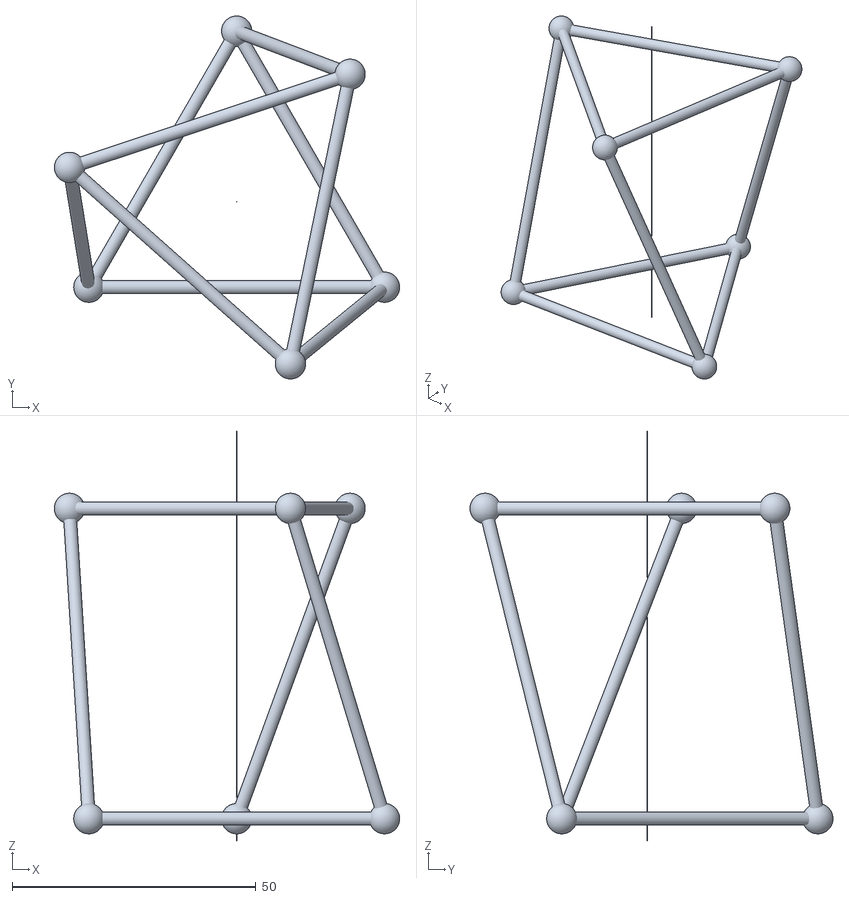
[picture p95: CAD file, 2026-09-16]
bo/per-specimen-stls/t3-prism-bo-round5-t59-cables.stl
70.9 x 74.5 x 84.1
