vertical-cloud-lab/tensegrity-optimization/bo/replicate-study/stls/dran3/dran38-t35-cables.stl

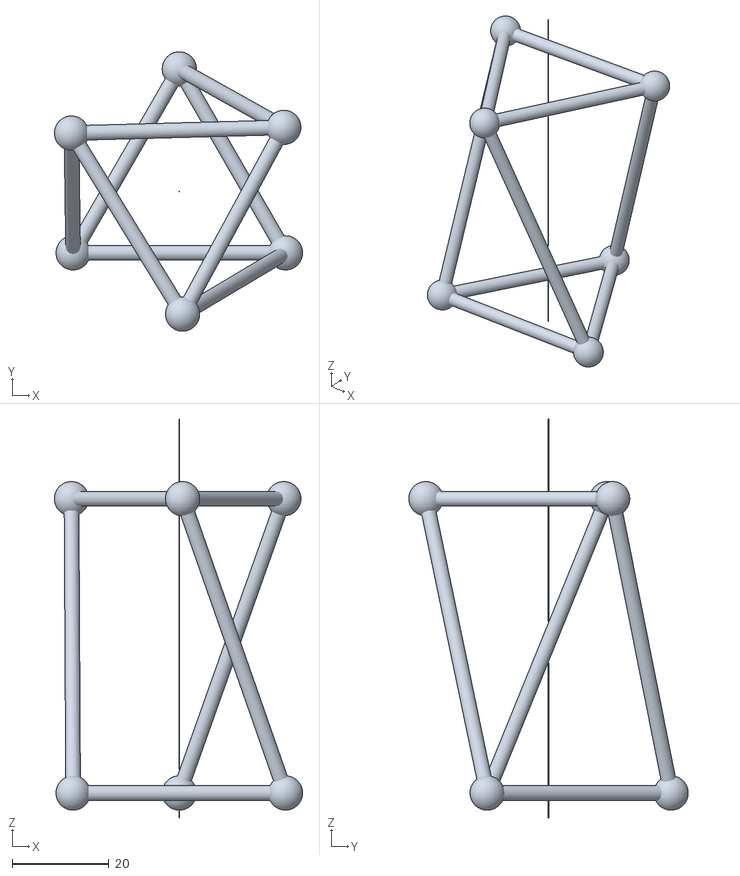
[picture p96: CAD file, 2026-08-31]
bo/replicate-study/stls/dran3/dran38-t35-cables.stl
51.3 x 57.8 x 82.5
