vertical-cloud-lab/tensegrity-optimization/bo/replicate-study/stls/dran3/dran31-t36-cables.stl

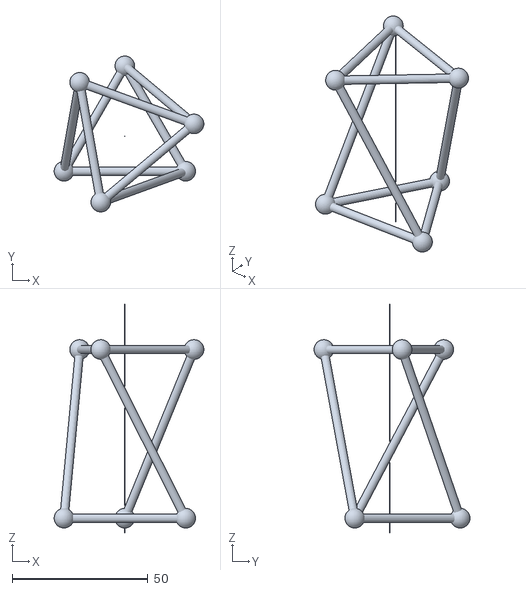
[picture p97: CAD file, 2026-08-31]
bo/replicate-study/stls/dran3/dran31-t36-cables.stl
55.1 x 57.4 x 84.0
