vertical-cloud-lab/tensegrity-optimization/bo/replicate-study/stls/dran3/dran38-t35-struts.stl

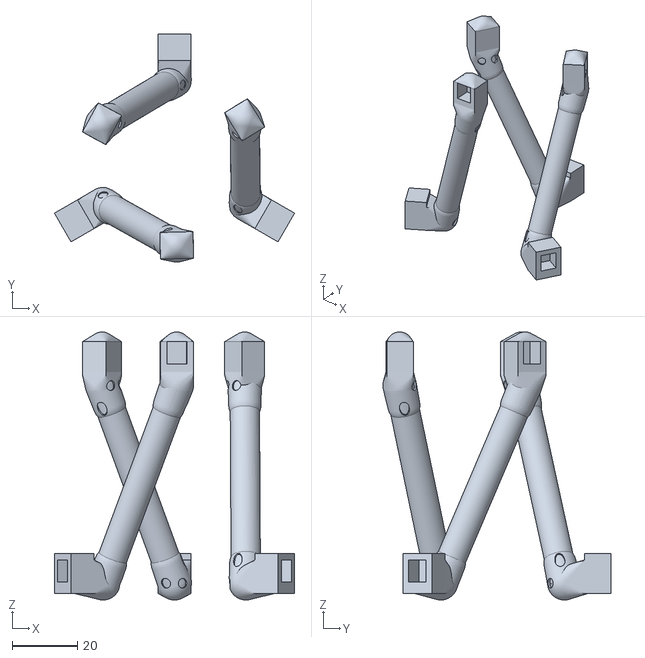
[picture p98: CAD file, 2026-08-31]
bo/replicate-study/stls/dran3/dran38-t35-struts.stl
73.9 x 70.2 x 82.4
