vertical-cloud-lab/tensegrity-optimization/bo/per-specimen-stls/t3-prism-bo-round5-t56-cables.stl

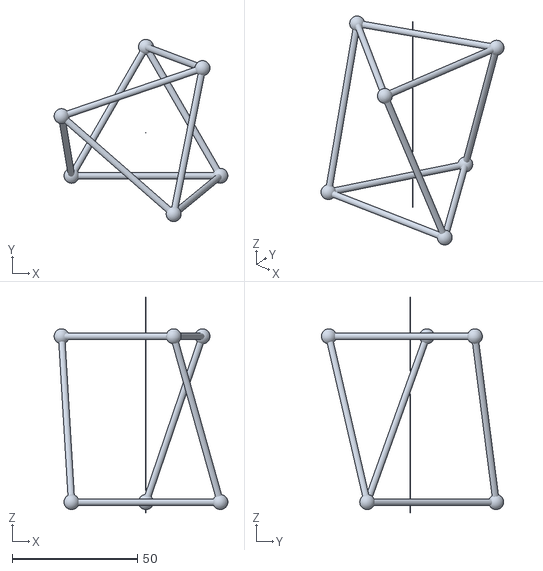
[picture p99: CAD file, 2026-09-16]
bo/per-specimen-stls/t3-prism-bo-round5-t56-cables.stl
69.2 x 72.6 x 86.1
