vertical-cloud-lab/tensegrity-optimization/bo/replicate-study/stls/dran3/dran31-t36-struts.stl

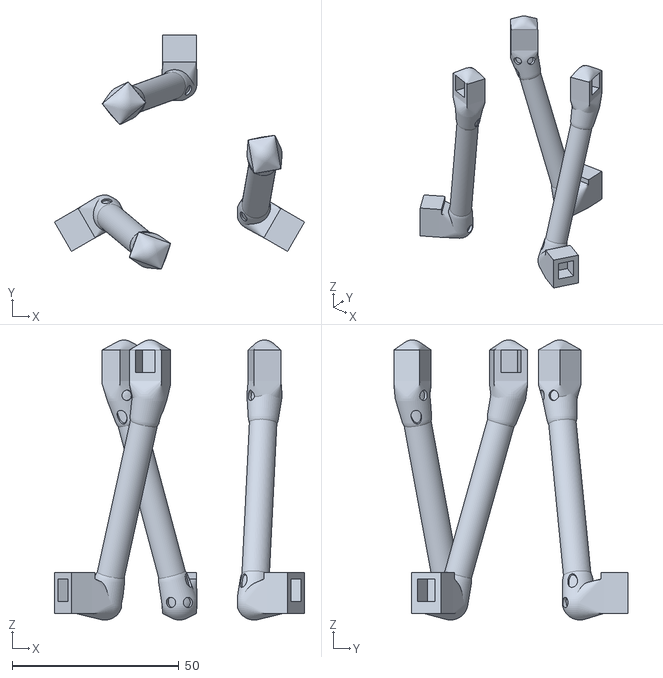
[picture p100: CAD file, 2026-08-31]
bo/replicate-study/stls/dran3/dran31-t36-struts.stl
75.0 x 70.3 x 84.0
