vertical-cloud-lab/tensegrity-optimization/bo/per-specimen-stls/t3-prism-bo-round5-t63-struts.stl

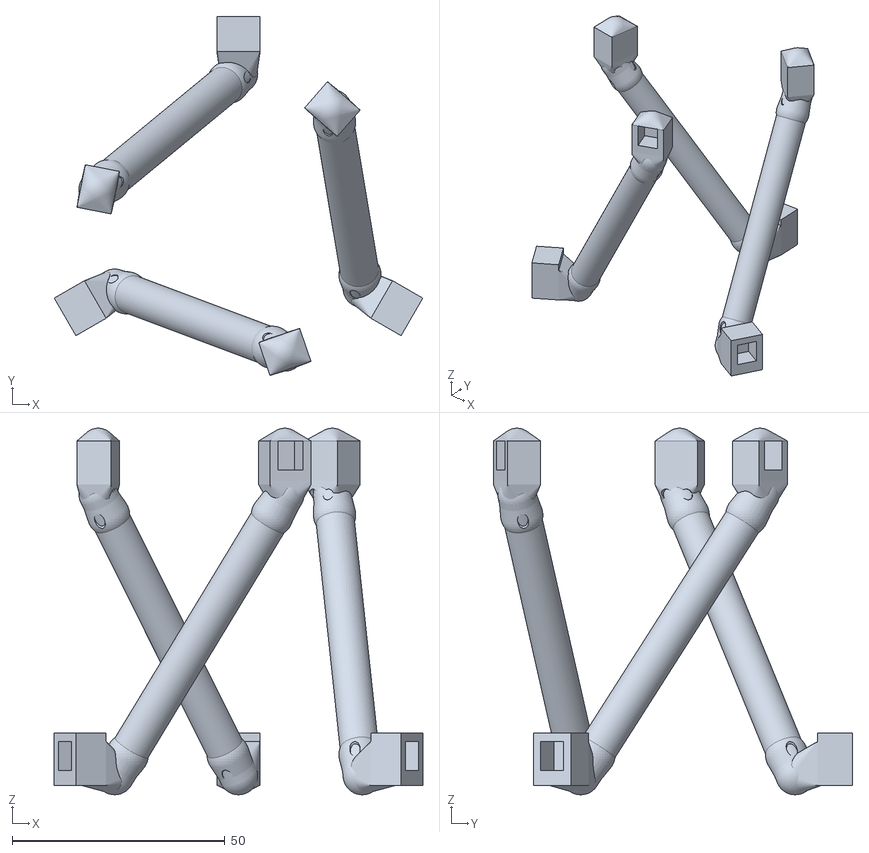
[picture p101: CAD file, 2026-09-16]
bo/per-specimen-stls/t3-prism-bo-round5-t63-struts.stl
86.7 x 84.4 x 86.2
