vertical-cloud-lab/tensegrity-optimization/bo/replicate-study/stls/dran3/dran33-t31-cables.stl

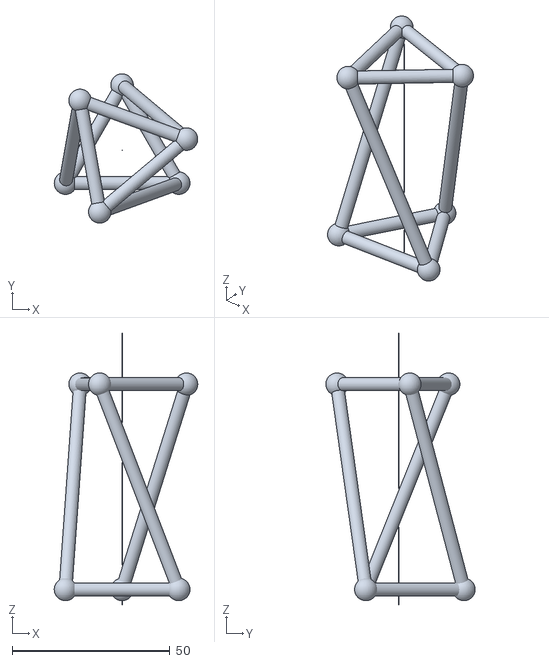
[picture p102: CAD file, 2026-08-31]
bo/replicate-study/stls/dran3/dran33-t31-cables.stl
45.5 x 47.3 x 85.9
