vertical-cloud-lab/tensegrity-optimization/bo/per-specimen-stls/t3-prism-bo-round5-t59-struts.stl

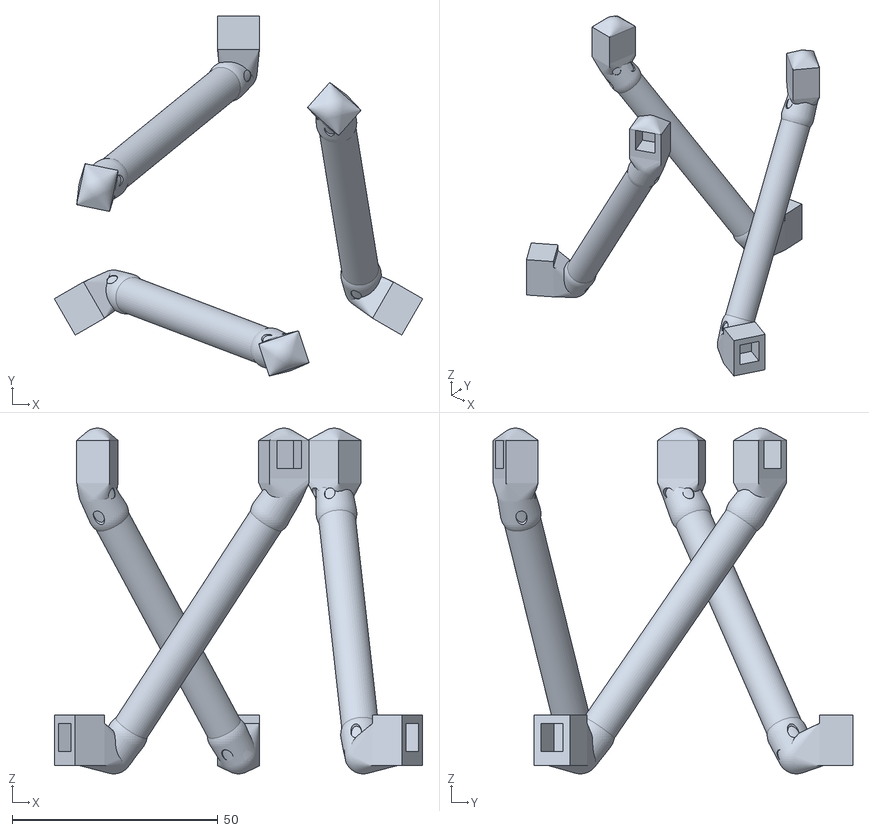
[picture p103: CAD file, 2026-09-16]
bo/per-specimen-stls/t3-prism-bo-round5-t59-struts.stl
89.6 x 87.5 x 84.1
