vertical-cloud-lab/tensegrity-optimization/bo/replicate-study/stls/dran3/dran35-t28-cables.stl

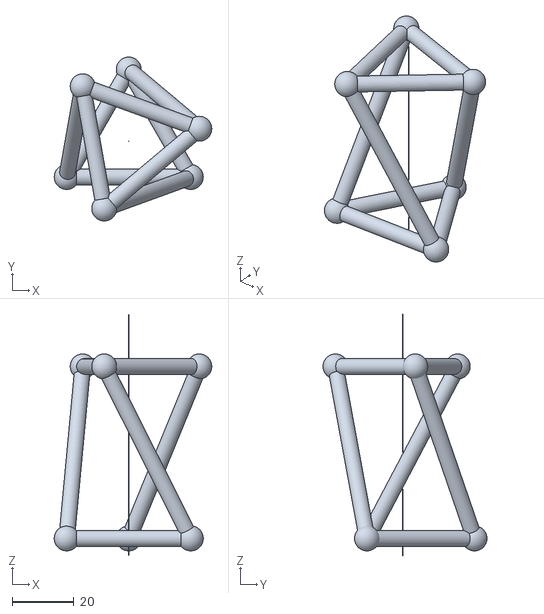
[picture p104: CAD file, 2026-08-31]
bo/replicate-study/stls/dran3/dran35-t28-cables.stl
51.1 x 53.2 x 78.1
