vertical-cloud-lab/tensegrity-optimization/bo/replicate-study/stls/dran3/dran34-t29-struts.stl

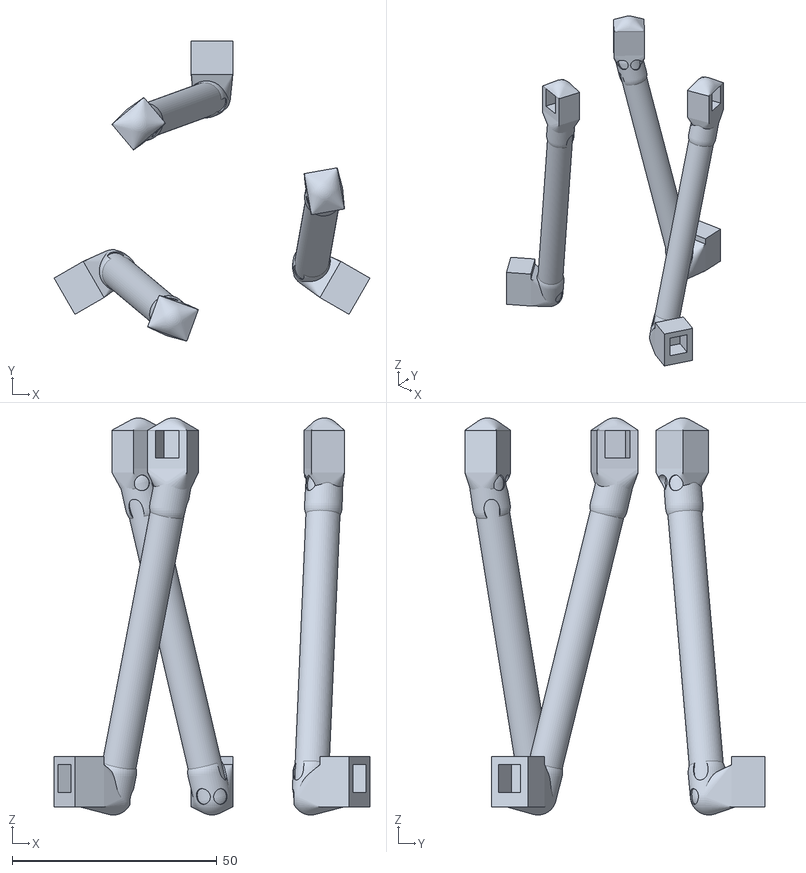
[picture p105: CAD file, 2026-08-31]
bo/replicate-study/stls/dran3/dran34-t29-struts.stl
77.1 x 73.3 x 96.8
