vertical-cloud-lab/tensegrity-optimization/bo/replicate-study/stls/dran3/dran37-t32-struts.stl

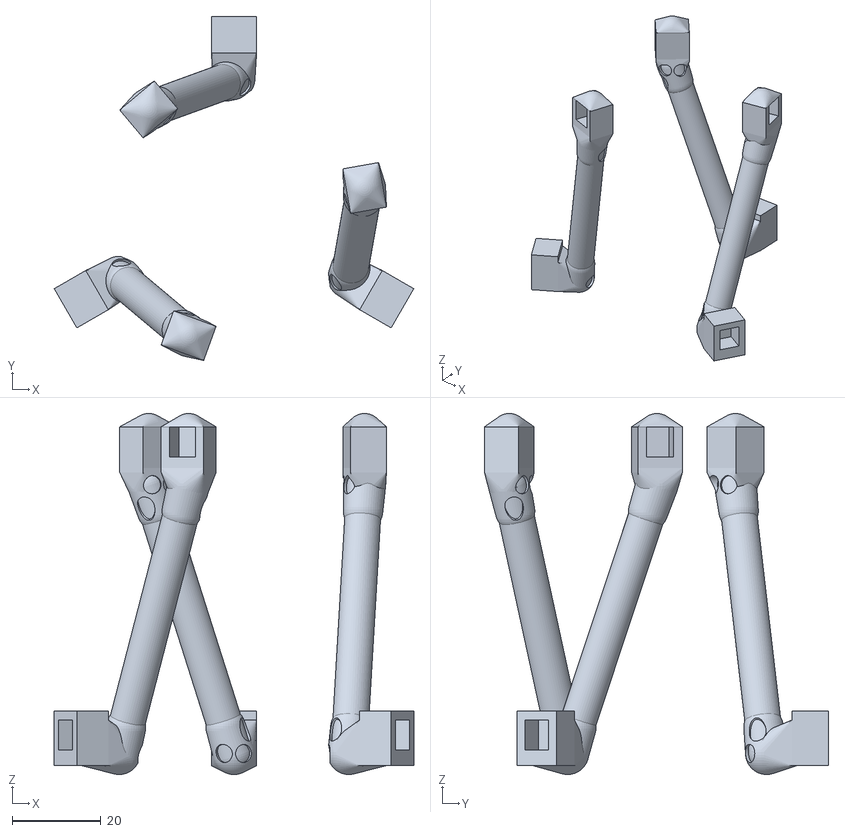
[picture p106: CAD file, 2026-08-31]
bo/replicate-study/stls/dran3/dran37-t32-struts.stl
81.0 x 77.5 x 81.3
