vertical-cloud-lab/tensegrity-optimization/bo/replicate-study/stls/dran3/dran33-t31-struts.stl

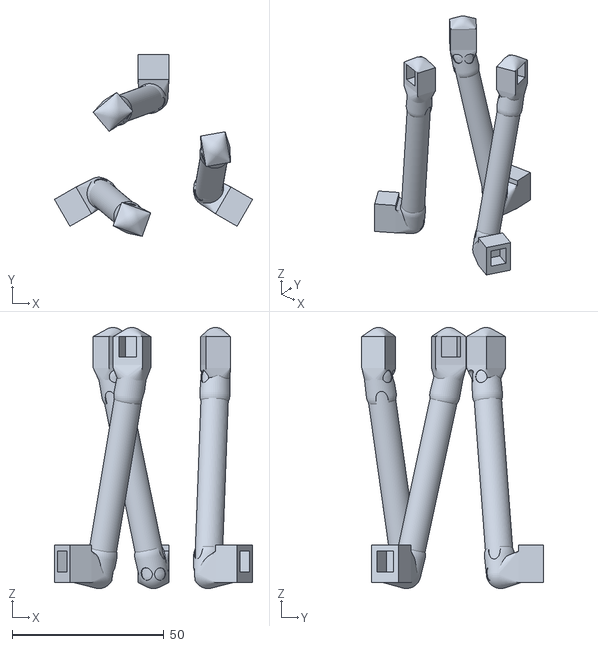
[picture p107: CAD file, 2026-08-31]
bo/replicate-study/stls/dran3/dran33-t31-struts.stl
65.2 x 59.8 x 85.9
