vertical-cloud-lab/tensegrity-optimization/bo/per-specimen-stls/t3-prism-bo-round4-t41-cables.stl

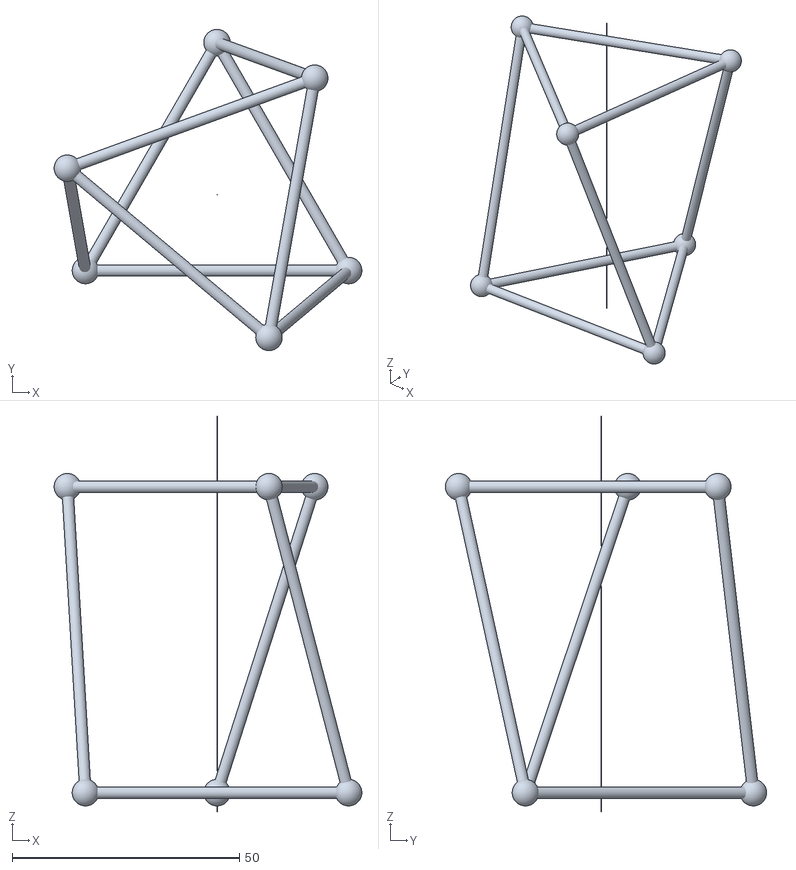
[picture p108: CAD file, 2026-09-08]
bo/per-specimen-stls/t3-prism-bo-round4-t41-cables.stl
67.7 x 70.7 x 87.1
