vertical-cloud-lab/tensegrity-optimization/bo/per-specimen-stls/t3-prism-bo-round4-t43-cables.stl

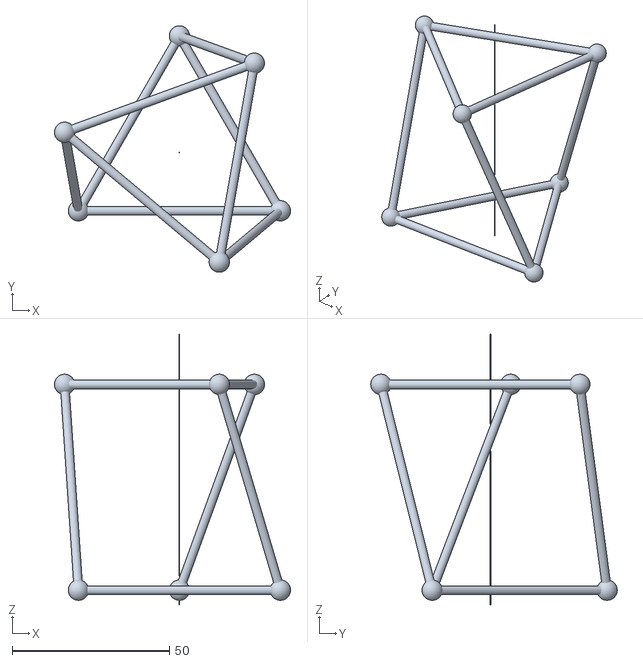
[picture p109: CAD file, 2026-09-08]
bo/per-specimen-stls/t3-prism-bo-round4-t43-cables.stl
75.1 x 78.4 x 86.2
