vertical-cloud-lab/tensegrity-optimization/bo/per-specimen-stls/t3-prism-bo-round4-t43-struts.stl

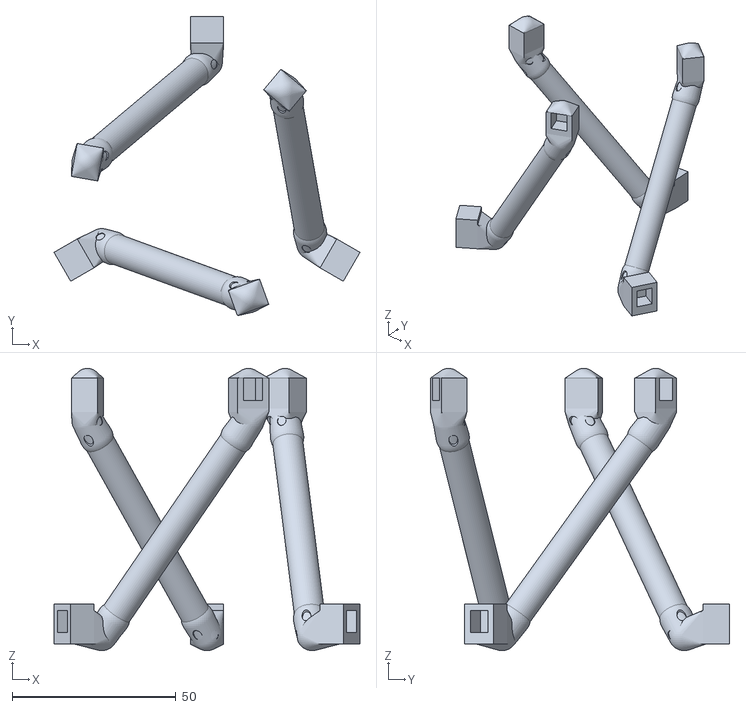
[picture p110: CAD file, 2026-09-08]
bo/per-specimen-stls/t3-prism-bo-round4-t43-struts.stl
93.5 x 91.5 x 86.2
