vertical-cloud-lab/tensegrity-optimization/bo/per-specimen-stls/t3-prism-bo-round4-t40-cables.stl

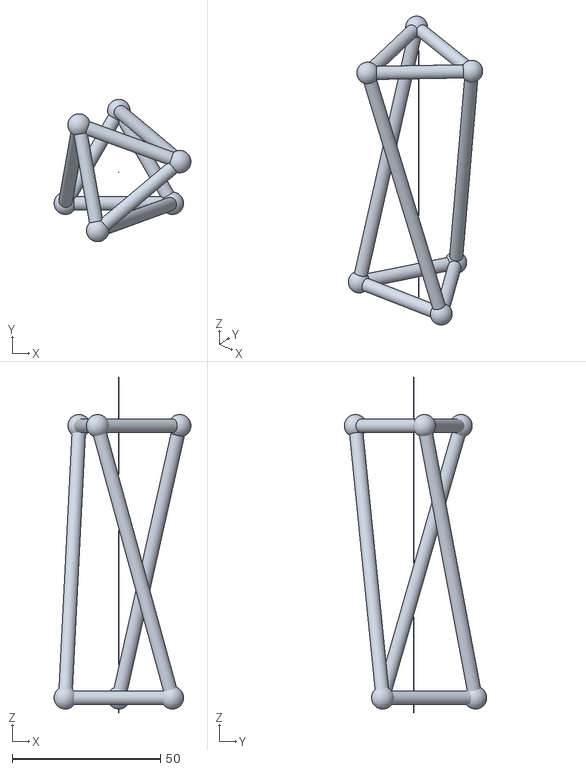
[picture p111: CAD file, 2026-09-08]
bo/per-specimen-stls/t3-prism-bo-round4-t40-cables.stl
46.1 x 48.0 x 113.2
