vertical-cloud-lab/tensegrity-optimization/bo/per-specimen-stls/t3-prism-bo-round4-t42-struts.stl

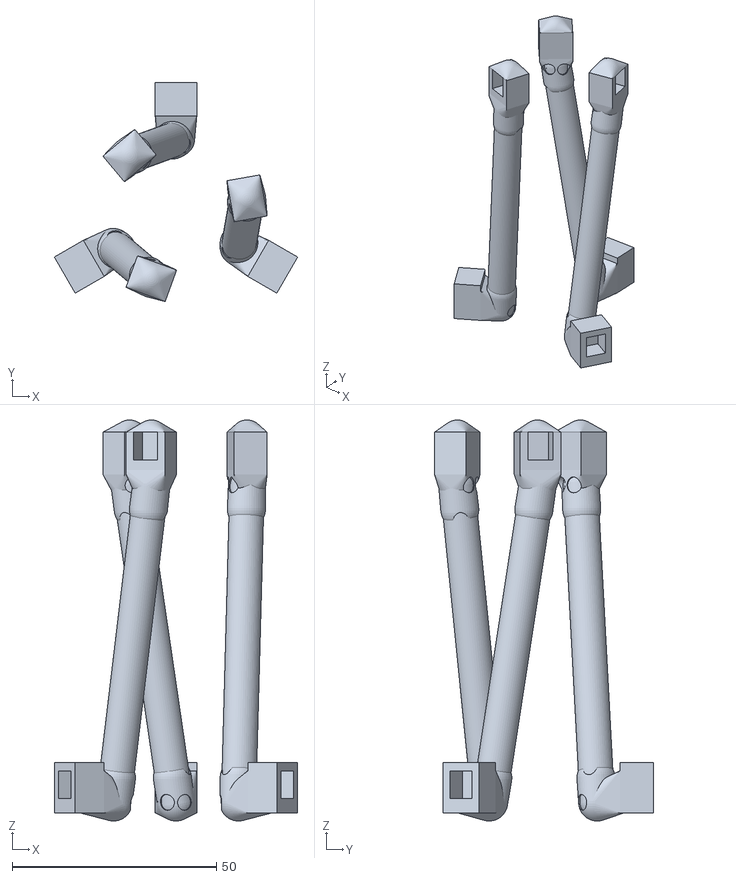
[picture p112: CAD file, 2026-09-08]
bo/per-specimen-stls/t3-prism-bo-round4-t42-struts.stl
59.5 x 53.6 x 98.1
