vertical-cloud-lab/tensegrity-optimization/bo/per-specimen-stls/t3-prism-bo-round4-t41-struts.stl

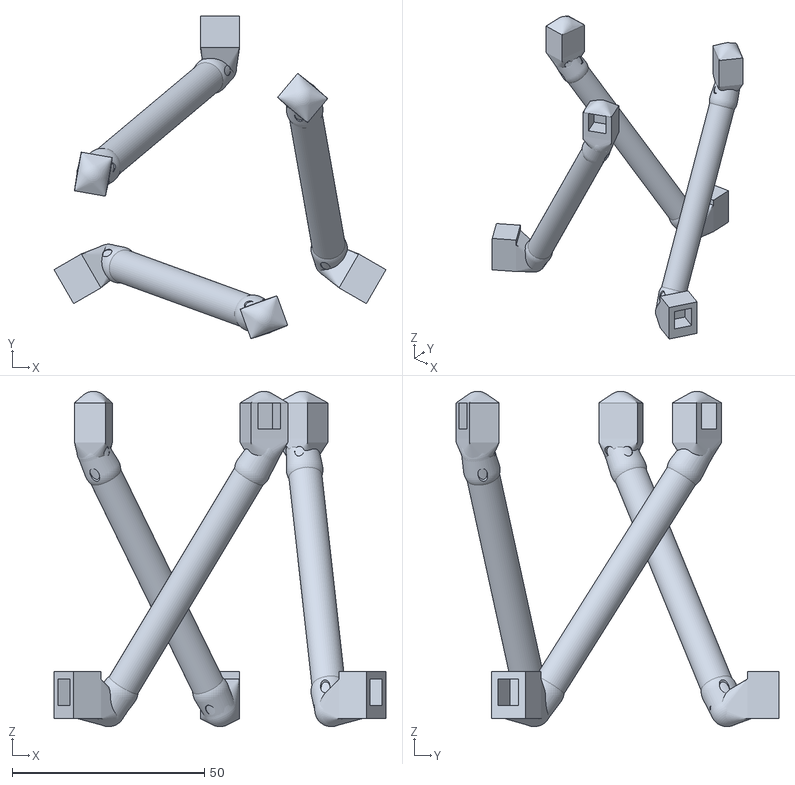
[picture p113: CAD file, 2026-09-08]
bo/per-specimen-stls/t3-prism-bo-round4-t41-struts.stl
86.3 x 83.9 x 87.2
