vertical-cloud-lab/tensegrity-optimization/bo/per-specimen-stls/t3-prism-bo-round4-t45-cables.stl

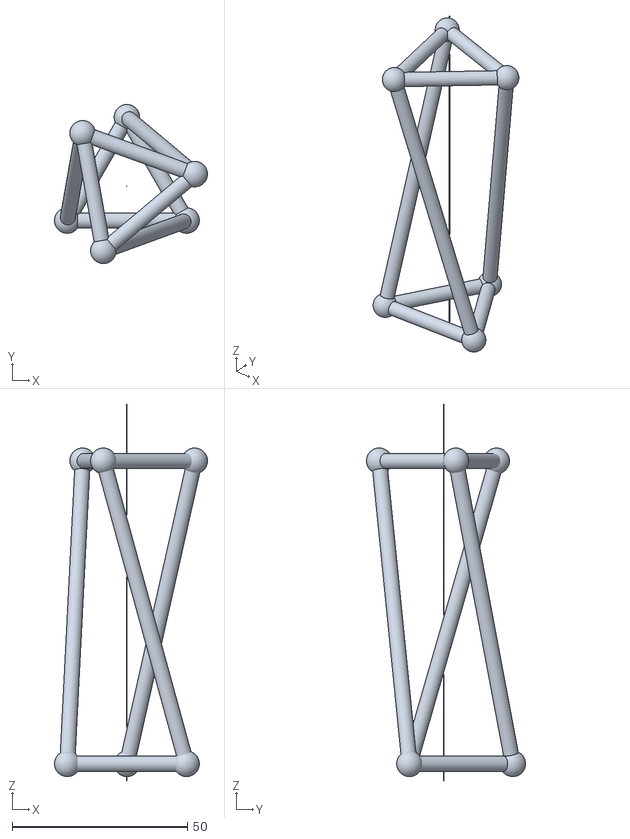
[picture p114: CAD file, 2026-09-08]
bo/per-specimen-stls/t3-prism-bo-round4-t45-cables.stl
43.7 x 45.4 x 107.6
