vertical-cloud-lab/tensegrity-optimization/bo/per-specimen-stls/t3-prism-bo-round4-t45-struts.stl

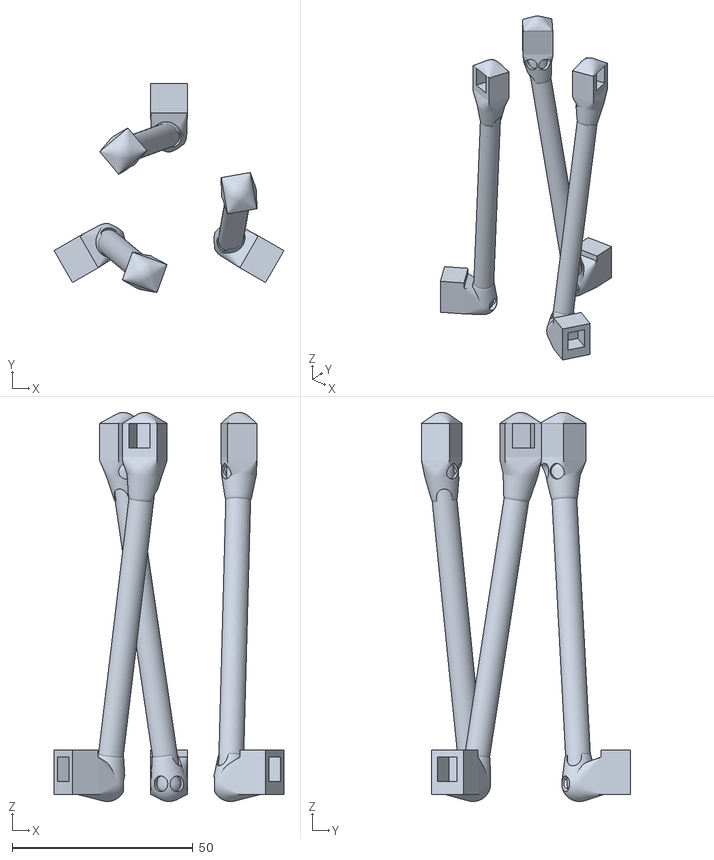
[picture p115: CAD file, 2026-09-08]
bo/per-specimen-stls/t3-prism-bo-round4-t45-struts.stl
63.6 x 57.8 x 107.6
