vertical-cloud-lab/tensegrity-optimization/bo/per-specimen-stls/t3-prism-bo-round4-t42-cables.stl

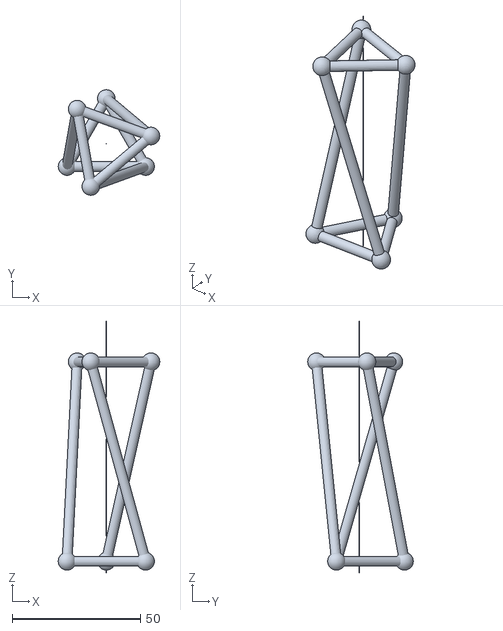
[picture p116: CAD file, 2026-09-08]
bo/per-specimen-stls/t3-prism-bo-round4-t42-cables.stl
39.5 x 41.1 x 98.1
