vertical-cloud-lab/tensegrity-optimization/bo/t3-prism-bo-batch-print-key.png

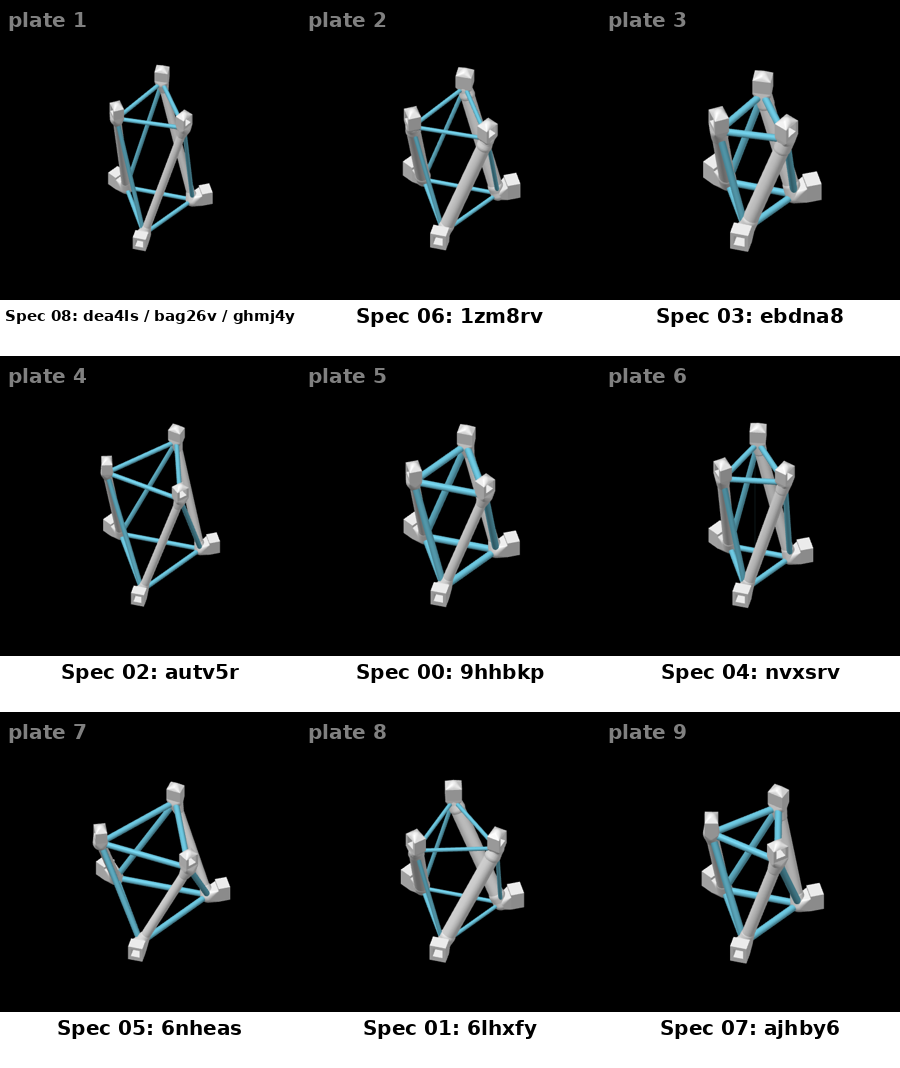
bo/t3-prism-bo-batch-print-key.png
