vertical-cloud-lab/tensegrity-optimization/bo/t3-prism-bo-batch-drop-results.csv

specimen | n_valid | dv_health | t180_mean | t180_sd | t1000_mean | t1000_sd | out_180_g_mean | out_180_g_sd | in_180_g_mean | in_180_g_sd | in_dv_ms_mean | in_dv_ms_sd | t_second_ms_mean | t_second_ms_sd | e_rebound_mean | e_rebound_sd | fn_hz_mean | fn_hz_sd | zeta_pct_mean | zeta_pct_sd | H_mm | R_mm | cable_d_mm | mass_g | spec | strut_d_mm | twist_deg
6lhxfy | 101 | healthy | 0.8930777877843858 | 0.0041554419379889575 | 0.9126730324377276 | 0.013156322051143256 | 200.0408277395844 | 4.6514371915461785 | 224.01245885825833 | 5.995658100190466 | 5.3720484060381635 | 0.09347515676322331 | 55.178585858587184 | 0.8852545005920192 | 0.05037622154824482 | 0.001053399671249343 | 368.3766929752503 | 17.11345069852911 | 10.146626604741746 | 0.9777540895501612 | 68.08 | 28.72 | 2.55 | 18.5 | 01 | 9.24 | 77.4
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
