vertical-cloud-lab/tensegrity-optimization/bo/t3-prism-bo-round1-drop-results.csv

specimen | n_valid | dv_health | t180_mean | t180_sd | t1000_mean | t1000_sd | out_180_g_mean | out_180_g_sd | in_180_g_mean | in_180_g_sd | in_dv_ms_mean | in_dv_ms_sd | t_second_ms_mean | t_second_ms_sd | e_rebound_mean | e_rebound_sd | fn_hz_mean | fn_hz_sd | zeta_pct_mean | zeta_pct_sd | t_drift_flag | t180_slope_pct_per_drop | t180_e2e_pct | H_mm | R_mm | cable_d_mm | mass_g | spec | strut_d_mm | twist_deg
r2d2c1 | 21 | healthy | 0.9941502089448192 | 0.0020547299672482 | 1.0023611455082977 | 0.0056794779703121 | 227.936356359094 | 4.343571324088003 | 229.2776534232955 | 4.345464795525673 | 5.313316582530402 | 0.1314245252006278 | 22.30315789473738 | 0.299352126944903 | 0.0205950647274666 | 0.0006130925921275 |  |  |  |  | False | -0.0001992359984331 | 0.04 | 65.52 | 27.3 | 3.28 | 19.38 | 3 | 8.08 | 80.0
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
