vertical-cloud-lab/tensegrity-optimization/bo/t3-prism-bo-round3-drop-results.csv

specimen | n_valid | dv_health | t180_mean | t180_sd | t1000_mean | t1000_sd | out_180_g_mean | out_180_g_sd | in_180_g_mean | in_180_g_sd | in_dv_ms_mean | in_dv_ms_sd | t_second_ms_mean | t_second_ms_sd | e_rebound_mean | e_rebound_sd | fn_hz_mean | fn_hz_sd | zeta_pct_mean | zeta_pct_sd | t_drift_flag | t180_slope_pct_per_drop | t180_e2e_pct | H_mm | R_mm | cable_d_mm | mass_g | spec | strut_d_mm | twist_deg | trial
drran1 | 20 | healthy | 1.03259000006491 | 0.0016495591705116 | 1.1045216126268813 | 0.0134166396687978 | 233.5817647437933 | 2.7448239298575974 | 226.21324538105208 | 2.949688721791085 | 5.408002897209085 | 0.0518026234554734 | 69.13888888889055 | 0.3043583199587435 | 0.0626912416632007 | 0.0005513971763731 | 302.3217631473501 | 2.913044206666689 | 19.11150754941097 | 1.5864867764461863 | False | 0.0236180387068908 | 0.29 | 62.11 | 25.88 | 3.11 | 19.31 | 8 | 8.27 | 40.0 | 36
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
