vertical-cloud-lab/tensegrity-optimization/bo/t3-prism-bo-round3-reprint-drop-results.csv

specimen | n_valid | dv_health | t180_mean | t180_sd | t1000_mean | t1000_sd | out_180_g_mean | out_180_g_sd | in_180_g_mean | in_180_g_sd | in_dv_ms_mean | in_dv_ms_sd | t_second_ms_mean | t_second_ms_sd | e_rebound_mean | e_rebound_sd | fn_hz_mean | fn_hz_sd | zeta_pct_mean | zeta_pct_sd | t_drift_flag | t180_slope_pct_per_drop | t180_e2e_pct | H_mm | R_mm | cable_d_mm | mass_g | spec | strut_d_mm | twist_deg | trial
2dran1 | 20 | healthy | 1.07912673342057 | 0.0036205527646270383 | 1.4730438385280202 | 0.1105671836898383 | 240.1841455801145 | 2.714210611197445 | 222.57884907593836 | 2.954423837626955 | 5.2836468986989145 | 0.04080280733742017 | 27.178888888889546 | 0.5851283307093492 | 0.025226790699420756 | 0.0006926466040385741 | 317.91134789927173 | 1.0840091469969366 | 19.040089943588914 | 0.3935918553448329 | False | 0.019797919146910717 | 0.24 | 62.11 | 25.88 | 3.11 | 19.48 | 8 | 8.27 | 40.0 | 36
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
